biologist79/ESPuino/PCBs/Wemos Lolin32/Pictures/3d-Model downside.jpg

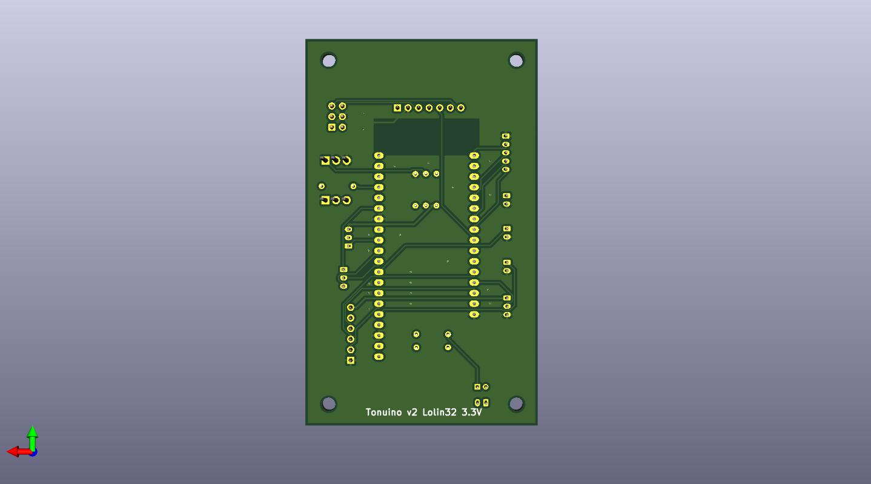
PCBs/Wemos Lolin32/Pictures/3d-Model downside.jpg
