biologist79/ESPuino/PCBs/Wemos Lolin32/Pictures/3d-Model upside.jpg

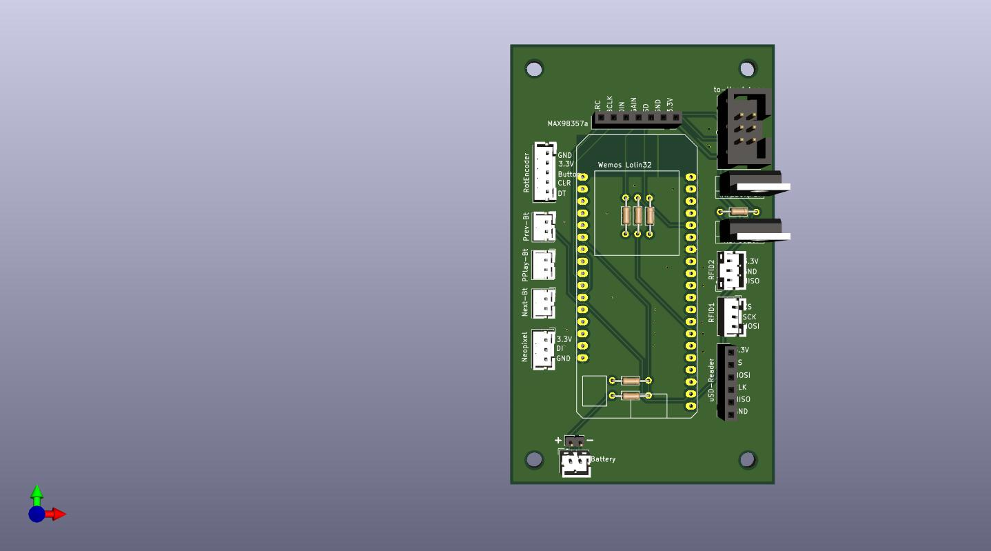
PCBs/Wemos Lolin32/Pictures/3d-Model upside.jpg
