biologist79/ESPuino/pictures/Pullup-removal.jpg

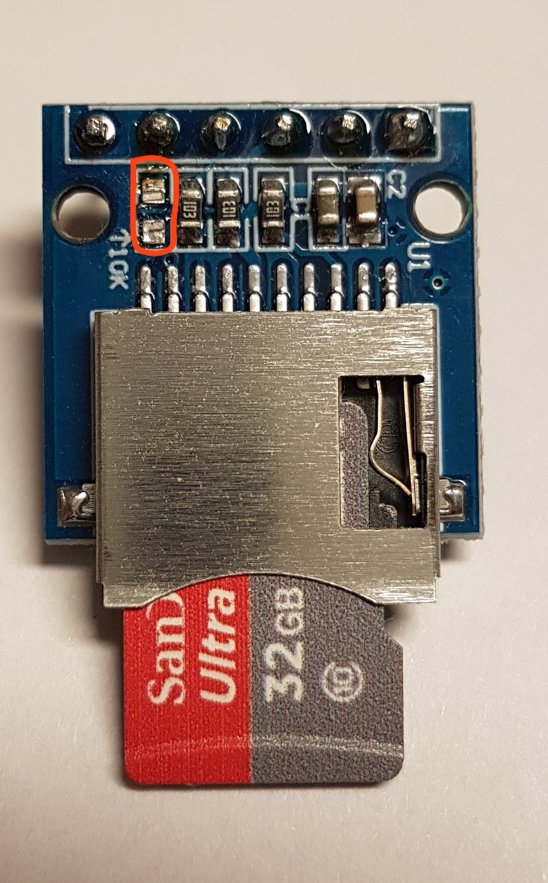
pictures/Pullup-removal.jpg
