biologist79/ESPuino/src/AudioPlayer.cpp

#include <Arduino.h>
#include "settings.h"

#include "AudioPlayer.h"

#include "Audio.h"
#include "Bluetooth.h"
#include "Cmd.h"
#include "Common.h"
#include "EnumUtils.h"
#include "Led.h"
#include "Log.h"
#include "MediaHub.h"
#include "MemX.h"
#include "Mqtt.h"
#include "Port.h"
#include "Queues.h"
#include "Rfid.h"
#include "RotaryEncoder.h"
#include "SdCard.h"
#include "System.h"
#include "VolumeCurveLut.h"
#include "Web.h"
#include "Wlan.h"
#include "main.h"
#include "strnatcmp.h"

#include <algorithm>
#include <atomic>
#include <cmath>
#include <esp_task_wdt.h>
#include <freertos/task.h>
#include <random>

// Allocate gPlayProperties in PSRAM if available
EXT_RAM_BSS_ATTR playProps gPlayProperties;

// Pending relative seek in seconds, written from the button/rotary/web tasks and drained by the audio loop.
static std::atomic<int16_t> AudioPlayer_PendingSeekSeconds {0};

void AudioPlayer_AddSeekOffset(const int16_t seconds) {
	AudioPlayer_PendingSeekSeconds.fetch_add(seconds, std::memory_order_relaxed);
}

// Seek-preview (rotary gesture, CMD_SEEK_PREVIEW): turning moves a not-yet-committed target position
// instead of jumping immediately; committed via the existing SEEK_POS_PERCENT path once the encoder is
// idle for a configurable delay, or immediately on release (see RotaryEncoder.cpp). currentRelPos must
// never be touched before the commit -- it also drives the LED progress ring, and writing the preview
// target into it early would make played-back position look like it already jumped.
static std::atomic<bool> AudioPlayer_SeekPreviewActive {false};
static std::atomic<uint8_t> AudioPlayer_SeekPreviewTargetPercent {0};
static double AudioPlayer_SeekPreviewTargetExact = 0.0; // full precision; only ever touched by the loop() task
static uint32_t AudioPlayer_SeekPreviewLastInputMs = 0; // only ever touched by the loop() task
// Cached once per gesture (in Start()), not re-read from NVS on every AudioPlayer_Loop() iteration/detent:
// the idle-commit check below runs on every single loop() cycle for as long as a gesture is held, and a
// NVS getUShort/getUChar still costs a mutex lock + key lookup each time even though it's RAM-cached.
static uint16_t AudioPlayer_SeekPreviewDelayMsCached = 2000;
static uint8_t AudioPlayer_SeekPreviewSweepCached = 40;

void AudioPlayer_SeekPreviewStart(void) {
	if (gPlayProperties.audioFileDuration == 0) {
		return; // no meaningful target for webstreams / unknown-length content
	}
	AudioPlayer_SeekPreviewDelayMsCached = gPrefsSettings.getUShort("seekPrevDelay", 2000);
	AudioPlayer_SeekPreviewSweepCached = gPrefsSettings.getUChar("seekPrevSweep", 40);
	if (AudioPlayer_SeekPreviewSweepCached < 1) {
		AudioPlayer_SeekPreviewSweepCached = 1; // guard against divide-by-zero in AudioPlayer_SeekPreviewAdjust
	}
	AudioPlayer_SeekPreviewTargetExact = gPlayProperties.currentRelPos; // start from where playback is, not 0
	AudioPlayer_SeekPreviewTargetPercent.store(static_cast<uint8_t>(std::lround(AudioPlayer_SeekPreviewTargetExact)), std::memory_order_relaxed);
	AudioPlayer_SeekPreviewLastInputMs = millis();
	AudioPlayer_SeekPreviewActive.store(true, std::memory_order_relaxed);
}

void AudioPlayer_SeekPreviewAdjust(const int32_t detents) {
	if (!AudioPlayer_SeekPreviewActive.load(std::memory_order_relaxed)) {
		return;
	}
	AudioPlayer_SeekPreviewTargetExact = std::clamp(AudioPlayer_SeekPreviewTargetExact + (detents * 100.0 / AudioPlayer_SeekPreviewSweepCached), 0.0, 100.0);
	AudioPlayer_SeekPreviewTargetPercent.store(static_cast<uint8_t>(std::lround(AudioPlayer_SeekPreviewTargetExact)), std::memory_order_relaxed);
	AudioPlayer_SeekPreviewLastInputMs = millis();
}

void AudioPlayer_SeekPreviewCommit(void) {
	if (!AudioPlayer_SeekPreviewActive.load(std::memory_order_relaxed)) {
		return;
	}
	gPlayProperties.currentRelPos = AudioPlayer_SeekPreviewTargetPercent.load(std::memory_order_relaxed);
	gPlayProperties.seekmode = SEEK_POS_PERCENT;
	AudioPlayer_SeekPreviewActive.store(false, std::memory_order_relaxed);
}

void AudioPlayer_SeekPreviewCancel(void) {
	AudioPlayer_SeekPreviewActive.store(false, std::memory_order_relaxed);
}

bool AudioPlayer_IsSeekPreviewActive(void) {
	return AudioPlayer_SeekPreviewActive.load(std::memory_order_relaxed);
}

uint8_t AudioPlayer_GetSeekPreviewTargetPercent(void) {
	return AudioPlayer_SeekPreviewTargetPercent.load(std::memory_order_relaxed);
}

// Playlist
static playlistSortMode AudioPlayer_PlaylistSortMode = AUDIOPLAYER_PLAYLIST_SORT_MODE_DEFAULT;

// Volume
static uint8_t AudioPlayer_CurrentVolume = AUDIOPLAYER_VOLUME_INIT;
static uint8_t AudioPlayer_MaxVolume = AUDIOPLAYER_VOLUME_MAX;
static uint8_t AudioPlayer_MaxVolumeSpeaker = AUDIOPLAYER_VOLUME_MAX;
static uint8_t AudioPlayer_MinVolume = AUDIOPLAYER_VOLUME_MIN;
static uint8_t AudioPlayer_InitVolume = AUDIOPLAYER_VOLUME_INIT;
// Night-mode volume limit, see AudioPlayer_ApplyNightVolumeCap(). The cap is purely transient: armed
// when night mode starts, dropped when it ends, never persisted -- night mode is always off after a
// restart anyway.
static uint8_t AudioPlayer_NightVolumeCap = 0u; // 0 = no cap active
static bool AudioPlayer_NightVolumeLimitEnabled = false;

// current playtime
uint32_t AudioPlayer_CurrentTime = 0;
uint32_t AudioPlayer_FileDuration = 0;

// Playtime stats
time_t playTimeSecTotal = 0;
time_t playTimeSecSinceStart = 0;

// current station logo url
static String AudioPlayer_StationLogoUrl;

#ifdef HEADPHONE_ADJUST_ENABLE
static bool AudioPlayer_HeadphoneLastDetectionState;
static uint32_t AudioPlayer_HeadphoneLastDetectionTimestamp = 0u;
static uint8_t AudioPlayer_MaxVolumeHeadphone = 11u; // Maximum volume that can be adjusted in headphone-mode (default; can be changed later via GUI)
#endif

static bool AudioPlayer_IsHeadphoneModeActive() {
#ifdef HEADPHONE_ADJUST_ENABLE
	const bool wiredHeadphoneConnected = !Audio_Detect_Mode_HP(Port_Read(HP_DETECT));
#else
	const bool wiredHeadphoneConnected = false;
#endif

	const bool bluetoothHeadphoneConnected = (System_GetOperationMode() == OPMODE_BLUETOOTH_SOURCE) && Bluetooth_Device_Connected();

	return wiredHeadphoneConnected || bluetoothHeadphoneConnected;
}

// dummy class to allocate audio object in PSRAM if available
class AudioCustom : public Audio {
public:
	void *operator new(size_t size) {
		return psramFound() ? ps_malloc(size) : malloc(size);
	}
};

Audio *audio = nullptr;

// new old varibles
constexpr uint32_t playbackTimeout = 2000;
uint32_t playbackTimeoutStart = millis();
uint8_t currentVolume;
BaseType_t trackQStatus = pdFAIL;
uint8_t trackCommand = NO_ACTION;
bool audioReturnCode;
uint32_t AudioPlayer_LastPlaytimeStatsTimestamp = 0u;
// Announcement state (see AudioPlayer_PlayAnnouncement). The decoder is briefly pointed at another
// file while gPlayProperties -- playlist, track number, play mode -- stays exactly as it is, so the
// only thing that has to be remembered is the position inside the interrupted track.
static uint32_t AudioPlayer_announcementResumePos = 0; // seconds into the interrupted track
static uint32_t AudioPlayer_announcementStartedAt = 0; // millis() when it started, for the watchdog
// Backstop in case evt_eof never arrives (a file that opens but decodes to nothing): without it the
// music would stay silent forever, which is worse than a crash because nothing points at the cause.
static constexpr uint32_t announcementTimeoutMs = 30000;

static uint32_t AudioPlayer_resumeSeekPendingSecs = 0; // deferred resume-seek target (seconds); 0 = none pending (declared early: used by the audio_info evt_bitrate callback above AudioPlayer_Loop)
Playlist *newPlayList = nullptr;
bool newPlayListAvailable = false;

static bool AudioPlayer_UploadActive = false;
static bool AudioPlayer_WasPausedBeforeUpload = false; // remember pre-upload pause state
static bool gResetOldRfidOnIdle = false; // release the "don't accept same rfid twice"-lock on next idle-state

// Remember an RFID-tag whose webstream could not be started because WiFi is not (yet) connected, so it can
// be re-injected into the RFID-queue once WiFi is up (see handleWifiStateConnectionSuccess() in Wlan.cpp).
static void AudioPlayer_RememberRfidForWifiRetry(const char *rfidTagId) {
	strncpy(gRetryRfidTagId, rfidTagId, cardIdStringSize - 1);
	gRetryRfidTagId[cardIdStringSize - 1] = '\0';
	gRetryRfidOnWifiConnect = true;
}

// "Arm" the release of the dontAcceptRfidTwice-lock: called by the RFID-handler the moment a new
// tag is accepted, it records that this playback-attempt happened. The lock is then actually released the
// next time the player becomes idle (see AudioPlayer_Cyclic()), which re-allows the same tag to be applied
// again. Arming on acceptance - rather than on playback becoming active - is deliberate: it ensures the
// release still fires even if the very first track fails immediately (e.g. a webstream applied before WiFi
// is connected), which would otherwise leave the tag locked forever.
void AudioPlayer_ArmRfidResetOnIdle(void) {
	gResetOldRfidOnIdle = true;
}

static void AudioPlayer_HeadphoneVolumeManager(void);
static std::optional<Playlist *> AudioPlayer_ReturnPlaylistFromWebstream(const char *_webUrl);
static bool AudioPlayer_ArrSortHelper_strcmp(const char *a, const char *b);
static bool AudioPlayer_ArrSortHelper_strnatcmp(const char *a, const char *b);
static bool AudioPlayer_ArrSortHelper_strnatcasecmp(const char *a, const char *b);
static void AudioPlayer_SortPlaylist(Playlist *playlist);
static void AudioPlayer_RandomizePlaylist(Playlist *playlist);
static size_t AudioPlayer_NvsRfidWriteWrapper(const char *_rfidCardId, const uint32_t _playPosition, const uint8_t _playMode, const uint16_t _trackLastPlayed);
static void AudioPlayer_ClearCover(void);
static void audio_id3image(File &file, const size_t pos, const size_t size);
static void audio_oggimage(File &file, std::vector<uint32_t> v);

void AudioPlayer_NotifyUploadStart(void) {
	if (AudioPlayer_UploadActive) {
		return; // already suspended – ignore nested calls
	}
	AudioPlayer_UploadActive = true;
	if (!gPlayProperties.pausePlay && gPlayProperties.playMode != NO_PLAYLIST && gPlayProperties.playMode != BUSY) {
		AudioPlayer_WasPausedBeforeUpload = false;
		audio->pauseResume();
	} else {
		AudioPlayer_WasPausedBeforeUpload = true; // was already paused / idle
	}
}

void AudioPlayer_NotifyUploadEnd(void) {
	if (!AudioPlayer_UploadActive) {
		return;
	}
	if (!AudioPlayer_WasPausedBeforeUpload) {
		audio->pauseResume();
	}
	AudioPlayer_UploadActive = false;
}

void Audio_InfoCallback(Audio::msg_t m) {
	switch (m.e) {
		case Audio::evt_info: {
			// Log_Printf(LOGLEVEL_INFO, "info:         %s", m.msg); // disabled to reduce log especially from files with numerous comments
			if (startsWith((char *) m.msg, "slow stream, dropouts")) {
				// websocket notify for slow stream
				Web_SendWebsocketData(0, WebsocketCodeType::Dropout);
			}
			break;
		}
		case Audio::evt_eof: { // end of file
			Log_Printf(LOGLEVEL_INFO, "end of file:  %s", m.msg);
			gPlayProperties.trackFinished = true;
			gPlayProperties.currentSpeechActive = false;
			break;
		}
		case Audio::evt_bitrate: {
			Log_Printf(LOGLEVEL_INFO, "bitrate:      %s", m.msg);
			// Deferred audiobook resume-seek. connecttoFS(fileStartTime) only seeks files whose
			// Xing/VBR header sets m_nominal_bitrate; headerless CBR audiobooks are never seeked and
			// restart from 0. This event fires once the measured average bitrate has *stabilised*, so
			// setAudioPlayTime() now lands accurately and the lib re-syncs the reported play-time to
			// match (seeking earlier, before the bitrate settles, both mis-positions and desyncs the
			// clock). Guards: only when a resume is pending, the target is within the file, and we are
			// not already there (a VBR file the lib already positioned at connect).
			if (AudioPlayer_resumeSeekPendingSecs > 0 && audio != nullptr) {
				const uint32_t target = AudioPlayer_resumeSeekPendingSecs;
				AudioPlayer_resumeSeekPendingSecs = 0; // one-shot regardless of outcome
				if (target < audio->getAudioFileDuration() && target > audio->getAudioCurrentTime() + 3) {
					if (audio->setAudioPlayTime(target)) {
						Log_Printf(LOGLEVEL_NOTICE, "Resume: deferred seek to position %u", target);
					}
				}
			}
			break;
		}
		case Audio::evt_icyurl: {
			Log_Printf(LOGLEVEL_INFO, "icy URL:      %s", m.msg);
			if (m.msg && m.msg[0] != '\0' && AudioPlayer_StationLogoUrl.isEmpty()) {
				// has station homepage, get favicon url
				AudioPlayer_StationLogoUrl = "https://www.google.com/s2/favicons?sz=256&domain_url=" + String(m.msg);
				// websocket and mqtt notify station logo has changed
				Web_SendWebsocketData(0, WebsocketCodeType::CoverImg);
			}
			break;
		}
		case Audio::evt_id3data: {
			if (!m.msg) {
				break;
			}
			// Log_Printf(LOGLEVEL_INFO, "ID3 data:     %s", m.msg); // disabled to prevent log spam from files with numerous metadata
			// get title
			if (startsWith((char *) m.msg, "Title") || startsWith((char *) m.msg, "TITLE=") || startsWith((char *) m.msg, "title=")) { // ID3v1, ID3v2.3 and ID3v2.4: "Title:", VORBISCOMMENT: "TITLE=", "title=", "Title="
				int titleStart = 6;
				if (m.msg[5] == '/') { // ID3v2.2 "Title/Songname/Content description:"
					titleStart = 36;
				}
				if (gPlayProperties.playlist->size() > 1) {
					Audio_setTitle("(%u/%u): %s", gPlayProperties.currentTrackNumber + 1, gPlayProperties.playlist->size(), m.msg + titleStart);
				} else {
					Audio_setTitle("%s", m.msg + titleStart);
				}
			}
			break;
		}
		case Audio::evt_lasthost: { // stream URL played
			Log_Printf(LOGLEVEL_INFO, "last URL:     %s", m.msg);
			break;
		}
		case Audio::evt_name: { // station name or icy-name
			Log_Printf(LOGLEVEL_NOTICE, "station name: %s", m.msg);
			if (m.msg && m.msg[0] != '\0') {
				if (gPlayProperties.playlist->size() > 1) {
					Audio_setTitle("(%u/%u): %s", gPlayProperties.currentTrackNumber + 1, gPlayProperties.playlist->size(), m.msg);
				} else {
					Audio_setTitle("%s", m.msg);
				}
			}
			break;
		}
		case Audio::evt_streamtitle: {
			if (!gPlayProperties.isWebstream) {
				break; // prevents overwriting correct title for local files
			}
			Log_Printf(LOGLEVEL_INFO, "stream title: %s", m.msg);
			if (m.msg && m.msg[0] != '\0') {
				if (gPlayProperties.playlist->size() > 1) {
					Audio_setTitle("(%u/%u): %s", gPlayProperties.currentTrackNumber + 1, gPlayProperties.playlist->size(), m.msg);
				} else {
					Audio_setTitle("%s", m.msg);
				}
			}
			break;
		}
		case Audio::evt_icylogo: { // logo
			Log_Printf(LOGLEVEL_INFO, "icy logo:     %s", m.msg);
			if (m.msg && m.msg[0] != '\0') {
				AudioPlayer_StationLogoUrl = m.msg;
				// websocket and mqtt notify station logo has changed
				Web_SendWebsocketData(0, WebsocketCodeType::CoverImg);
			}
			break;
		}
		case Audio::evt_image: {
			if (!gPlayProperties.playlist || gPlayProperties.currentTrackNumber >= gPlayProperties.playlist->size()) {
				break;
			}
			const char *fileName = gPlayProperties.playlist->at(gPlayProperties.currentTrackNumber);
			File file = gFSystem.open(fileName, FILE_READ);
			if (!file) {
				Log_Printf(LOGLEVEL_ERROR, "Failed to open file: %s", fileName);
				break;
			}
			char fileType[4];
			if (file.readBytes(fileType, 4) == 4) {
				if (strncmp(fileType, "OggS", 4) == 0) {
					audio_oggimage(file, m.vec1);
				} else {
					audio_id3image(file, m.vec1[0], m.vec1[1]);
				}
			}
			file.close();
			break;
		}
		default: // ignored events: evt_icydescription, evt_lyrics, evt_log
			break;
	}
}

float Audio_GetVolume(float t) {
	uint8_t curve_type = gPrefsSettings.getUChar("volumeCurve", 0);

	// 1. Safety Checks
	if (curve_type >= VOL_LUT_CURVES) {
		curve_type = VOL_CURVE_PERCEPTUAL;
	}
	if (t <= 0.0f) {
		return pgm_read_float(&(VOLUME_TABLE[curve_type][0]));
	}

	// 2. Calculate indices
	float index_f = t * (VOL_LUT_STEPS - 1);
	int index = (int) index_f;

	// Safety clamp for the edge case where index_f is exactly 63.0
	if (index >= VOL_LUT_STEPS - 1) {
		return pgm_read_float(&(VOLUME_TABLE[curve_type][VOL_LUT_STEPS - 1]));
	}

	float fraction = index_f - (float) index;

	// 3. Interpolate
	float val1 = pgm_read_float(&(VOLUME_TABLE[curve_type][index]));
	float val2 = pgm_read_float(&(VOLUME_TABLE[curve_type][index + 1]));

	return val1 + (val2 - val1) * fraction;
}

// Applies the tone/equalizer gains and keeps the audio library's per-sample IIR tone filter enabled
// only while the equalizer is actually non-flat. With a flat EQ (all gains 0, the default) the filter
// would just pass the signal through unchanged, so running it per output sample is wasted CPU on core 1
// -- the same core loop() polls buttons/rotary on, which is why heavy decoders (AAC/m4a) starve input.
// See https://forum.espuino.de/t/keine-bedienung-bei-bestimmten-dateien-moeglich/4675
static void AudioPlayer_ApplyTone(int8_t gainLowPass, int8_t gainBandPass, int8_t gainHighPass) {
	audio->settings.IIR_FILTER = (gainLowPass != 0 || gainBandPass != 0 || gainHighPass != 0);
	audio->setTone(gainLowPass, gainBandPass, gainHighPass);
}

void AudioPlayer_Init(void) {
	// create audio object
	audio = new AudioCustom();

	// load playtime total from NVS
	playTimeSecTotal = gPrefsSettings.getULong("playTimeTotal", 0);

	uint8_t playListSortModeValue = gPrefsSettings.getUChar("PLSortMode", EnumUtils::underlying_value(AudioPlayer_PlaylistSortMode));
	AudioPlayer_PlaylistSortMode = EnumUtils::to_enum<playlistSortMode>(playListSortModeValue);

	uint32_t nvsInitialVolume;
	if (!gPrefsSettings.getBool("recoverVolBoot", false)) {
		// Get initial volume from NVS
		nvsInitialVolume = gPrefsSettings.getUInt("initVolume", 0);
	} else {
		// Get volume used at last shutdown
		nvsInitialVolume = gPrefsSettings.getUInt("previousVolume", 999);
		if (nvsInitialVolume == 999) {
			gPrefsSettings.putUInt("previousVolume", AudioPlayer_GetInitVolume());
			nvsInitialVolume = AudioPlayer_GetInitVolume();
		} else {
			Log_Println(rememberLastVolume, LOGLEVEL_ERROR);
		}
	}

	if (nvsInitialVolume) {
		AudioPlayer_SetInitVolume(nvsInitialVolume);
		Log_Printf(LOGLEVEL_INFO, restoredInitialLoudnessFromNvs, nvsInitialVolume);
	} else {
		gPrefsSettings.putUInt("initVolume", AudioPlayer_GetInitVolume());
		Log_Println(wroteInitialLoudnessToNvs, LOGLEVEL_ERROR);
	}

	// Get maximum volume for speaker from NVS
	uint32_t nvsMaxVolumeSpeaker = gPrefsSettings.getUInt("maxVolumeSp", 0);
	if (nvsMaxVolumeSpeaker) {
		AudioPlayer_SetMaxVolumeSpeaker(nvsMaxVolumeSpeaker);
		AudioPlayer_SetMaxVolume(nvsMaxVolumeSpeaker);
		Log_Printf(LOGLEVEL_INFO, restoredMaxLoudnessForSpeakerFromNvs, nvsMaxVolumeSpeaker);
	} else {
		// Set max volume to max per default. Can be adjusted later via webinterface.
		gPrefsSettings.putUInt("maxVolumeSp", 21);
		Log_Println(wroteMaxLoudnessForSpeakerToNvs, LOGLEVEL_ERROR);
	}

	// Get minimum volume from NVS. Unlike the max values, 0 (= AUDIOPLAYER_VOLUME_MIN) is a perfectly
	// valid setting and in fact the default, so a plain read-with-default is used instead of the
	// "0 means unset, write default" pattern above. AudioPlayer_SetVolume() clamps every volume change
	// to this floor, so a non-zero value takes effect for all volume sources (rotary, buttons, BT, web).
	AudioPlayer_SetMinVolume(gPrefsSettings.getUInt("minVolume", AUDIOPLAYER_VOLUME_MIN));

	// Night-mode volume limit: off by default, so nothing changes for existing devices.
	AudioPlayer_NightVolumeLimitEnabled = gPrefsSettings.getBool("nightVolLimit", false);

#ifdef HEADPHONE_ADJUST_ENABLE
	#if (HP_DETECT >= 0 && HP_DETECT <= MAX_GPIO)
	pinMode(HP_DETECT, INPUT_PULLUP);
	#endif
	AudioPlayer_HeadphoneLastDetectionState = Audio_Detect_Mode_HP(Port_Read(HP_DETECT));

	// Get maximum volume for headphone from NVS
	uint32_t nvsAudioPlayer_MaxVolumeHeadphone = gPrefsSettings.getUInt("maxVolumeHp", 0);
	if (nvsAudioPlayer_MaxVolumeHeadphone) {
		AudioPlayer_MaxVolumeHeadphone = nvsAudioPlayer_MaxVolumeHeadphone;
		Log_Printf(LOGLEVEL_INFO, restoredMaxLoudnessForHeadphoneFromNvs, nvsAudioPlayer_MaxVolumeHeadphone);
	} else {
		// Set max volume to max per default. Can be adjusted later via webinterface.
		gPrefsSettings.putUInt("maxVolumeHp", 21);
		Log_Println(wroteMaxLoudnessForHeadphoneToNvs, LOGLEVEL_ERROR);
	}
#endif
	// Adjust volume depending on headphone is connected and volume-adjustment is enabled
	AudioPlayer_SetupVolumeAndAmps();

	// initialize gPlayProperties
	gPlayProperties = {};
	gPlayProperties.playlistFinished = true;
	gPlayProperties.jumpToFolderTrack = -1;
	gPlayProperties.gainLowPass = 0;
	gPlayProperties.gainBandPass = 0;
	gPlayProperties.gainHighPass = 0;

	// clear title and cover image
	gPlayProperties.title[0] = '\0';
	gPlayProperties.coverFilePos = 0;
	AudioPlayer_StationLogoUrl = "";
	gPlayProperties.playlist = allocatePlaylist();
	gPlayProperties.SavePlayPosRfidChange = gPrefsSettings.getBool("savePosRfidChge", false); // SAVE_PLAYPOS_WHEN_RFID_CHANGE
	gPlayProperties.savePosIntervalSecs = gPrefsSettings.getUShort("savePosIntv", 0); // SAVE_PLAYPOS_INTERVAL (periodic checkpoint, 0 = off)
	gPlayProperties.pauseOnMinVolume = gPrefsSettings.getBool("pauseOnMinVol", false); // PAUSE_ON_MIN_VOLUME
	gPlayProperties.pauseIfRfidRemoved = gPrefsSettings.getBool("pauseRfidRem", false); // PAUSE_WHEN_RFID_REMOVED
	gPlayProperties.dontAcceptRfidTwice = gPrefsSettings.getBool("dAccRfidTwice", false); // DONT_ACCEPT_SAME_RFID_TWICE
	gPlayProperties.resumeOnSameRfid = gPrefsSettings.getBool("p2pSameRfid", false); // RESUME_ON_SAME_RFID
	if (gPlayProperties.pauseIfRfidRemoved) {
		// ignore feature silently if pauseIfRfidRemoved is active
		Log_Println("pauseIfRfidRemoved is enabled -> deactivate dontAcceptRfidTwice", LOGLEVEL_NOTICE);
		gPlayProperties.dontAcceptRfidTwice = false;
	}

#ifdef I2S_COMM_FMT_LSB_ENABLE
	audio->setI2SCommFMT_LSB(true);
#endif

	// Raise the boot volume to the configured minimum if it sits below it: the init/remembered volume is
	// applied directly here (not via AudioPlayer_SetVolume(), which is where the min-clamp lives), so
	// without this the box could start below its own floor until the first volume change.
	AudioPlayer_CurrentVolume = std::max(AudioPlayer_GetInitVolume(), AudioPlayer_GetMinVolume());
	// DMA-settings must be adjusted before setting the pinout
	if (System_GetOperationMode() == OPMODE_BLUETOOTH_SOURCE || System_GetOperationMode() == OPMODE_BLUETOOTH_SINK) {
		audio->settings.DMA_FRAME_NUM = 192; // not too high, to safe some SRAM
	} else {
		// just use default-values
	}

	audio->setPinout(I2S_BCLK, I2S_LRC, I2S_DOUT);

	// must be called after setPinout() to take effect
	if (System_GetOperationMode() == OPMODE_BLUETOOTH_SOURCE) {
		audio->setOutputSampleRate(Audio::OutputSR_t::SR_44100);
	}

	audio->setVolumeSteps(AUDIOPLAYER_VOLUME_MAX);
	audio->setVolumeCurve(Audio_GetVolume);
	audio->setVolume(AudioPlayer_CurrentVolume);
	audio->forceMono(gPlayProperties.currentPlayMono);
	AudioPlayer_ApplyTone(
		gPrefsSettings.getChar("gainLowPass", 0),
		gPrefsSettings.getChar("gainBandPass", 0),
		gPrefsSettings.getChar("gainHighPass", 0));

	// ESPuino never reads the audio library's VU level, so skip its per-sample computation entirely
	// (frees CPU on the shared core -- see AudioPlayer_ApplyTone() and forum thread #4675).
	audio->settings.VU_LEVEL = false;

	audio->setAudioTaskCore(1);
	audio->audio_info_callback = Audio_InfoCallback;
}

void AudioPlayer_Exit(void) {
	Log_Println("shutdown audioplayer..", LOGLEVEL_NOTICE);
	// save playtime total to NVS
	playTimeSecTotal += playTimeSecSinceStart;
	gPrefsSettings.putULong("playTimeTotal", playTimeSecTotal);
	// Make sure last playposition for audiobook is saved when playback is active while shutdown was initiated
	if (gPrefsSettings.getBool("savePosShutdown", false) && !gPlayProperties.pausePlay && (gPlayProperties.playMode == AUDIOBOOK || gPlayProperties.playMode == AUDIOBOOK_LOOP || gPlayProperties.playMode == AUDIOBOOK_RECURSIVE)) {
		AudioPlayer_SetTrackControl(PAUSEPLAY);
		// Call the loop explicitely to make sure that PAUSE is set (because this saves the current playpos)
		AudioPlayer_Loop();
	}
	delete audio;
	audio = nullptr;
}

static uint32_t lastPlayingTimestamp = 0;
static uint32_t AudioPlayer_lastCheckpointTimestamp = 0; // millis() of the last periodic play-position checkpoint
static uint32_t AudioPlayer_lastCheckpointPos = 0; // last checkpointed play-position (seconds) for dedup

void AudioPlayer_Cyclic(void) {
	if (AudioPlayer_UploadActive) {
		return;
	}

	AudioPlayer_HeadphoneVolumeManager();
	if ((millis() - lastPlayingTimestamp >= 1000) && gPlayProperties.playMode != NO_PLAYLIST && gPlayProperties.playMode != BUSY && !gPlayProperties.pausePlay) {
		// audio is playing, update the playtime since start
		lastPlayingTimestamp = millis();
		playTimeSecSinceStart += 1;

		// Periodic play-position checkpoint for long audiobooks (opt-in via savePosIntv, 0 = off).
		// Bounds the position lost to an *ungraceful* power-off -- dead battery, yanked plug, watchdog
		// reboot -- while the card is still on the reader. The graceful paths (pause, card-removal,
		// clean shutdown) already save, but only on a clean transition; nothing saves if power just
		// disappears mid-file, so playback restarts from the start of that file on resume. Gated on
		// audiobook mode (saveLastPlayPosition) plus a minimum file length, so short/split tracks --
		// which already checkpoint at every track boundary -- don't needlessly wear the NVS flash.
		constexpr uint32_t checkpointMinDurationSecs = 300; // below 5 min, per-track boundary saves suffice
		if (gPlayProperties.savePosIntervalSecs > 0 && gPlayProperties.saveLastPlayPosition && !gPlayProperties.isWebstream
			&& audio != nullptr && audio->getAudioFileDuration() >= checkpointMinDurationSecs
			&& (millis() - AudioPlayer_lastCheckpointTimestamp >= (uint32_t) gPlayProperties.savePosIntervalSecs * 1000)) {
			uint32_t checkpointPos = audio->getAudioCurrentTime();
			if (checkpointPos != AudioPlayer_lastCheckpointPos) { // dedup: skip if position hasn't advanced (e.g. stalled)
				AudioPlayer_NvsRfidWriteWrapper(gPlayProperties.playRfidTag, checkpointPos, gPlayProperties.playMode, gPlayProperties.currentTrackNumber);
				AudioPlayer_lastCheckpointPos = checkpointPos;
			}
			AudioPlayer_lastCheckpointTimestamp = millis();
		}
	}

	// Actual loop stuff
	AudioPlayer_Loop();
}

// Wrapper-function to reverse detection of connected headphones.
// Normally headphones are supposed to be plugged in if a given GPIO/channel is LOW/false.
bool Audio_Detect_Mode_HP(bool _state) {
#ifndef DETECT_HP_ON_HIGH
	return _state;
#else
	return !_state;
#endif
}

playlistSortMode AudioPlayer_GetPlaylistSortMode(void) {
	return AudioPlayer_PlaylistSortMode;
}

bool AudioPlayer_SetPlaylistSortMode(playlistSortMode value) {
	AudioPlayer_PlaylistSortMode = value;
	size_t written = gPrefsSettings.putUChar("PLSortMode", EnumUtils::underlying_value(AudioPlayer_PlaylistSortMode));
	return (written == 1);
}

bool AudioPlayer_SetPlaylistSortMode(uint8_t value) {
	return AudioPlayer_SetPlaylistSortMode(EnumUtils::to_enum<playlistSortMode>(value));
}

uint8_t AudioPlayer_GetCurrentVolume(void) {
	return AudioPlayer_CurrentVolume;
}

void AudioPlayer_SetCurrentVolume(uint8_t value) {
	AudioPlayer_CurrentVolume = value;
}

uint8_t AudioPlayer_GetMaxVolume(void) {
	// The night cap is deliberately a separate layer on top of AudioPlayer_MaxVolume instead of a write
	// into it: that variable is recomputed from the speaker/headphone limits whenever the settings are
	// saved, a headphone is (un)plugged or the amps are set up, which would silently drop the cap.
	// Taking the minimum also keeps the lower headphone limit winning while headphones are connected.
	if (AudioPlayer_NightVolumeCap) {
		return std::min(AudioPlayer_MaxVolume, AudioPlayer_NightVolumeCap);
	}
	return AudioPlayer_MaxVolume;
}

void AudioPlayer_SetMaxVolume(uint8_t value) {
	AudioPlayer_MaxVolume = value;
}

uint8_t AudioPlayer_GetMaxVolumeSpeaker(void) {
	return AudioPlayer_MaxVolumeSpeaker;
}

void AudioPlayer_SetMaxVolumeSpeaker(uint8_t value) {
	AudioPlayer_MaxVolumeSpeaker = value;
}

void AudioPlayer_ApplyMaxVolumes(uint8_t speaker, uint8_t headphone) {
	AudioPlayer_MaxVolumeSpeaker = speaker;

#ifdef HEADPHONE_ADJUST_ENABLE
	AudioPlayer_MaxVolumeHeadphone = headphone;
	AudioPlayer_MaxVolume = AudioPlayer_IsHeadphoneModeActive() ? AudioPlayer_MaxVolumeHeadphone : AudioPlayer_MaxVolumeSpeaker;
#else
	(void) headphone;
	AudioPlayer_MaxVolume = AudioPlayer_MaxVolumeSpeaker;
#endif

	if (AudioPlayer_CurrentVolume > AudioPlayer_MaxVolume) {
		AudioPlayer_SetVolume(AudioPlayer_MaxVolume);
	}
}

// Arms or lifts the night-mode volume ceiling; called by System_SetNightmode() on an actual state
// change. The ceiling is taken once, on activation, and then frozen: letting it follow the volume down
// would pin the user to whatever level they briefly dialled in during a quiet passage. A fixed limit
// configured up front was the obvious alternative, but audiobooks differ so much in loudness that it
// would have to be set very low -- and then corrected in the web interface all the time.
void AudioPlayer_ApplyNightVolumeCap(bool enabled) {
	if (!enabled) {
		AudioPlayer_NightVolumeCap = 0u;
		return;
	}
	if (!AudioPlayer_NightVolumeLimitEnabled) {
		return;
	}
	// No clamping needed at either end: the headroom keeps the cap at 1 or above, and a cap beyond the
	// regular maximum is folded away by the std::min() in AudioPlayer_GetMaxVolume().
	AudioPlayer_NightVolumeCap = AudioPlayer_GetCurrentVolume() + AUDIOPLAYER_NIGHT_VOLUME_HEADROOM;
	Log_Printf(LOGLEVEL_INFO, nightVolumeCapSet, AudioPlayer_NightVolumeCap);
}

void AudioPlayer_SetNightVolumeLimitEnabled(bool enabled) {
	AudioPlayer_NightVolumeLimitEnabled = enabled;
}

uint8_t AudioPlayer_GetMinVolume(void) {
	return AudioPlayer_MinVolume;
}

void AudioPlayer_SetMinVolume(uint8_t value) {
	AudioPlayer_MinVolume = value;
}

uint8_t AudioPlayer_GetInitVolume(void) {
	return AudioPlayer_InitVolume;
}

void AudioPlayer_SetInitVolume(uint8_t value) {
	AudioPlayer_InitVolume = value;
}

time_t AudioPlayer_GetPlayTimeAllTime(void) {
	return (playTimeSecTotal + playTimeSecSinceStart) * 1000;
}

time_t AudioPlayer_GetPlayTimeSinceStart(void) {
	return (playTimeSecSinceStart * 1000);
}

uint32_t AudioPlayer_GetCurrentTime(void) {
	return AudioPlayer_CurrentTime;
}

uint32_t AudioPlayer_GetFileDuration(void) {
	return AudioPlayer_FileDuration;
}

String AudioPlayer_GetStationLogoUrl(void) {
	return AudioPlayer_StationLogoUrl;
}

void Audio_setTitle(const char *format, ...) {
	if (gPlayProperties.announcementActive) {
		// Leave the interrupted track's title in place: the announcement must not show up anywhere.
		return;
	}
	va_list args;
	va_start(args, format);
	vsnprintf(gPlayProperties.title, sizeof(gPlayProperties.title) / sizeof(gPlayProperties.title[0]), format, args);
	va_end(args);

	// notify web ui and mqtt
	Web_SendWebsocketData(0, WebsocketCodeType::TrackInfo);
#ifdef MQTT_ENABLE
	publishMqtt(topicTrack, gPlayProperties.title, false);
#endif
}

// Interrupts playback with a single local file and returns to the exact position afterwards; see
// AudioPlayer.h. Everything the outside world reads -- title, position, progress -- is frozen for the
// duration, and the playlist is never touched, so the interruption leaves no trace anywhere.
bool AudioPlayer_PlayAnnouncement(const char *path) {
	if (audio == nullptr || path == nullptr || path[0] == '\0' || gPlayProperties.announcementActive) {
		return false;
	}
	// Deliberately checked before the "is anything playing" guard below: a wrong path has to be reported
	// even while the player sits idle, otherwise a typo stays invisible until someone happens to be
	// listening -- and the user is left searching. Still evaluated before stopSong(), so a missing file
	// never costs the listener a gap of silence either.
	if (!gFSystem.exists(path)) {
		Log_Printf(LOGLEVEL_ERROR, announcementFileMissing, path);
		System_IndicateError();
		return false;
	}
	// Only interrupt something that is actually playing. Idle or paused there is nothing to return to,
	// and in Bluetooth-sink mode ESPuino does not drive the decoder at all.
	if (gPlayProperties.playMode == NO_PLAYLIST || gPlayProperties.playlistFinished || gPlayProperties.pausePlay) {
		return false;
	}
	if (System_GetOperationMode() != OPMODE_NORMAL) {
		return false;
	}

	AudioPlayer_announcementResumePos = audio->stopSong(); // stops the decoder and yields the position
	AudioPlayer_announcementStartedAt = millis();
	gPlayProperties.announcementActive = true;

	if (!audio->connecttoFS(gFSystem, gFSystem.rawPath(path).c_str())) {
		// Nothing is playing now, so evt_eof would never arrive on its own. Hand it to the loop, which
		// takes the announcement branch and puts the interrupted track straight back on.
		Log_Printf(LOGLEVEL_ERROR, announcementFailed, path);
		System_IndicateError();
		gPlayProperties.trackFinished = true;
		return false;
	}
	Log_Printf(LOGLEVEL_NOTICE, announcementPlaying, path);
	return true;
}

// Set maxVolume depending on headphone-adjustment is enabled and headphone is/is not connected
// Enable/disable PA/HP-amps initially
void AudioPlayer_SetupVolumeAndAmps(void) {
	gPlayProperties.currentPlayMono = gPrefsSettings.getBool("playMono", false);
	gPlayProperties.newPlayMono = gPrefsSettings.getBool("playMono", false);

#ifndef HEADPHONE_ADJUST_ENABLE
	AudioPlayer_MaxVolume = AudioPlayer_MaxVolumeSpeaker;
	// If automatic HP-detection is not used, we enabled both (PA / HP) if defined
	#ifdef GPIO_PA_EN
	Port_Write(GPIO_PA_EN, true, true);
	#endif
	#ifdef GPIO_HP_EN
	Port_Write(GPIO_HP_EN, true, true);
	#endif
#else

	if (!AudioPlayer_IsHeadphoneModeActive()) {
		AudioPlayer_MaxVolume = AudioPlayer_MaxVolumeSpeaker; // 1 if headphone is not connected
	#ifdef GPIO_PA_EN
		Port_Write(GPIO_PA_EN, true, true);
	#endif
	#ifdef GPIO_HP_EN
		Port_Write(GPIO_HP_EN, false, true);
	#endif
	} else {
		AudioPlayer_MaxVolume = AudioPlayer_MaxVolumeHeadphone; // 0 if headphone is connected (put to GND)
		gPlayProperties.newPlayMono = false; // always stereo for headphones!

	#ifdef GPIO_PA_EN
		Port_Write(GPIO_PA_EN, false, true);
	#endif
	#ifdef GPIO_HP_EN
		Port_Write(GPIO_HP_EN, true, true);
	#endif
	}
	Log_Printf(LOGLEVEL_INFO, maxVolumeSet, AudioPlayer_MaxVolume);
	return;
#endif
}

void AudioPlayer_HeadphoneVolumeManager(void) {
#ifdef HEADPHONE_ADJUST_ENABLE
	const bool currentHeadPhoneDetectionState = Audio_Detect_Mode_HP(Port_Read(HP_DETECT));

	if (AudioPlayer_HeadphoneLastDetectionState != currentHeadPhoneDetectionState && (millis() - AudioPlayer_HeadphoneLastDetectionTimestamp >= headphoneLastDetectionDebounce)) {
		if (!AudioPlayer_IsHeadphoneModeActive()) {
			AudioPlayer_MaxVolume = AudioPlayer_MaxVolumeSpeaker;
			gPlayProperties.newPlayMono = gPrefsSettings.getBool("playMono", false);

	#ifdef GPIO_PA_EN
			Port_Write(GPIO_PA_EN, true, false);
	#endif
	#ifdef GPIO_HP_EN
			Port_Write(GPIO_HP_EN, false, false);
	#endif
		} else {
			AudioPlayer_MaxVolume = AudioPlayer_MaxVolumeHeadphone;
			gPlayProperties.newPlayMono = false; // Always stereo for headphones
			if (AudioPlayer_GetCurrentVolume() > AudioPlayer_MaxVolume) {
				AudioPlayer_SetVolume(AudioPlayer_MaxVolume); // Lower volume for headphone if headphone's maxvolume is exceeded by volume set in speaker-mode
			}

	#ifdef GPIO_PA_EN
			Port_Write(GPIO_PA_EN, false, false);
	#endif
	#ifdef GPIO_HP_EN
			Port_Write(GPIO_HP_EN, true, false);
	#endif
		}
		AudioPlayer_HeadphoneLastDetectionState = currentHeadPhoneDetectionState;
		AudioPlayer_HeadphoneLastDetectionTimestamp = millis();
		Log_Printf(LOGLEVEL_INFO, maxVolumeSet, AudioPlayer_MaxVolume);
	}
#endif
}

// Function to play music as task
void AudioPlayer_Loop() {
	// Update playtime stats every 250 ms. Frozen while an announcement runs, so the web interface keeps
	// showing the interrupted track's position instead of the announcement's.
	if (!gPlayProperties.announcementActive && (millis() - AudioPlayer_LastPlaytimeStatsTimestamp) > 250) {
		AudioPlayer_LastPlaytimeStatsTimestamp = millis();
		// Update current playtime and duration
		AudioPlayer_CurrentTime = audio->getAudioCurrentTime();
		AudioPlayer_FileDuration = audio->getAudioFileDuration();
		// Calculate relative position in file (for trackprogress neopixel & web-ui)
		gPlayProperties.audioFileDuration = AudioPlayer_FileDuration;
		if (!gPlayProperties.playlistFinished && AudioPlayer_FileDuration > 0) {
			// for local files and web files with known size
			if (!gPlayProperties.pausePlay && (gPlayProperties.seekmode != SEEK_POS_PERCENT)) { // To progress necessary when paused
				gPlayProperties.currentRelPos = ((float) audio->getAudioCurrentTime() / audio->getAudioFileDuration()) * 100.0f;
			}
		} else {
			if (gPlayProperties.isWebstream && (System_GetOperationMode() != OPMODE_BLUETOOTH_SINK) && (audio->getInBufferSize() > 0)) {
				// calc current fillbuffer percent for webstream with unknown size/end
				gPlayProperties.currentRelPos = (double) (audio->inBufferFilled() / (double) audio->getInBufferSize()) * 100;
			} else {
				gPlayProperties.currentRelPos = 0;
			}
		}
	}

	if (gPlayProperties.announcementActive && (millis() - AudioPlayer_announcementStartedAt) > announcementTimeoutMs) {
		Log_Println(announcementTimeout, LOGLEVEL_ERROR);
		System_IndicateError();
		gPlayProperties.trackFinished = true; // handed to the branch below, which restores playback
	}

	if (newPlayListAvailable || gPlayProperties.trackFinished || trackCommand != NO_ACTION) {
		if (newPlayListAvailable) {
			newPlayListAvailable = false;
			// A freshly tapped card supersedes a running announcement: there is no longer anything to
			// return to, so drop it without restoring.
			gPlayProperties.announcementActive = false;
			audio->stopSong();

			// destroy the old playlist and assign the new one
			freePlaylist(gPlayProperties.playlist);
			gPlayProperties.playlist = newPlayList;
			Log_Printf(LOGLEVEL_NOTICE, newPlaylistReceived, gPlayProperties.playlist->size());
			Log_Printf(LOGLEVEL_DEBUG, "Free heap: %u", ESP.getFreeHeap());
			playbackTimeoutStart = millis();
			gPlayProperties.pausePlay = false;
			gPlayProperties.trackFinished = false;
			gPlayProperties.playlistFinished = false;
#ifdef MQTT_ENABLE
			publishMqtt(topicPausePlay, "play", false);
			publishMqtt(topicPlaymode, static_cast<uint32_t>(gPlayProperties.playMode), false);
			publishMqtt(topicRepeatMode, static_cast<uint32_t>(AudioPlayer_GetRepeatMode()), false);
#endif

			// If we're in audiobook-mode and apply a modification-card, we don't
			// want to save lastPlayPosition for the mod-card but for the card that holds the playlist
			if (strlen(gCurrentRfidTagId) > 0) {
				strncpy(gPlayProperties.playRfidTag, gCurrentRfidTagId, sizeof(gPlayProperties.playRfidTag) - 1);
				gPlayProperties.playRfidTag[sizeof(gPlayProperties.playRfidTag) - 1] = '\0';
			}
		}
		// An announcement that ran to its end raises the same evt_eof as a finished track. It has to be
		// caught before the regular handling below, which would write the announcement's position to
		// NVS, evaluate the sleep flags and, above all, advance the track number.
		if (gPlayProperties.trackFinished && gPlayProperties.announcementActive) {
			gPlayProperties.trackFinished = false;
			gPlayProperties.announcementActive = false;
			// Execution continues into the regular track-open path at the end of this block:
			// currentTrackNumber was never touched, so it re-opens the very same track, and
			// startAtFilePos seeks back into it through the normal resume machinery (including the
			// deferred seek for headerless CBR files).
			gPlayProperties.startAtFilePos = AudioPlayer_announcementResumePos;
			Log_Println(announcementFinished, LOGLEVEL_INFO);
		}

		if (gPlayProperties.trackFinished) {
			gPlayProperties.trackFinished = false;
			if (gPlayProperties.playMode == NO_PLAYLIST || gPlayProperties.playlist == nullptr) {
				gPlayProperties.playlistFinished = true;
				return;
			}
			if (gPlayProperties.saveLastPlayPosition) { // Don't save for AUDIOBOOK_LOOP because not necessary
				if (gPlayProperties.currentTrackNumber + 1 < gPlayProperties.playlist->size()) {
					// Only save if there's another track, otherwise it will be saved at end of playlist anyway
					AudioPlayer_NvsRfidWriteWrapper(gPlayProperties.playRfidTag, 0, gPlayProperties.playMode, gPlayProperties.currentTrackNumber + 1);
				}
			}
			if (gPlayProperties.sleepAfterCurrentTrack) { // Go to sleep if "sleep after track" was requested
				gPlayProperties.playlistFinished = true;
				gPlayProperties.playMode = NO_PLAYLIST;
				System_RequestSleep();
				return; // TODO-> check if this is necessary or if we need a flag here
			}
			if (!gPlayProperties.repeatCurrentTrack) { // If endless-loop requested, track-number will not be incremented
				gPlayProperties.currentTrackNumber++;
			} else {
				Log_Println(repeatTrackDueToPlaymode, LOGLEVEL_INFO);
				Led_Indicate(LedIndicatorType::Rewind);
			}
		}

		if (gPlayProperties.playlistFinished && trackCommand != NO_ACTION) {
			if (gPlayProperties.playMode != BUSY) { // Prevents from staying in mode BUSY forever when error occured (e.g. directory empty that should be played)
				Log_Println(noPlaymodeChangeIfIdle, LOGLEVEL_NOTICE);
				trackCommand = NO_ACTION;
				System_IndicateError();
				return;
			}
		}
		/* Check if track-control was called
		   (stop, start, next track, prev. track, last track, first track...) */
		switch (trackCommand) {
			case STOP:
				audio->stopSong();
				trackCommand = NO_ACTION;
				Log_Println(cmndStop, LOGLEVEL_INFO);
				gPlayProperties.pausePlay = true;
				gPlayProperties.playlistFinished = true;
				gPlayProperties.playMode = NO_PLAYLIST;
				Audio_setTitle(noPlaylist);
				AudioPlayer_ClearCover();
#ifdef MQTT_ENABLE
				publishMqtt(topicPausePlay, "idle", false);
#endif
				return;

			case PAUSEPLAY:
				trackCommand = NO_ACTION;
				audio->pauseResume();
				if (gPlayProperties.pausePlay) {
					Log_Println(cmndResumeFromPause, LOGLEVEL_INFO);
#ifdef MQTT_ENABLE
					publishMqtt(topicPausePlay, "play", false);
#endif
				} else {
					Log_Println(cmndPause, LOGLEVEL_INFO);
#ifdef MQTT_ENABLE
					publishMqtt(topicPausePlay, "pause", false);
#endif
				}
				if (gPlayProperties.saveLastPlayPosition && !gPlayProperties.pausePlay) {
					Log_Printf(LOGLEVEL_INFO, trackPausedAtPos, audio->getAudioCurrentTime(), audio->getAudioFileDuration());
					AudioPlayer_NvsRfidWriteWrapper(gPlayProperties.playRfidTag, audio->getAudioCurrentTime(), gPlayProperties.playMode, gPlayProperties.currentTrackNumber);
				}
				gPlayProperties.pausePlay = !gPlayProperties.pausePlay;

				Web_SendWebsocketData(0, WebsocketCodeType::TrackInfo);
				return;

			case NEXTTRACK:
				trackCommand = NO_ACTION;
				if (gPlayProperties.pausePlay) {
					audio->pauseResume();
					gPlayProperties.pausePlay = false;
#ifdef MQTT_ENABLE
					publishMqtt(topicPausePlay, "play", false);
#endif
				}
				if (gPlayProperties.repeatCurrentTrack) { // End loop if button was pressed
					gPlayProperties.repeatCurrentTrack = false;
#ifdef MQTT_ENABLE
					publishMqtt(topicRepeatMode, static_cast<uint32_t>(AudioPlayer_GetRepeatMode()), false);
#endif
				}
				// Allow next track if current track played in playlist isn't the last track.
				// Exception: loop-playlist is active. In this case playback restarts at the first track of the playlist.
				if ((gPlayProperties.currentTrackNumber + 1 < gPlayProperties.playlist->size()) || gPlayProperties.repeatPlaylist) {
					if ((gPlayProperties.currentTrackNumber + 1 >= gPlayProperties.playlist->size()) && gPlayProperties.repeatPlaylist) {
						gPlayProperties.currentTrackNumber = 0;
					} else {
						gPlayProperties.currentTrackNumber++;
					}
					if (gPlayProperties.saveLastPlayPosition) {
						AudioPlayer_NvsRfidWriteWrapper(gPlayProperties.playRfidTag, 0, gPlayProperties.playMode, gPlayProperties.currentTrackNumber);
						Log_Println(trackStartAudiobook, LOGLEVEL_INFO);
					}
					Log_Println(cmndNextTrack, LOGLEVEL_INFO);
					if (!gPlayProperties.playlistFinished) {
						audio->stopSong();
					}
				} else {
					Log_Println(lastTrackAlreadyActive, LOGLEVEL_NOTICE);
					System_IndicateError();
					return;
				}
				break;

			case PREVIOUSTRACK:
				trackCommand = NO_ACTION;
				if (gPlayProperties.pausePlay) {
					audio->pauseResume();
					gPlayProperties.pausePlay = false;
#ifdef MQTT_ENABLE
					publishMqtt(topicPausePlay, "play", false);
#endif
				}
				if (gPlayProperties.repeatCurrentTrack) { // End loop if button was pressed
					gPlayProperties.repeatCurrentTrack = false;
#ifdef MQTT_ENABLE
					publishMqtt(topicRepeatMode, static_cast<uint32_t>(AudioPlayer_GetRepeatMode()), false);
#endif
				}
				if (gPlayProperties.playMode == WEBSTREAM) {
					Log_Println(trackChangeWebstream, LOGLEVEL_INFO);
					System_IndicateError();
					return;
				} else if (gPlayProperties.playMode == LOCAL_M3U) {
					Log_Println(cmndPrevTrack, LOGLEVEL_INFO);
					if (gPlayProperties.currentTrackNumber > 0) {
						gPlayProperties.currentTrackNumber--;
					} else {
						System_IndicateError();
						return;
					}
				} else {
					if (gPlayProperties.currentTrackNumber > 0 || gPlayProperties.repeatPlaylist) {
						if (audio->getAudioCurrentTime() < 5) { // play previous track when current track time is small, else play current track again
							if (gPlayProperties.currentTrackNumber == 0 && gPlayProperties.repeatPlaylist) {
								gPlayProperties.currentTrackNumber = gPlayProperties.playlist->size() - 1; // Go back to last track in loop-mode when first track is played
							} else {
								gPlayProperties.currentTrackNumber--;
							}
						}

						if (gPlayProperties.saveLastPlayPosition) {
							AudioPlayer_NvsRfidWriteWrapper(gPlayProperties.playRfidTag, 0, gPlayProperties.playMode, gPlayProperties.currentTrackNumber);
							Log_Println(trackStartAudiobook, LOGLEVEL_INFO);
						}

						Log_Println(cmndPrevTrack, LOGLEVEL_INFO);
						if (!gPlayProperties.playlistFinished) {
							audio->stopSong();
						}
					} else {
						if (gPlayProperties.saveLastPlayPosition) {
							AudioPlayer_NvsRfidWriteWrapper(gPlayProperties.playRfidTag, 0, gPlayProperties.playMode, gPlayProperties.currentTrackNumber);
						}
						audio->stopSong();
						Led_Indicate(LedIndicatorType::Rewind);
						String pathToTrack = gFSystem.rawPath(gPlayProperties.playlist->at(gPlayProperties.currentTrackNumber));
						audioReturnCode = audio->connecttoFS(gFSystem, pathToTrack.c_str());
						// consider track as finished, when audio lib call was not successful
						if (!audioReturnCode) {
							System_IndicateError();
							gPlayProperties.trackFinished = true;
							return;
						}
						Log_Println(trackStart, LOGLEVEL_INFO);
						return;
					}
				}
				break;
			case FIRSTTRACK:
				trackCommand = NO_ACTION;
				if (gPlayProperties.pausePlay) {
					audio->pauseResume();
					gPlayProperties.pausePlay = false;
#ifdef MQTT_ENABLE
					publishMqtt(topicPausePlay, "play", false);
#endif
				}
				gPlayProperties.currentTrackNumber = 0;
				if (gPlayProperties.saveLastPlayPosition) {
					AudioPlayer_NvsRfidWriteWrapper(gPlayProperties.playRfidTag, 0, gPlayProperties.playMode, gPlayProperties.currentTrackNumber);
					Log_Println(trackStartAudiobook, LOGLEVEL_INFO);
				}
				Log_Println(cmndFirstTrack, LOGLEVEL_INFO);
				if (!gPlayProperties.playlistFinished) {
					audio->stopSong();
				}
				break;

			case LASTTRACK:
				trackCommand = NO_ACTION;
				if (gPlayProperties.pausePlay) {
					audio->pauseResume();
					gPlayProperties.pausePlay = false;
#ifdef MQTT_ENABLE
					publishMqtt(topicPausePlay, "play", false);
#endif
				}
				if (gPlayProperties.currentTrackNumber + 1 < gPlayProperties.playlist->size()) {
					gPlayProperties.currentTrackNumber = gPlayProperties.playlist->size() - 1;
					if (gPlayProperties.saveLastPlayPosition) {
						AudioPlayer_NvsRfidWriteWrapper(gPlayProperties.playRfidTag, 0, gPlayProperties.playMode, gPlayProperties.currentTrackNumber);
						Log_Println(trackStartAudiobook, LOGLEVEL_INFO);
					}
					Log_Println(cmndLastTrack, LOGLEVEL_INFO);
					if (!gPlayProperties.playlistFinished) {
						audio->stopSong();
					}
				} else {
					Log_Println(lastTrackAlreadyActive, LOGLEVEL_NOTICE);
					System_IndicateError();
					return;
				}
				break;

			case NEXTFOLDER: // Used for recursive playmodes
				trackCommand = NO_ACTION;
				if (gPlayProperties.pausePlay) {
					audio->pauseResume();
					gPlayProperties.pausePlay = false;
				}
				gPlayProperties.jumpToFolderTrack = SdCard_findNextOrPrevDirectoryTrack(*gPlayProperties.playlist, gPlayProperties.currentTrackNumber, SearchDirection::Forward);
				if (gPlayProperties.jumpToFolderTrack != -1) {
					gPlayProperties.currentTrackNumber = gPlayProperties.jumpToFolderTrack;
					gPlayProperties.jumpToFolderTrack = -1;
					if (gPlayProperties.saveLastPlayPosition) {
						AudioPlayer_NvsRfidWriteWrapper(gPlayProperties.playRfidTag, 0, gPlayProperties.playMode, gPlayProperties.currentTrackNumber);
					}
				} else {
					Log_Println(lastFolderAlreadyActive, LOGLEVEL_NOTICE);
					System_IndicateError();
					return;
				}
				break;

			case PREVIOUSFOLDER: // Used for recursive playmodes
				trackCommand = NO_ACTION;
				if (gPlayProperties.pausePlay) {
					audio->pauseResume();
					gPlayProperties.pausePlay = false;
				}

				gPlayProperties.jumpToFolderTrack = SdCard_findNextOrPrevDirectoryTrack(*gPlayProperties.playlist, gPlayProperties.currentTrackNumber, SearchDirection::Backward);
				if (gPlayProperties.jumpToFolderTrack != -1) {
					gPlayProperties.currentTrackNumber = gPlayProperties.jumpToFolderTrack;
					gPlayProperties.jumpToFolderTrack = -1;
					if (gPlayProperties.saveLastPlayPosition) {
						AudioPlayer_NvsRfidWriteWrapper(gPlayProperties.playRfidTag, 0, gPlayProperties.playMode, gPlayProperties.currentTrackNumber);
					}
				} else {
					System_IndicateError();
					return;
				}
				break;

			case 0:
				break;

			default:
				trackCommand = NO_ACTION;
				Log_Println(cmndDoesNotExist, LOGLEVEL_NOTICE);
				System_IndicateError();
				return;
		}

		if (gPlayProperties.playUntilTrackNumber == gPlayProperties.currentTrackNumber && gPlayProperties.playUntilTrackNumber > 0) {
			if (gPlayProperties.saveLastPlayPosition) {
				AudioPlayer_NvsRfidWriteWrapper(gPlayProperties.playRfidTag, 0, gPlayProperties.playMode, 0);
			}
			gPlayProperties.playlistFinished = true;
			gPlayProperties.playMode = NO_PLAYLIST;
			System_RequestSleep();
			return;
		}

		if (gPlayProperties.currentTrackNumber >= gPlayProperties.playlist->size()) { // Check if last element of playlist is already reached
			Log_Println(endOfPlaylistReached, LOGLEVEL_NOTICE);
			if (!gPlayProperties.repeatPlaylist) {
				if (gPlayProperties.saveLastPlayPosition) {
					// Set back to first track
					AudioPlayer_NvsRfidWriteWrapper(gPlayProperties.playRfidTag, 0, gPlayProperties.playMode, 0);
				}
				gPlayProperties.playlistFinished = true;
				gPlayProperties.playMode = NO_PLAYLIST;
				Audio_setTitle(noPlaylist);
				AudioPlayer_ClearCover();
#ifdef MQTT_ENABLE
				publishMqtt(topicPlaymode, static_cast<uint32_t>(gPlayProperties.playMode), false);
#endif
				gPlayProperties.currentTrackNumber = 0;
				if (gPlayProperties.sleepAfterPlaylist) {
					System_RequestSleep();
				}
				return;
			} else { // Check if sleep after current track/playlist was requested
				if (gPlayProperties.sleepAfterPlaylist || gPlayProperties.sleepAfterCurrentTrack) {
					gPlayProperties.playlistFinished = true;
					gPlayProperties.playMode = NO_PLAYLIST;
					System_RequestSleep();
					return;
				} // Repeat playlist; set current track number back to 0
				Log_Println(repeatPlaylistDueToPlaymode, LOGLEVEL_NOTICE);
				gPlayProperties.currentTrackNumber = 0;
				if (gPlayProperties.saveLastPlayPosition) {
					AudioPlayer_NvsRfidWriteWrapper(gPlayProperties.playRfidTag, 0, gPlayProperties.playMode, gPlayProperties.currentTrackNumber);
				}
			}
		}

		if (!strncmp("http", gPlayProperties.playlist->at(gPlayProperties.currentTrackNumber), 4)) {
			gPlayProperties.isWebstream = true;
		} else {
			gPlayProperties.isWebstream = false;
		}
		gPlayProperties.currentRelPos = 0;
		audioReturnCode = false;

		if (gPlayProperties.playMode == WEBSTREAM || (gPlayProperties.playMode == LOCAL_M3U && gPlayProperties.isWebstream)) { // Webstream
			audioReturnCode = audio->connecttohost(gPlayProperties.playlist->at(gPlayProperties.currentTrackNumber));
			gPlayProperties.playlistFinished = false;
		} else if (gPlayProperties.playMode != WEBSTREAM && !gPlayProperties.isWebstream) {
			// Files from SD
			if (!gFSystem.exists(gPlayProperties.playlist->at(gPlayProperties.currentTrackNumber))) { // Check first if file/folder exists
				Log_Printf(LOGLEVEL_ERROR, dirOrFileDoesNotExist, gPlayProperties.playlist->at(gPlayProperties.currentTrackNumber));
				gPlayProperties.trackFinished = true;
				return;
			} else {
				int32_t fileStartTime = -1;
				AudioPlayer_resumeSeekPendingSecs = 0; // default: no deferred seek for this track
				if (gPlayProperties.startAtFilePos > 0) {
					fileStartTime = gPlayProperties.startAtFilePos;
					// Also arm a deferred seek: ESP32-audioI2S only honors this connecttoFS() start
					// position for files whose Xing/VBR header sets m_nominal_bitrate. Headerless CBR
					// audiobooks never get seeked here and restart from 0, so we re-seek ourselves once
					// the measured bitrate is known (see AudioPlayer_Loop). Harmless for VBR (skipped).
					AudioPlayer_resumeSeekPendingSecs = gPlayProperties.startAtFilePos;
					Log_Printf(LOGLEVEL_NOTICE, trackStartatPos, gPlayProperties.startAtFilePos);
					gPlayProperties.startAtFilePos = 0;
				}
				String pathToTrack = gFSystem.rawPath(gPlayProperties.playlist->at(gPlayProperties.currentTrackNumber));
				audioReturnCode
					= audio->connecttoFS(gFSystem, pathToTrack.c_str(), fileStartTime);
				// consider track as finished, when audio lib call was not successful
			}
		}

		if (!audioReturnCode) {
			System_IndicateError();
			// If a webstream (e.g. from an m3u-playlist) failed because WiFi is not (yet) connected,
			// remember the tag and retry it once WiFi is up.
			if (gPlayProperties.isWebstream && !Wlan_IsConnected()) {
				AudioPlayer_RememberRfidForWifiRetry(gPlayProperties.playRfidTag);
			}
			gPlayProperties.trackFinished = true;
			return;
		} else {
			// Restart the periodic-checkpoint clock for the freshly-started track, so the first
			// checkpoint lands one full interval into playback (not immediately) rather than
			// firing at once; the 0 baseline just means the first checkpoint always writes.
			AudioPlayer_lastCheckpointTimestamp = millis();
			AudioPlayer_lastCheckpointPos = 0;
			AudioPlayer_SeekPreviewCancel(); // a preview from the previous track must never commit onto this one
			if (gPlayProperties.currentTrackNumber) {
				Led_Indicate(LedIndicatorType::PlaylistProgress);
			}
			const char *title = gPlayProperties.playlist->at(gPlayProperties.currentTrackNumber);
			if (gPlayProperties.isWebstream) {
				title = "Webradio";
			}
			if (gPlayProperties.playlist->size() > 1) {
				Audio_setTitle("(%u/%u): %s", gPlayProperties.currentTrackNumber + 1, gPlayProperties.playlist->size(), title);
			} else {
				Audio_setTitle("%s", title);
			}
			AudioPlayer_ClearCover();
			Log_Printf(LOGLEVEL_NOTICE, currentlyPlaying, gPlayProperties.playlist->at(gPlayProperties.currentTrackNumber), (gPlayProperties.currentTrackNumber + 1), gPlayProperties.playlist->size());
			gPlayProperties.playlistFinished = false;
		}
	}

	// Relative seek. Accumulated in an atomic so that firing CMD_SEEK_* once per rotary detent scrubs
	// proportionally instead of collapsing into a single jump (seekmode was a single overwrite-able enum
	// consumed once per iteration, so rapid repeats were lost).
	const int16_t seekOffset = AudioPlayer_PendingSeekSeconds.exchange(0, std::memory_order_relaxed);
	if (seekOffset != 0) {
		if (audio->setTimeOffset(seekOffset)) {
			Log_Printf(LOGLEVEL_NOTICE, (seekOffset > 0) ? secondsJumpForward : secondsJumpBackward, abs(seekOffset));
		}
	}

	// Seek-preview (CMD_SEEK_PREVIEW rotary gesture): commit once the encoder has been idle for the
	// configured delay. A release-triggered commit happens directly from RotaryEncoder.cpp instead of
	// waiting for this -- this is only the "held but stopped turning" case.
	if (AudioPlayer_SeekPreviewActive.load(std::memory_order_relaxed)) {
		if (millis() - AudioPlayer_SeekPreviewLastInputMs >= AudioPlayer_SeekPreviewDelayMsCached) {
			AudioPlayer_SeekPreviewCommit();
		}
	}

	// Handle seekmodes
	if (gPlayProperties.seekmode != SEEK_NORMAL) {
		if ((gPlayProperties.seekmode == SEEK_POS_PERCENT) && (gPlayProperties.currentRelPos >= 0) && (gPlayProperties.currentRelPos < 100)) {
			uint32_t newFileTime = uint32_t((gPlayProperties.currentRelPos / 100.0f) * audio->getAudioFileDuration());
			if (audio->setAudioPlayTime(newFileTime)) {
				Log_Printf(LOGLEVEL_NOTICE, JumpToPosition, newFileTime, audio->getAudioFileDuration());
			} else {
				System_IndicateError();
			}
		}
		gPlayProperties.seekmode = SEEK_NORMAL;
	}

	// Handle IP-announcement
	if (gPlayProperties.tellMode == TTS_IP_ADDRESS) {
		gPlayProperties.tellMode = TTS_NONE;
		String ipText = Wlan_GetIpAddress();
		bool speechOk;
		// make IP as text (replace thousand separator with locale text)
		switch (LANGUAGE) {
			case DE:
				ipText.replace(".", "Punkt");
				speechOk = audio->connecttospeech(ipText.c_str(), "de");
				break;
			case FR:
				ipText.replace(".", "point");
				speechOk = audio->connecttospeech(ipText.c_str(), "fr");
				break;
			default:
				ipText.replace(".", "point");
				speechOk = audio->connecttospeech(ipText.c_str(), "en");
		}
		if (!speechOk) {
			System_IndicateError();
		}
	}

	// Handle time-announcement
	if (gPlayProperties.tellMode == TTS_CURRENT_TIME) {
		gPlayProperties.tellMode = TTS_NONE;
		struct tm timeinfo;
		getLocalTime(&timeinfo);
		static char timeStringBuff[64];
		bool speechOk;
#if (LANGUAGE == DE)
		snprintf(timeStringBuff, sizeof(timeStringBuff), "Es ist %02d:%02d Uhr", timeinfo.tm_hour, timeinfo.tm_min);
		speechOk = audio->connecttospeech(timeStringBuff, "de");
#else
		if (timeinfo.tm_hour > 12) {
			snprintf(timeStringBuff, sizeof(timeStringBuff), "It is %02d:%02d PM", timeinfo.tm_hour - 12, timeinfo.tm_min);
		} else {
			snprintf(timeStringBuff, sizeof(timeStringBuff), "It is %02d:%02d AM", timeinfo.tm_hour, timeinfo.tm_min);
		}
		speechOk = audio->connecttospeech(timeStringBuff, "en");
#endif
		if (!speechOk) {
			System_IndicateError();
		}
	}

	// If speech is over, go back to predefined state
	if (!gPlayProperties.currentSpeechActive && gPlayProperties.lastSpeechActive) {
		gPlayProperties.lastSpeechActive = false;
		if (gPlayProperties.playMode != NO_PLAYLIST) {
			xQueueSend(gRfidCardQueue, gPlayProperties.playRfidTag, 0); // Re-inject previous RFID-ID in order to continue playback
		}
	}

	// Handle if mono/stereo should be changed (e.g. if plugging headphones)
	if (gPlayProperties.newPlayMono != gPlayProperties.currentPlayMono) {
		gPlayProperties.currentPlayMono = gPlayProperties.newPlayMono;
		audio->forceMono(gPlayProperties.currentPlayMono);
		if (gPlayProperties.currentPlayMono) {
			Log_Println(newPlayModeMono, LOGLEVEL_NOTICE);
		} else {
			Log_Println(newPlayModeStereo, LOGLEVEL_NOTICE);
		}
		AudioPlayer_ApplyTone(gPlayProperties.gainLowPass, gPlayProperties.gainBandPass, gPlayProperties.gainHighPass);
	}

	audio->loop(); // Call audio-loop function to process incoming data

	if (gPlayProperties.playlistFinished || gPlayProperties.pausePlay) {
	} else {
		System_UpdateActivityTimer(); // Refresh if playlist is active so uC will not fall asleep due to reaching inactivity-time
	}

	if (audio->isRunning()) {
		playbackTimeoutStart = millis();
	}

	// If error occured: move to the next track in the playlist
	const bool activeMode = (gPlayProperties.playMode != NO_PLAYLIST && gPlayProperties.playMode != BUSY);
	const bool noAudio = (!audio->isRunning() && !gPlayProperties.pausePlay);
	const bool timeout = ((millis() - playbackTimeoutStart) > playbackTimeout);
	if (activeMode) {
		// we check for timeout
		if (noAudio && timeout) {
			// Audio playback timed out, move on to the next
			System_IndicateError();
			gPlayProperties.trackFinished = true;
			playbackTimeoutStart = millis();
		}
	} else {
		// we are idle, update timeout so that we do not get a spurious error when launching into a playlist
		playbackTimeoutStart = millis();
	}

	if (gPlayProperties.dontAcceptRfidTwice) {
		// Release the lock once playback is idle again, so the same tag can be applied anew. The lock is
		// armed when a tag is accepted (see Rfid_PreferenceLookupHandler()), independent of whether playback
		// actually started - otherwise a tag whose first track fails immediately (e.g. a webstream without
		// WiFi) would stay locked forever and could never be retried.
		if (gPlayProperties.playlistFinished || gPlayProperties.playMode == NO_PLAYLIST) {
			if (gResetOldRfidOnIdle) {
				Rfid_ResetOldRfid();
				gResetOldRfidOnIdle = false;
			}
		}
	}
}

// Returns current repeat-mode (mix of repeat current track and current playlist)
uint8_t AudioPlayer_GetRepeatMode(void) {
	if (gPlayProperties.repeatPlaylist && gPlayProperties.repeatCurrentTrack) {
		return TRACK_N_PLAYLIST;
	} else if (gPlayProperties.repeatPlaylist && !gPlayProperties.repeatCurrentTrack) {
		return PLAYLIST;
	} else if (!gPlayProperties.repeatPlaylist && gPlayProperties.repeatCurrentTrack) {
		return TRACK;
	} else {
		return NO_REPEAT;
	}
}

// Adds new volume-entry to volume-queue
// If volume is changed via webgui or MQTT, it's necessary to re-adjust current value of rotary-encoder.
void AudioPlayer_SetVolume(const int32_t _newVolume) {
	uint32_t _volume;
	int32_t _volumeBuf = AudioPlayer_GetCurrentVolume();

	Led_Indicate(LedIndicatorType::VolumeChange);
	// Clamp rather than reject: a fast rotary spin can ask for several steps at once, and rejecting the whole
	// change meant that near the rails (e.g. 20 -> 23 with max 21) nothing happened at all instead of pinning.
	int32_t clampedVolume = _newVolume;
	if (clampedVolume < AudioPlayer_GetMinVolume()) {
		clampedVolume = AudioPlayer_GetMinVolume();
		Log_Println(minLoudnessReached, LOGLEVEL_INFO);
	} else if (clampedVolume > AudioPlayer_GetMaxVolume()) {
		clampedVolume = AudioPlayer_GetMaxVolume();
		Log_Println(maxLoudnessReached, LOGLEVEL_INFO);
	}
	{
		_volume = clampedVolume;
		AudioPlayer_SetCurrentVolume(_volume);

		Log_Printf(LOGLEVEL_INFO, newLoudnessReceived, _volume);
		audio->setVolume(_volume);
		if (System_GetOperationMode() == OPMODE_BLUETOOTH_SOURCE) {
			Bluetooth_SetVolume(_volume);
		}
		Web_SendWebsocketData(0, WebsocketCodeType::Volume);
#ifdef MQTT_ENABLE
		publishMqtt(topicLoudness, static_cast<uint32_t>(_volume), false);
#endif
		AudioPlayer_PauseOnMinVolume(_volumeBuf, clampedVolume);
	}
}

// Adds equalizer settings low, band and high pass and readjusts the equalizer
void AudioPlayer_SetEqualizer(const int8_t gainLowPass, const int8_t gainBandPass, const int8_t gainHighPass) {
	AudioPlayer_ApplyTone(gainLowPass, gainBandPass, gainHighPass);
}

// Pauses playback if playback is active and volume is changes from minVolume+1 to minVolume (usually 0)
void AudioPlayer_PauseOnMinVolume(const uint8_t oldVolume, const uint8_t newVolume) {
	if (gPlayProperties.pauseOnMinVolume) {
		if (gPlayProperties.playMode == BUSY || gPlayProperties.playMode == NO_PLAYLIST) {
			return;
		}

		if (!gPlayProperties.pausePlay) { // Volume changes from 1 to 0
			if (oldVolume == AudioPlayer_GetMinVolume() + 1 && newVolume == AudioPlayer_GetMinVolume()) {
				Cmd_Action(CMD_PLAYPAUSE);
			}
		}
		if (gPlayProperties.pausePlay) { // Volume changes from 0 to 1
			if (oldVolume == AudioPlayer_GetMinVolume() && newVolume > AudioPlayer_GetMinVolume()) {
				Cmd_Action(CMD_PLAYPAUSE);
			}
		}
	}
}

// Receives de-serialized RFID-data (from NVS) and dispatches playlists for the given
// playmode to the track-queue.
void AudioPlayer_SetPlaylist(const char *_itemToPlay, const uint32_t _lastPlayPos, const uint32_t _playMode, const uint16_t _trackLastPlayed) {
	// Make sure last playposition for audiobook is saved when new RFID-tag is applied
	if (gPlayProperties.SavePlayPosRfidChange && !gPlayProperties.pausePlay && (gPlayProperties.playMode == AUDIOBOOK || gPlayProperties.playMode == AUDIOBOOK_LOOP || gPlayProperties.playMode == AUDIOBOOK_RECURSIVE)) {
		AudioPlayer_SetTrackControl(PAUSEPLAY);
		while (!gPlayProperties.pausePlay) { // Make sure to wait until playback is paused in order to be sure that playposition saved in NVS
			AudioPlayer_Loop();
			vTaskDelay(portTICK_PERIOD_MS * 100u);
		}
	}

	gPlayProperties.startAtFilePos = _lastPlayPos;
	gPlayProperties.currentTrackNumber = _trackLastPlayed;
	std::optional<Playlist *> musicFiles;
	String folderPath = _itemToPlay;

	if (_playMode != WEBSTREAM) {
		if (_playMode == RANDOM_SUBDIRECTORY_OF_DIRECTORY || _playMode == RANDOM_SUBDIRECTORY_OF_DIRECTORY_ALL_TRACKS_OF_DIR_RANDOM) {
			folderPath = SdCard_pickRandomSubdirectory(_itemToPlay);
			if (!folderPath) {
				// If error occured while extracting random subdirectory
				musicFiles = std::nullopt;
			} else {
				musicFiles = SdCard_ReturnPlaylist(folderPath.c_str(), _playMode, 0, false); // Provide random subdirectory in order to enter regular playlist-generation
			}
		} else {
			// Need to define recursion depth for recursive playmodes. Other playmodes get static recursion depth of 0
			if (_playMode == ALL_TRACKS_OF_DIR_SORTED_RECURSIVE || _playMode == AUDIOBOOK_RECURSIVE || _playMode == ALL_TRACKS_OF_DIR_RANDOM_RECURSIVE) {
				musicFiles = SdCard_ReturnPlaylist(_itemToPlay, _playMode, SdCard_GetMaxRecursionDepth(), false);
			} else {
				musicFiles = SdCard_ReturnPlaylist(_itemToPlay, _playMode, 0, false);
			}
		}
	} else {
		musicFiles = AudioPlayer_ReturnPlaylistFromWebstream(_itemToPlay);
	}

	// Catch if error occured (e.g. file not found)
	if (!musicFiles) {
		Log_Println(errorOccured, LOGLEVEL_ERROR);
		System_IndicateError();
		if (gPlayProperties.playMode != NO_PLAYLIST) {
			AudioPlayer_SetTrackControl(STOP);
		}
		return;
	}

	gPlayProperties.playMode = BUSY; // Show @Neopixel, if uC is busy with creating playlist
	Playlist *list = musicFiles.value();
	if (!list->size()) {
		Log_Println(noMp3FilesInDir, LOGLEVEL_NOTICE);
		System_IndicateError();
		if (!gPlayProperties.pausePlay) {
			AudioPlayer_SetTrackControl(STOP);
			while (!gPlayProperties.pausePlay) {
				AudioPlayer_Loop();
				vTaskDelay(portTICK_PERIOD_MS * 10u);
			}
		}

		gPlayProperties.playMode = NO_PLAYLIST;
		freePlaylist(list);
		return;
	}

	// Set some default-values
	gPlayProperties.repeatCurrentTrack = false;
	gPlayProperties.repeatPlaylist = false;
	gPlayProperties.sleepAfterCurrentTrack = false;
	gPlayProperties.sleepAfterPlaylist = false;
	gPlayProperties.saveLastPlayPosition = false;
	gPlayProperties.playUntilTrackNumber = 0;

	// Store last RFID-tag to NVS
	gPrefsSettings.putString("lastRfid", gCurrentRfidTagId);

	bool error = false;
	switch (_playMode) {
		case SINGLE_TRACK: {
			Log_Println(modeSingleTrack, LOGLEVEL_NOTICE);

			break;
		}

		case SINGLE_TRACK_LOOP: {
			gPlayProperties.repeatCurrentTrack = true;
			gPlayProperties.repeatPlaylist = true;
			Log_Println(modeSingleTrackLoop, LOGLEVEL_NOTICE);
			break;
		}

		case SINGLE_TRACK_OF_DIR_RANDOM: {
			gPlayProperties.sleepAfterCurrentTrack = true;
			gPlayProperties.playUntilTrackNumber = 0;
			System_SetNightmode(true);
			Log_Println(modeSingleTrackRandom, LOGLEVEL_NOTICE);
			AudioPlayer_RandomizePlaylist(list);
			// we have a random order, so pick the first entry and scrap the rest
			auto first = list->at(0);
			list->at(0) = nullptr; // prevent our entry from being destroyed
			freePlaylist(list); // this also scrapped our vector --> recreate it
			list = allocatePlaylist();
			list->push_back(first);
			break;
		}

		case AUDIOBOOK: { // Tracks need to be sorted!
			gPlayProperties.saveLastPlayPosition = true;
			Log_Println(modeSingleAudiobook, LOGLEVEL_NOTICE);
			AudioPlayer_SortPlaylist(list);
			break;
		}

		case AUDIOBOOK_LOOP: { // Tracks need to be sorted!
			gPlayProperties.repeatPlaylist = true;
			gPlayProperties.saveLastPlayPosition = true;
			Log_Println(modeSingleAudiobookLoop, LOGLEVEL_NOTICE);
			AudioPlayer_SortPlaylist(list);
			break;
		}

		case AUDIOBOOK_RECURSIVE: { // Tracks need to be sorted!
			gPlayProperties.saveLastPlayPosition = true;
			Log_Println(modeAudiobookRecursive, LOGLEVEL_NOTICE);
			AudioPlayer_SortPlaylist(list);
			break;
		}

		case ALL_TRACKS_OF_DIR_SORTED_RECURSIVE: {
			Log_Printf(LOGLEVEL_NOTICE, modeAllTrackAlphSortedRecursive, folderPath.c_str());
			AudioPlayer_SortPlaylist(list);
			break;
		}

		case ALL_TRACKS_OF_DIR_SORTED:
		case RANDOM_SUBDIRECTORY_OF_DIRECTORY: {
			Log_Printf(LOGLEVEL_NOTICE, modeAllTrackAlphSorted, folderPath.c_str());
			AudioPlayer_SortPlaylist(list);
			break;
		}

		case ALL_TRACKS_OF_DIR_RANDOM_RECURSIVE: {
			Log_Printf(LOGLEVEL_NOTICE, modeAllTrackRandomRecursive, folderPath.c_str());
			AudioPlayer_RandomizePlaylist(list);
			break;
		}

		case ALL_TRACKS_OF_DIR_RANDOM:
		case RANDOM_SUBDIRECTORY_OF_DIRECTORY_ALL_TRACKS_OF_DIR_RANDOM: {
			Log_Printf(LOGLEVEL_NOTICE, modeAllTrackRandom, folderPath.c_str());
			AudioPlayer_RandomizePlaylist(list);
			break;
		}

		case ALL_TRACKS_OF_DIR_SORTED_LOOP: {
			gPlayProperties.repeatPlaylist = true;
			Log_Println(modeAllTrackAlphSortedLoop, LOGLEVEL_NOTICE);
			AudioPlayer_SortPlaylist(list);
			break;
		}

		case ALL_TRACKS_OF_DIR_RANDOM_LOOP: {
			gPlayProperties.repeatPlaylist = true;
			Log_Println(modeAllTrackRandomLoop, LOGLEVEL_NOTICE);
			AudioPlayer_RandomizePlaylist(list);
			break;
		}

		case WEBSTREAM: { // This is always just one "track"
			Log_Println(modeWebstream, LOGLEVEL_NOTICE);
			if (!Wlan_IsConnected()) {
				Log_Println(webstreamNotAvailable, LOGLEVEL_ERROR);
				// Remember this tag and retry automatically once WiFi is connected (e.g. webradio-tag applied at boot)
				AudioPlayer_RememberRfidForWifiRetry(gCurrentRfidTagId);
				error = true;
			}
			break;
		}

		case LOCAL_M3U: { // Can be one or multiple SD-files or webradio-stations; or a mix of both
			Log_Println(modeWebstreamM3u, LOGLEVEL_NOTICE);
			break;
		}

		default:
			Log_Printf(LOGLEVEL_ERROR, modeInvalid, gPlayProperties.playMode);
			error = true;
	}

	if (!error) {
		gPlayProperties.playMode = _playMode;
		newPlayListAvailable = true;
		newPlayList = list;
		return;
	}

	// we had an error, blink and destroy playlist
	gPlayProperties.playMode = NO_PLAYLIST;
	System_IndicateError();
	freePlaylist(list);
}

/* Wraps putString for writing settings into NVS for RFID-cards.
   Returns number of characters written. */
size_t AudioPlayer_NvsRfidWriteWrapper(const char *_rfidCardId, const uint32_t _playPosition, const uint8_t _playMode, const uint16_t _trackLastPlayed) {
	if (_playMode == NO_PLAYLIST) {
		// writing back to NVS with NO_PLAYLIST seems to be a bug - Todo: Find the cause here
		Log_Printf(LOGLEVEL_ERROR, modeInvalid, _playMode);
		return 0;
	}
	Led_SetPause(true); // Workaround to prevent exceptions due to Neopixel-signalisation while NVS-write
	char firstPart[275] = {0};
	char prefBuf[275];

	gPrefsRfid.getString(_rfidCardId, firstPart, sizeof(firstPart)); // read back previous value from NVS

	// Remove everything after the first part (after the first stringDelimiter)
	char *pos = strchr(firstPart + strlen(stringDelimiter), stringDelimiter[0]);
	if (pos != NULL) {
		*pos = '\0'; // Terminate the string at this position
	}

	// MediaHub-managed cards (concept §8.1) store MEDIAHUB as a marker in this
	// field, not the real playmode; gPlayProperties.playMode is the manifest's
	// real mode by the time playback reaches this wrapper, so writing it back
	// verbatim would silently overwrite the marker on the first position-save.
	uint8_t playModeToStore = _playMode;
	if (MediaHub_IsMediaHubPath(firstPart + strlen(stringDelimiter))) {
		playModeToStore = MEDIAHUB;
	}

	// Build the new string with the preserved first part (which already contains the track)
	snprintf(prefBuf, sizeof(prefBuf), "%s%s%" PRIu32 "%s%d%s%" PRIu16, firstPart, stringDelimiter, _playPosition, stringDelimiter, playModeToStore, stringDelimiter, _trackLastPlayed);

	Log_Printf(LOGLEVEL_INFO, wroteLastTrackToNvs, prefBuf, _rfidCardId, playModeToStore, _trackLastPlayed);
	Log_Println(prefBuf, LOGLEVEL_INFO);
	Led_SetPause(false);
	return gPrefsRfid.putString(_rfidCardId, prefBuf);

	// Examples for serialized RFID-actions that are stored in NVS
	// #<file/folder>#<startPlayPositionInBytes>#<playmode>#<trackNumberToStartWith>
	// Please note: There's no need to do this manually (unless you want to)
	/*gPrefsRfid.putString("215123125075", "#/mp3/Kinderlieder#0#6#0");
	gPrefsRfid.putString("169239075184", "#http://radio.koennmer.net/evosonic.mp3#0#8#0");
	gPrefsRfid.putString("244105171042", "#0#0#111#0"); // modification-card (repeat track)
	gPrefsRfid.putString("228064156042", "#0#0#110#0"); // modification-card (repeat playlist)
	gPrefsRfid.putString("212130160042", "#/mp3/Hoerspiele/Yakari/Sammlung2#0#3#0");*/
}

// Adds webstream to playlist; same like SdCard_ReturnPlaylist() but always only one entry
std::optional<Playlist *> AudioPlayer_ReturnPlaylistFromWebstream(const char *_webUrl) {
	Playlist *playlist = allocatePlaylist();
	const size_t len = strlen(_webUrl) + 1;
	char *entry = static_cast<char *>(x_malloc(len));
	if (!entry) {
		// OOM
		Log_Println(unableToAllocateMemForLinearPlaylist, LOGLEVEL_ERROR);
		freePlaylist(playlist);
		return std::nullopt;
	}
	strncpy(entry, _webUrl, len);
	entry[len - 1] = '\0';
	playlist->push_back(entry);

	return playlist;
}

// Adds new control-command to control-queue
void AudioPlayer_SetTrackControl(const uint8_t new_trackCommand) {
	trackCommand = new_trackCommand;
}

// Knuth-Fisher-Yates-algorithm to randomize playlist
void AudioPlayer_RandomizePlaylist(Playlist *playlist) {
	if (playlist->size() < 2) {
		// we can not randomize less than 2 entries
		return;
	}

	// randomize using the "normal" random engine and shuffle
	std::default_random_engine rnd(millis());
	std::shuffle(playlist->begin(), playlist->end(), rnd);
}

// Helper to sort playlist - standard string comparison
static bool AudioPlayer_ArrSortHelper_strcmp(const char *a, const char *b) {
	return strcmp(a, b) < 0;
}

// Helper to sort playlist - natural case-sensitive
static bool AudioPlayer_ArrSortHelper_strnatcmp(const char *a, const char *b) {
	return strnatcmp(a, b) < 0;
}

// Helper to sort playlist - natural case-insensitive
static bool AudioPlayer_ArrSortHelper_strnatcasecmp(const char *a, const char *b) {
	return strnatcasecmp(a, b) < 0;
}

// Sort playlist
void AudioPlayer_SortPlaylist(Playlist *playlist) {
	std::function<bool(const char *, const char *)> cmpFunc;
	const char *mode;
	switch (AudioPlayer_PlaylistSortMode) {
		case playlistSortMode::STRCMP:
			cmpFunc = AudioPlayer_ArrSortHelper_strcmp; // standard string comparison
			mode = "standard string compare";
			break;
		case playlistSortMode::STRNATCMP:
			cmpFunc = AudioPlayer_ArrSortHelper_strnatcmp; // natural case-sensitive
			mode = "case-sensitive natural sorting";
			break;
		case playlistSortMode::STRNATCASECMP:
		default:
			cmpFunc = AudioPlayer_ArrSortHelper_strnatcasecmp; // natural case-insensitive
			mode = "case-insensitive natural sorting";
			break;
	}

	Log_Printf(LOGLEVEL_INFO, "Sorting files using %s", mode, "\n");
	std::sort(playlist->begin(), playlist->end(), cmpFunc);
	/*for (const char *str : *playlist) {
		Serial.println(str);
	}*/
}

// Clear cover send notification
void AudioPlayer_ClearCover(void) {
	gPlayProperties.coverFilePos = 0;
	AudioPlayer_StationLogoUrl = "";
	// websocket and mqtt notify cover image has changed
	Web_SendWebsocketData(0, WebsocketCodeType::CoverImg);
#ifdef MQTT_ENABLE
	publishMqtt(topicCoverChanged, "", false);
#endif
}

// id3 tag: save cover image
void audio_id3image(File &file, const size_t pos, const size_t size) {
	// save cover image position and size for later use
	gPlayProperties.coverFilePos = pos;
	gPlayProperties.coverFileSize = size;
	// websocket and mqtt notify cover image has changed
	Web_SendWebsocketData(0, WebsocketCodeType::CoverImg);
#ifdef MQTT_ENABLE
	publishMqtt(topicCoverChanged, "", false);
#endif
}

// encoded blockpicture cover image segments (all ogg, vorbis, opus files, some flac files)
void audio_oggimage(File &file, std::vector<uint32_t> v) {
	// save decoded cover in /.cache/file.path()
	String decodedCover = "/.cache";
	decodedCover.concat(file.path());
	if (gFSystem.exists(decodedCover)) {
		Log_Printf(LOGLEVEL_DEBUG, "Cover already cached in %s", decodedCover.c_str());
	} else {
		String tmpDecodedCover = decodedCover.substring(0, decodedCover.lastIndexOf('/') + 1); // to prevent coverFile corruption write into temporary file; fixed name since no parallel usage of audioI2S
		tmpDecodedCover.concat(".tmp");
		File coverFile = gFSystem.open(tmpDecodedCover, FILE_WRITE, true); // open file with create=true to make sure parent directories are created
		if (!coverFile) {
			return;
		}

		// write fLaC marker in order to use flac Routine, since decoded cover has METADATA_BLOCK_PICTURE like flac
		constexpr uint8_t flacMarker[] = "fLaC";
		coverFile.write(flacMarker, std::char_traits<uint8_t>::length(flacMarker));

		const size_t chunkSize = 2048; // must be base64 compatible, i.e. a multiple of 4
		uint8_t *encodedChunk = (uint8_t *) x_malloc(chunkSize);
		size_t decodedLength;
		size_t currentRemainder = 0;
		size_t currentPosition = file.position(); // save current position in audio file otherwise playback will result in an error

		for (size_t i = 0; i < v.size(); i += 2) {
			// calculate the number of chunks needed to read the segment
			size_t numChunks = (v[i + 1] + currentRemainder) / chunkSize;
			size_t remainder = currentRemainder;

			// read and decode the segment chunk by chunk, write decodedChunk into encodedChunk to save memory
			file.seek(v[i]);
			for (size_t chunk = 0; chunk < numChunks; chunk++) {
				file.readBytes(reinterpret_cast<char *>(&encodedChunk[remainder]), chunkSize - remainder);
				decodedLength = b64decode(encodedChunk, encodedChunk, chunkSize);
				coverFile.write(encodedChunk, decodedLength);
				remainder = 0;
			}

			// calculate new remainder, read it, and if it is the end of file, decode it
			currentRemainder = (v[i + 1] + currentRemainder) % chunkSize;
			if (currentRemainder) {
				file.readBytes(reinterpret_cast<char *>(&encodedChunk[remainder]), currentRemainder - remainder);
				if (i == v.size() - 2) {
					decodedLength = b64decode(encodedChunk, encodedChunk, currentRemainder);
					coverFile.write(encodedChunk, decodedLength);
				}
			}
		}
		free(encodedChunk);
		coverFile.close();
		file.seek(currentPosition);
		gFSystem.rename(tmpDecodedCover, decodedCover);
		Log_Printf(LOGLEVEL_DEBUG, "Cover decoded and cached in %s", decodedCover.c_str());
	}
	gPlayProperties.coverFilePos = 4; // flacMarker gives 4 Bytes before METADATA_BLOCK_PICTURE (audioI2S points to METADATA_BLOCK_PICTURE since 6241daa)
	// websocket and mqtt notify cover image has changed
	Web_SendWebsocketData(0, WebsocketCodeType::CoverImg);
#ifdef MQTT_ENABLE
	publishMqtt(topicCoverChanged, "", false);
#endif
}

// Send raw decoded samples to Bluetooth before the local output processing
// applies EQ, mono conversion, or the ESPuino volume curve.
void audio_process_raw_samples(int32_t *outBuff, int16_t validSamples) {
	if ((System_GetOperationMode() == OPMODE_BLUETOOTH_SOURCE) && Bluetooth_Device_Connected()) {
		// audioI2S provides signed 32-bit, left-aligned PCM; A2DP expects interleaved signed 16-bit PCM.
		int16_t *outBuff16 = reinterpret_cast<int16_t *>(outBuff);
		for (int16_t i = 0; i < validSamples; i++) {
			const int32_t sample = outBuff[i];
			outBuff16[i] = static_cast<int16_t>(sample >> 16);
		}

		Bluetooth_Source_SendAudioData(outBuff16, validSamples);
	}
}

// record audiodata or send via BT
void audio_process_i2s(int32_t *outBuff, int16_t validSamples, bool *continueI2S) {
	if ((System_GetOperationMode() == OPMODE_BLUETOOTH_SOURCE) && Bluetooth_Device_Connected()) {
		// Bluetooth already received the raw samples in audio_process_raw_samples().
		// Do not write the locally processed copy to the physical I2S output.
		*continueI2S = false;
		return;
	}

	*continueI2S = true;
}
