biologist79/ESPuino/src/Led.cpp

#include <Arduino.h>
#include "settings.h"

#include "Led.h"

#include "AudioPlayer.h"
#include "Battery.h"
#include "Bluetooth.h"
#include "Button.h"
#include "Log.h"
#include "Mqtt.h"
#include "Port.h"
#include "Queues.h"
#include "System.h"
#include "Wlan.h"

#include <WiFi.h>
#include <atomic>
#include <esp_task_wdt.h>

#ifdef NEOPIXEL_ENABLE
	#define LED_INDICATOR_SET(indicator)	((Led_Indicators) |= (1u << ((uint8_t) indicator)))
	#define LED_INDICATOR_IS_SET(indicator) (((Led_Indicators) & (1u << ((uint8_t) indicator))) > 0u)
	#define LED_INDICATOR_CLEAR(indicator)	((Led_Indicators) &= ~(1u << ((uint8_t) indicator)))

	// Time in milliseconds the volume indicator is visible
	#define LED_VOLUME_INDICATOR_RETURN_DELAY 1000U
	#define LED_VOLUME_INDICATOR_NUM_CYCLES	  (LED_VOLUME_INDICATOR_RETURN_DELAY / 20)

extern t_button gButtons[7]; // next + prev + pplay + rotEnc + button4 + button5 + dummy-button
extern uint8_t gShutdownButton;

static std::atomic<uint32_t> Led_Indicators = 0u;
// Brightness to restore once night mode / ambient light is switched off again. Deliberately two
// variables: both modes can be active at the same time, and with a single shared slot the one entered
// last overwrote the other's value -- leaving the brightness stuck at the inner mode's level after
// both had been switched off again.
static uint8_t Led_savedBrightnessNightmode;
static uint8_t Led_savedBrightnessAmbient;

// global led settings
static LedSettings gLedSettings;

// the strip buffer bound to FastLED via addLeds(); file-scope (rather than local to Led_Task)
// so Led_ShowOtaProgress() can draw into it directly while Led_Task is suspended during an
// OTA upload (see System_PauseTasksDuringUpload())
static CRGB *leds = nullptr;

TaskHandle_t Led_TaskHandle;
static void Led_Task(void *parameter);
static uint8_t Led_Address(uint8_t number);

// animation-functions prototypes
AnimationReturnType Animation_PlaylistProgress(const bool startNewAnimation, CRGBSet &leds);
AnimationReturnType Animation_BatteryMeasurement(const bool startNewAnimation, CRGBSet &leds);
AnimationReturnType Animation_Volume(const bool startNewAnimation, CRGBSet &leds);
AnimationReturnType Animation_Progress(const bool startNewAnimation, CRGBSet &leds);
AnimationReturnType Animation_Boot(const bool startNewAnimation, CRGBSet &leds);
AnimationReturnType Animation_Shutdown(const bool startNewAnimation, CRGBSet &leds);
AnimationReturnType Animation_Error(const bool startNewAnimation, CRGBSet &leds);
AnimationReturnType Animation_Ok(const bool startNewAnimation, CRGBSet &leds);
AnimationReturnType Animation_VoltageWarning(const bool startNewAnimation, CRGBSet &leds);
AnimationReturnType Animation_Webstream(const bool startNewAnimation, CRGBSet &leds);
AnimationReturnType Animation_Rewind(const bool startNewAnimation, CRGBSet &leds);
AnimationReturnType Animation_Idle(const bool startNewAnimation, CRGBSet &leds);
AnimationReturnType Animation_Busy(const bool startNewAnimation, CRGBSet &leds);
AnimationReturnType Animation_Pause(const bool startNewAnimation, CRGBSet &leds);
AnimationReturnType Animation_Speech(const bool startNewAnimation, CRGBSet &leds);
AnimationReturnType Animation_Download(const bool startNewAnimation, CRGBSet &leds);

// Pushed by MediaHub via Led_SetDownloadProgress(); Led_Task only ever reads
// these, it doesn't know MediaHub exists (same arrangement as the
// LED_INDICATOR flags/gPlayProperties fields other animations key off).
static bool Led_DownloadActive = false;
static uint8_t Led_DownloadPercent = 0;
#endif

#ifdef NEOPIXEL_ENABLE
bool Led_LoadSettings(LedSettings &settings) {
	// Get some stuff from NVS...
	// Get initial LED-brightness from NVS
	uint8_t nvsILedBrightness = gPrefsSettings.getUChar("iLedBrightness", 0);
	if (nvsILedBrightness) {
		settings.Led_InitialBrightness = nvsILedBrightness;
		settings.Led_Brightness = nvsILedBrightness;
		Log_Printf(LOGLEVEL_INFO, initialBrightnessfromNvs, nvsILedBrightness);
	} else {
		gPrefsSettings.putUChar("iLedBrightness", settings.Led_InitialBrightness);
		Log_Println(wroteInitialBrightnessToNvs, LOGLEVEL_ERROR);
	}

	// Get night LED-brightness from NVS
	uint8_t nvsNLedBrightness = gPrefsSettings.getUChar("nLedBrightness", 255);
	if (nvsNLedBrightness != 255) {
		settings.Led_NightBrightness = nvsNLedBrightness;
		if (System_GetNightmode()) {
			// Reloading the settings must not undo the dimming while night mode is still on -- the
			// initial brightness was already written to Led_Brightness above. Same handling as for the
			// ambient light below.
			settings.Led_Brightness = nvsNLedBrightness;
		}
		Log_Printf(LOGLEVEL_INFO, restoredInitialBrightnessForNmFromNvs, nvsNLedBrightness);
	} else {
		gPrefsSettings.putUChar("nLedBrightness", settings.Led_NightBrightness);
		Log_Println(wroteNmBrightnessToNvs, LOGLEVEL_ERROR);
	}

	// Get Atmo LED-brightness from NVS
	uint8_t nvsALedBrightness = gPrefsSettings.getUChar("aLedBrightness", 255);
	if (nvsALedBrightness != 255) {
		settings.Led_AmbientBrightness = nvsALedBrightness;
		if (settings.Led_AmbientLight) {
			settings.Led_Brightness = nvsALedBrightness;
		}
		Log_Printf(LOGLEVEL_INFO, restoredAtmoBrightnessForNmFromNvs, nvsALedBrightness); // TODO-> other message
	} else {
		gPrefsSettings.putUChar("aLedBrightness", settings.Led_AmbientBrightness);
		Log_Println(wroteAtmoBrightnessToNvs, LOGLEVEL_ERROR); // TODO-> other message
	}

	// Get the number of indicator LEDs from NVS
	settings.numIndicatorLeds = gPrefsSettings.getUChar("numIndicator", 24); // NUM_INDICATOR_LEDS

	// Get the number of control LEDs from NVS
	settings.numControlLeds = gPrefsSettings.getUChar("numControl", 0); // NUM_CONTROL_LEDS

	// Get the number of Led idle dots from NVS
	settings.numIdleDots = gPrefsSettings.getUChar("numIdleDots", 4); // NUM_LEDS_IDLE_DOTS
	if (settings.numIdleDots == 0) {
		// avoid division by zero
		settings.numIdleDots = 4;
	}

	// Get offset LED pause from NVS
	settings.offsetLedPause = gPrefsSettings.getBool("offsetPause", false); // OFFSET_PAUSE_LEDS

	// Flash all LEDs when an RFID tag was accepted? Off by default.
	settings.indicateRfidTag = gPrefsSettings.getBool("ledRfidFlash", false);

	// get dimmableStates from NVS
	settings.dimmableStates = gPrefsSettings.getUChar("dimStates", 50); // DIMMABLE_STATES
	if (settings.dimmableStates == 0) {
		// avoid division by zero (used as a divisor throughout Led.cpp's animations)
		settings.dimmableStates = 50;
	}

	// get hue start/end from NVS
	settings.progressHueStart = gPrefsSettings.getShort("hueStart", 85); // PROGRESS_HUE_START
	settings.progressHueEnd = gPrefsSettings.getShort("hueEnd", -1); // PROGRESS_HUE_END
	// get atmo light from NVS
	settings.atmoHue = gPrefsSettings.getShort("hueAtmo", 10); // ATMO_HUE
	settings.atmoSaturation = gPrefsSettings.getShort("satAtmo", 180); // ATMO_SATURATION

	// get reverse rotation from NVS
	settings.neopixelReverseRotation = gPrefsSettings.getBool("ledReverseRot", false); // NEOPIXEL_REVERSE_ROTATION

	// get LED offset from NVS
	settings.ledOffset = gPrefsSettings.getUChar("ledOffset", 0); // LED_OFFSET
	if (settings.ledOffset >= settings.numIndicatorLeds) {
		Log_Println("ledOffset must be between 0 and numIndicatorLeds-1", LOGLEVEL_ERROR);
		return false;
	}
	// load control colors from NVS
	settings.controlLedColors = {}; // CONTROL_LEDS_COLORS
	if ((settings.numControlLeds > 0) && gPrefsSettings.isKey("controlColors")) {
		size_t keySize = gPrefsSettings.getBytesLength("controlColors");
		if (keySize == (settings.numControlLeds * sizeof(uint32_t))) {
			settings.controlLedColors.resize(settings.numControlLeds);
			gPrefsSettings.getBytes("controlColors", settings.controlLedColors.data(), keySize);
		}
	}
	return true;
}
#endif

void Led_Init(void) {
#ifdef NEOPIXEL_ENABLE

	if (Led_TaskHandle) {
		// if led task is already running notify to reload settings
		uint8_t ledSettingsChanged = 1;
		xQueueSend(gLedQueue, &ledSettingsChanged, 0);
		return;
	}

	// load led settings from NVS
	Led_LoadSettings(gLedSettings);

	xTaskCreatePinnedToCore(
		Led_Task, /* Function to implement the task */
		"Led_Task", /* Name of the task */
		3072, /* Stack size in words */ // 20251015: increased to 3072 because saving of "allgemeine Einstellungen" let to restarts because of stack overflows
		NULL, /* Task input parameter */
		1, /* Priority of the task */
		&Led_TaskHandle, /* Task handle. */
		1 /* Core where the task should run */
	);
#endif
}

void Led_Exit(void) {
#ifdef NEOPIXEL_ENABLE
	Log_Println("shutdown LED..", LOGLEVEL_NOTICE);
	if (Led_TaskHandle) {
		vTaskDelete(Led_TaskHandle);
		Led_TaskHandle = NULL;
	}
	// Turn off LEDs in order to avoid LEDs still glowing when ESP32 is in deepsleep
	FastLED.clear(true);
#endif
}

void Led_Indicate(LedIndicatorType value) {
#ifdef NEOPIXEL_ENABLE
	LED_INDICATOR_SET(value);
#endif
}

// Deliberately hooked to an *accepted* tag rather than to the reader detecting one: in
// pauseIfRfidRemoved-mode a card resting on the antenna can be re-detected when a poll is lost to RF
// noise, which would otherwise flash the ring at random. Such a re-detection never reaches the card
// queue (RfidMfrc522.cpp keeps it as a silent play/pause), so hooking in here makes it invisible.
void Led_IndicateRfidTagAccepted(void) {
#ifdef NEOPIXEL_ENABLE
	if (!gLedSettings.indicateRfidTag) {
		return;
	}
	Led_Indicate(LedIndicatorType::Ok);
#endif
}

void Led_SetPause(boolean value) {
#ifdef NEOPIXEL_ENABLE
	gLedSettings.Led_Pause = value;
#endif
}

// Used to reset brightness to initial value after prevously active sleepmode was left
void Led_ResetToInitialBrightness(void) {
#ifdef NEOPIXEL_ENABLE
	if (gLedSettings.Led_Brightness == gLedSettings.Led_NightBrightness || gLedSettings.Led_Brightness == 0) { // Only reset to initial value if brightness wasn't intentionally changed (or was zero)
		gLedSettings.Led_Brightness = gLedSettings.Led_InitialBrightness;
		Log_Println(ledsDimmedToInitialValue, LOGLEVEL_INFO);
	}
#endif
#ifdef BUTTONS_LED
	Port_Write(BUTTONS_LED, HIGH, false);
#endif
}

void Led_ResetToNightBrightness(void) {
#ifdef NEOPIXEL_ENABLE
	gLedSettings.Led_Brightness = gLedSettings.Led_NightBrightness;
	Log_Println(ledsDimmedToNightmode, LOGLEVEL_INFO);
#endif
#ifdef BUTTONS_LED
	Port_Write(BUTTONS_LED, LOW, false);
#endif
}

uint8_t Led_GetBrightness(void) {
#ifdef NEOPIXEL_ENABLE
	return gLedSettings.Led_Brightness;
#else
	return 0u;
#endif
}

void Led_SetBrightness(uint8_t value) {
#ifdef NEOPIXEL_ENABLE
	gLedSettings.Led_Brightness = value;
	#ifdef BUTTONS_LED
	Port_Write(BUTTONS_LED, value <= gLedSettings.Led_NightBrightness ? LOW : HIGH, false);
	#endif

	#ifdef MQTT_ENABLE
	publishMqtt(topicLedBrightness, static_cast<uint32_t>(gLedSettings.Led_Brightness), false);
	#endif
#endif
}

// Only called by System_SetNightmode() on an actual state change, so saving the previous brightness
// unconditionally is safe -- see Led.h.
void Led_ApplyNightmode(bool enabled) {
#ifdef NEOPIXEL_ENABLE
	const char *msg = ledsBrightnessRestored;
	uint8_t newValue = Led_savedBrightnessNightmode;
	if (enabled) {
		// we are switching to night mode
		Led_savedBrightnessNightmode = gLedSettings.Led_Brightness;
		msg = ledsDimmedToNightmode;
		newValue = gLedSettings.Led_NightBrightness;
	}
	Led_SetBrightness(newValue);
	Log_Println(msg, LOGLEVEL_INFO);
#endif
}

void Led_SetAmbientLight(bool enabled) {
#ifdef NEOPIXEL_ENABLE
	if (gLedSettings.Led_AmbientLight == enabled) {
		// we don't need to do anything
		return;
	}

	if (enabled) {
		gLedSettings.Led_AmbientLight = true;
		Led_savedBrightnessAmbient = gLedSettings.Led_Brightness;
		Led_SetBrightness(gLedSettings.Led_AmbientBrightness);
		gPrefsSettings.putBool("atmoActive", true);
	} else {
		gLedSettings.Led_AmbientLight = false;
		Led_SetBrightness(Led_savedBrightnessAmbient);
		gPrefsSettings.putBool("atmoActive", false);
	}
#endif
}

bool Led_GetAmbientLight() {
#ifdef NEOPIXEL_ENABLE
	return gLedSettings.Led_AmbientLight;
#else
	return false;
#endif
}

void Led_ToggleAmbientLight() {
#ifdef NEOPIXEL_ENABLE
	Led_SetAmbientLight(!gLedSettings.Led_AmbientLight);
#endif
}

// Calculates physical address for a virtual LED address. This handles reversing the rotation direction of the ring and shifting the starting LED
#ifdef NEOPIXEL_ENABLE
uint8_t Led_Address(uint8_t number) {
	if (gLedSettings.neopixelReverseRotation) {
		if (gLedSettings.ledOffset > 0) {
			return number <= gLedSettings.ledOffset - 1 ? gLedSettings.ledOffset - 1 - number : gLedSettings.numIndicatorLeds + gLedSettings.ledOffset - 1 - number;
		} else {
			return gLedSettings.numIndicatorLeds - 1 - number;
		}
	} else {
		if (gLedSettings.ledOffset > 0) {
			return number >= gLedSettings.numIndicatorLeds - gLedSettings.ledOffset ? number + gLedSettings.ledOffset - gLedSettings.numIndicatorLeds : number + gLedSettings.ledOffset;
		} else {
			return number;
		}
	}
}
#endif

#ifdef NEOPIXEL_ENABLE
void Led_DrawControls(CRGB *leds) {
	if (gLedSettings.numControlLeds > 0) {
		for (uint8_t controlLed = 0; controlLed < gLedSettings.numControlLeds; controlLed++) {
			leds[gLedSettings.numIndicatorLeds + controlLed] = gLedSettings.controlLedColors[controlLed];
		}
	}
}
#endif

void Led_SetButtonLedsEnabled(boolean value) {
#ifdef BUTTONS_LED
	Port_Write(BUTTONS_LED, value ? HIGH : LOW, false);
#endif
}

#ifdef NEOPIXEL_ENABLE
CRGB Led_DimColor(CRGB color, uint8_t brightness) {
	const uint8_t factor = uint16_t(brightness * __UINT8_MAX__) / gLedSettings.dimmableStates;
	return color.nscale8(factor);
}
CRGB::HTMLColorCode Led_GetIdleColor() {
	CRGB::HTMLColorCode idleColor = CRGB::Black;
	if ((OPMODE_BLUETOOTH_SINK == System_GetOperationMode()) || (OPMODE_BLUETOOTH_SOURCE == System_GetOperationMode())) {
		if (Bluetooth_Device_Connected()) {
			idleColor = CRGB::Blue;
		} else {
			idleColor = CRGB::BlueViolet;
		}
	} else {
		if (Wlan_ConnectionTryInProgress()) {
			idleColor = CRGB::Orange;
		} else {
			idleColor = CRGB::Green;
			if (Wlan_IsConnected()) {
				idleColor = CRGB::White;
			}
		}
	}
	return idleColor;
}

void Led_DrawIdleDots(CRGBSet &leds, uint8_t offset, CRGB::HTMLColorCode color) {
	const uint8_t Led_IdleDotDistance = gLedSettings.numIndicatorLeds / gLedSettings.numIdleDots;
	for (uint8_t i = 0; i < gLedSettings.numIdleDots; i++) {
		leds[(Led_Address(offset) + i * Led_IdleDotDistance) % leds.size()] = color;
	}
}

bool CheckForPowerButtonAnimation() {
	if (gShutdownButton < (sizeof(gButtons) / sizeof(gButtons[0])) - 1) { // Only show animation, if CMD_SLEEPMODE was assigned to BUTTON_n_LONG + button is pressed
		if (gButtons[gShutdownButton].isPressed && (millis() - gButtons[gShutdownButton].firstPressedTimestamp >= 150) && gButtonInitComplete) {
			return true;
		}
	}
	return false;
}
#endif

#ifdef NEOPIXEL_ENABLE
static void Led_Task(void *parameter) {
	static uint8_t lastLedBrightness = gLedSettings.Led_Brightness;
	static CRGBSet *indicator = nullptr;

	uint8_t numIndicatorLeds = gLedSettings.numIndicatorLeds;
	uint8_t numControlLeds = gLedSettings.numControlLeds;
	// Allocate memory for LED arrays
	leds = new CRGB[numIndicatorLeds + numControlLeds];
	indicator = new CRGBSet(leds, numIndicatorLeds);
	// initialize FastLED
	FastLED.addLeds<CHIPSET, LED_PIN, COLOR_ORDER>(leds, numIndicatorLeds + numControlLeds).setCorrection(TypicalSMD5050);
	FastLED.setBrightness(gLedSettings.Led_Brightness);
	FastLED.setDither(DISABLE_DITHER);
	FastLED.setMaxRefreshRate(200); // limit LED refresh rate to 200Hz (less likely to cause flickering)

	LedAnimationType activeAnimation = LedAnimationType::NoNewAnimation;
	LedAnimationType nextAnimation = LedAnimationType::NoNewAnimation;
	bool animationActive = false;
	int32_t animationTimer = 0;
	uint8_t ledSettingsChanged;

	for (;;) {

		if (xQueueReceive(gLedQueue, &ledSettingsChanged, 0) == pdPASS) {
			// load led settings from NVS
			Led_LoadSettings(gLedSettings);
			// number of indicator/control leds changed
			if (((gLedSettings.numIndicatorLeds + gLedSettings.numControlLeds) != (numIndicatorLeds + numControlLeds)) || (gLedSettings.numControlLeds != numControlLeds)) {
				// FastLED's SPI/RMT WS2812 driver lazily creates its internal strip object,
				// sized for whatever pixel count was in effect on the very first show() call,
				// and never resizes it afterwards. Calling addLeds() again with a different
				// count here doesn't reset that internal state, so every following show()
				// call hits a hard FASTLED_ASSERT (mLedStrip->numPixels() != pixels.size()).
				// Request a clean restart instead of trying to hot-reallocate the strip, and
				// stop touching leds/indicator/FastLED until then (their sizes no longer
				// match gLedSettings).
				Log_Println("Number of LEDs changed, restarting to apply..", LOGLEVEL_NOTICE);
				System_Restart();
				vTaskDelay(portMAX_DELAY);
			}
		}

		// special handling
		if (gLedSettings.Led_Pause) { // Workaround to prevent exceptions while NVS-writes take place
			vTaskDelay(portTICK_PERIOD_MS * 10);
			continue;
		}

		Led_DrawControls(leds);

		uint32_t taskDelay = 20;
		bool startNewAnimation = false;

		// check indications and set led-mode
		// this mode will then be animated if the priority and the current animation state fit
		if (!LED_INDICATOR_IS_SET(LedIndicatorType::BootComplete)) {
			nextAnimation = LedAnimationType::Boot;
		} else if (CheckForPowerButtonAnimation()) {
			nextAnimation = LedAnimationType::Shutdown;
		} else if (LED_INDICATOR_IS_SET(LedIndicatorType::Error)) {
			LED_INDICATOR_CLEAR(LedIndicatorType::Error);
			nextAnimation = LedAnimationType::Error;
		} else if (LED_INDICATOR_IS_SET(LedIndicatorType::Ok)) {
			LED_INDICATOR_CLEAR(LedIndicatorType::Ok);
			nextAnimation = LedAnimationType::Ok;
		} else if (LED_INDICATOR_IS_SET(LedIndicatorType::VoltageWarning)) {
			LED_INDICATOR_CLEAR(LedIndicatorType::VoltageWarning);
			nextAnimation = LedAnimationType::VoltageWarning;
		} else if (Led_DownloadActive) {
			nextAnimation = LedAnimationType::Download;
		} else if (LED_INDICATOR_IS_SET(LedIndicatorType::Voltage)) {
			nextAnimation = LedAnimationType::BatteryMeasurement;
		} else if (LED_INDICATOR_IS_SET(LedIndicatorType::VolumeChange)) {
			nextAnimation = LedAnimationType::Volume;
		} else if (LED_INDICATOR_IS_SET(LedIndicatorType::Rewind)) {
			LED_INDICATOR_CLEAR(LedIndicatorType::Rewind);
			nextAnimation = LedAnimationType::Rewind;
		} else if (LED_INDICATOR_IS_SET(LedIndicatorType::PlaylistProgress)) {
			nextAnimation = LedAnimationType::Playlist;
		} else if (gPlayProperties.currentSpeechActive) {
			nextAnimation = LedAnimationType::Speech;
		} else if (gPlayProperties.playlistFinished) {
			nextAnimation = LedAnimationType::Idle;
		} else if (gPlayProperties.pausePlay && !gPlayProperties.isWebstream) {
			nextAnimation = LedAnimationType::Pause;
		} else if ((gPlayProperties.playMode != BUSY) && (gPlayProperties.playMode != NO_PLAYLIST) && gPlayProperties.audioFileDuration > 0) { // progress for a file/stream with known size
			nextAnimation = LedAnimationType::Progress;
		} else if (gPlayProperties.isWebstream) { // webstream animation (for streams with unknown size); pause animation is also handled by the webstream animation function
			nextAnimation = LedAnimationType::Webstream;
		} else if (gPlayProperties.playMode == NO_PLAYLIST) {
			nextAnimation = LedAnimationType::Idle;
		} else if (gPlayProperties.playMode == BUSY) {
			nextAnimation = LedAnimationType::Busy;
		} else {
			nextAnimation = LedAnimationType::NoNewAnimation; // should not happen
		}

		// check for instant transition if the requested animation has a higher priority then the current one
		if (nextAnimation < activeAnimation) {
			animationActive = false; // abort current animation
			animationTimer = 0;
		}
		// transition to new animation
		if ((!animationActive) && (animationTimer <= 0)) {
			activeAnimation = nextAnimation; // set new animation
			startNewAnimation = true;
		}

		// apply brightness-changes
		if (lastLedBrightness != gLedSettings.Led_Brightness) {
			FastLED.setBrightness(gLedSettings.Led_Brightness);
			lastLedBrightness = gLedSettings.Led_Brightness;
		}

		if (!gLedSettings.Led_AmbientLight || (activeAnimation == LedAnimationType::Shutdown)) {

			// when there is no delay anymore we have to animate something
			if (animationTimer <= 0) {
				AnimationReturnType ret;
				// animate the current animation
				switch (activeAnimation) {
					case LedAnimationType::Boot:
						ret = Animation_Boot(startNewAnimation, *indicator);
						break;

					case LedAnimationType::Shutdown:
						ret = Animation_Shutdown(startNewAnimation, *indicator);
						break;

					case LedAnimationType::Error:
						ret = Animation_Error(startNewAnimation, *indicator);
						break;

					case LedAnimationType::Ok:
						ret = Animation_Ok(startNewAnimation, *indicator);
						break;

					case LedAnimationType::Volume:
						ret = Animation_Volume(startNewAnimation, *indicator);
						break;

					case LedAnimationType::VoltageWarning:
						ret = Animation_VoltageWarning(startNewAnimation, *indicator);
						break;

					case LedAnimationType::BatteryMeasurement:
						ret = Animation_BatteryMeasurement(startNewAnimation, *indicator);
						break;

					case LedAnimationType::Rewind:
						ret = Animation_Rewind(startNewAnimation, *indicator);
						break;

					case LedAnimationType::Playlist:
						ret = Animation_PlaylistProgress(startNewAnimation, *indicator);
						break;

					case LedAnimationType::Idle:
						ret = Animation_Idle(startNewAnimation, *indicator);
						break;

					case LedAnimationType::Busy:
						ret = Animation_Busy(startNewAnimation, *indicator);
						break;

					case LedAnimationType::Speech:
						ret = Animation_Speech(startNewAnimation, *indicator);
						break;

					case LedAnimationType::Pause:
						ret = Animation_Pause(startNewAnimation, *indicator);
						break;

					case LedAnimationType::Progress:
						ret = Animation_Progress(startNewAnimation, *indicator);
						break;

					case LedAnimationType::Download:
						ret = Animation_Download(startNewAnimation, *indicator);
						break;

					case LedAnimationType::Webstream:
						ret = Animation_Webstream(startNewAnimation, *indicator);
						break;

					default:
						*indicator = CRGB::Black;
						FastLED.show();
						ret.animationActive = false;
						ret.animationDelay = 50;
						break;
				}
				// apply delay and state from animation
				animationActive = ret.animationActive;
				animationTimer = ret.animationDelay;
				if (ret.animationRefresh) {
					FastLED.show();
				}
			}
		} else {
			// ambient light mode
			*indicator = CRGB::Black;
			if (gLedSettings.numIndicatorLeds == 1) {
				leds[0].setHSV(gLedSettings.atmoHue, gLedSettings.atmoSaturation, 255);
			} else {
				for (uint8_t i = 0; i < gLedSettings.numIndicatorLeds; i++) {
					leds[i].setHSV(gLedSettings.atmoHue, gLedSettings.atmoSaturation, 255);
				}
			}
			FastLED.show();
			activeAnimation = LedAnimationType::NoNewAnimation;
			animationActive = false;
			animationTimer = 0;
		}

		// get the time to wait and delay the task
		if ((animationTimer > 0) && (animationTimer < taskDelay)) {
			taskDelay = animationTimer;
			if (taskDelay < 5) {
				taskDelay = 5; // minimum delay
			}
		}
		animationTimer -= taskDelay;
		vTaskDelay(portTICK_PERIOD_MS * taskDelay);
	}
	delete[] leds;
	delete indicator;
	vTaskDelete(NULL);
}
#endif

#ifdef NEOPIXEL_ENABLE
// ---------------------------------------------------------------------
// ---------------        ANIMATION-METHODS        ---------------------
// ---------------------------------------------------------------------
// * each function has to be non-blocking.
// * all states are kept in this function.
// * all funcitons return the desired delay and if they are still active
// * the function will be called the next time when the returned delay has
// passed
// * the optional Start Flag signals that the animation is started new

// --------------------------------
// BOOT-UP Animation
// --------------------------------
AnimationReturnType Animation_Boot(const bool startNewAnimation, CRGBSet &leds) {
	(void) startNewAnimation; // start is not used
	// static vars
	static bool showEvenError = false;

	// 10 s without success?
	if (millis() > 10000) {
		leds = CRGB::Red;
		if (showEvenError) {
			// and then draw in the black dots
			for (uint8_t i = 0; i < leds.size(); i += 2) {
				leds[i] = CRGB::Black;
			}
		}
	} else {
		leds = CRGB::Black;
		const uint8_t startLed = (showEvenError) ? 1 : 0;
		for (uint8_t i = startLed; i < leds.size(); i += 2) {
			leds[i] = CRGB::Orange;
		}
	}
	showEvenError = !showEvenError;

	return AnimationReturnType(false, 500, true); // always wait 500 ms
}

// --------------------------------
// Shutdown Animation
// --------------------------------
AnimationReturnType Animation_Shutdown(const bool startNewAnimation, CRGBSet &leds) {
	// return values
	bool animationActive = true;
	int32_t animationDelay = 0;
	// static vars
	static bool singleLedStatus = false;
	static uint32_t animationIndex = 0;
	if (startNewAnimation) {
		animationIndex = 0;
	}

	if (gLedSettings.numIndicatorLeds == 1) {
		leds = CRGB::Black;
		if (millis() - gButtons[gShutdownButton].firstPressedTimestamp <= intervalToLongPress) {
			leds[0] = CRGB::Red;
			animationDelay = 5;
		} else {
			if (singleLedStatus) {
				leds[0] = CRGB::Red;
			}
			singleLedStatus = !singleLedStatus;
			animationDelay = 50;
		}
		animationActive = false;
	} else {
		if ((millis() - gButtons[gShutdownButton].firstPressedTimestamp >= intervalToLongPress) && (animationIndex >= leds.size())) {
			animationDelay = 50;
			if (!gButtons[gShutdownButton].isPressed) {
				// increase animation index to bail out, if we had a kombi-button
				animationIndex++;
				if (animationIndex >= leds.size() + 3) {
					animationActive = false; // this is approx. 150ms after the button is released
				}
			}
		} else {
			if (animationIndex == 0) {
				leds = CRGB::Black;
			}
			if (animationIndex < leds.size()) {
				leds[Led_Address(animationIndex)] = CRGB::Red;
				if (gButtons[gShutdownButton].currentState) {
					animationDelay = 5;
					animationActive = false;
				} else {
					animationDelay = intervalToLongPress / leds.size();
				}
				animationIndex++;
			}
		}
	}
	return AnimationReturnType(animationActive, animationDelay, true);
}

// --------------------------------
// Error Animation
// --------------------------------
AnimationReturnType Animation_Error(const bool startNewAnimation, CRGBSet &leds) {
	// return values
	bool animationActive = true;
	uint16_t animationDelay = 0;
	// static vars
	static bool singleLedStatus = false;
	static uint16_t animationIndex = 0;
	if (startNewAnimation) {
		animationIndex = 0;
	}

	if (gLedSettings.numIndicatorLeds == 1) {
		leds = CRGB::Black;
		if (singleLedStatus) {
			leds[0] = CRGB::Red;
		}
		singleLedStatus = !singleLedStatus;

		if (animationIndex < 5) {
			animationIndex++;
			animationDelay = 100;
		} else {
			animationActive = false;
		}
	} else {
		leds = CRGB::Red;
		if (animationIndex > 0) {
			animationActive = false;
		} else {
			animationIndex++;
			animationDelay = 200;
		}
	}
	return AnimationReturnType(animationActive, animationDelay, true);
}
// --------------------------------
// OK Animation
// --------------------------------
AnimationReturnType Animation_Ok(const bool startNewAnimation, CRGBSet &leds) {
	// return values
	bool animationActive = true;
	uint16_t animationDelay = 0;
	// static vars
	static bool singleLedStatus = false;
	static uint16_t animationIndex = 0;
	if (startNewAnimation) {
		animationIndex = 0;
	}

	if (gLedSettings.numIndicatorLeds == 1) {
		leds = CRGB::Black;
		if (singleLedStatus) {
			leds[0] = CRGB::Green;
		}
		singleLedStatus = !singleLedStatus;

		if (animationIndex < 5) {
			animationIndex++;
			animationDelay = 100;
		} else {
			animationActive = false;
		}
	} else {
		leds = CRGB::Green;
		if (animationIndex > 0) {
			animationActive = false;
		} else {
			animationIndex++;
			animationDelay = 400;
		}
	}
	return AnimationReturnType(animationActive, animationDelay, true);
}

// --------------------------------
// VoltageWarning Animation
// --------------------------------
// Single + Multiple LEDs: flashes red three times if battery-voltage is low
AnimationReturnType Animation_VoltageWarning(const bool startNewAnimation, CRGBSet &leds) {
	// return values
	bool animationActive = true;
	uint16_t animationDelay = 0;
	// static vars
	static uint16_t animationIndex = 0;

	if (startNewAnimation) {
		animationIndex = 0;
	}

	leds = CRGB::Black;
	if (animationIndex % 2 == 0) {
		leds = CRGB::Red;
	}

	if (animationIndex < 6) {
		animationIndex++;
		animationDelay = 200;
	} else {
		animationActive = false;
	}
	return AnimationReturnType(animationActive, animationDelay, true);
}

// --------------------------------
// Webstream Animation
// --------------------------------
// Animates the progress and Pause of a Webstream
AnimationReturnType Animation_Webstream(const bool startNewAnimation, CRGBSet &leds) {
	// return values
	bool animationActive = false;
	bool refresh = false;
	int32_t animationDelay = 0;
	// static vars
	static uint8_t ledPosWebstream = 0;
	static uint8_t webstreamColor = 0;
	static uint16_t timerProgress = 0;

	// pause-animation
	if (gPlayProperties.pausePlay) {
		leds = CRGB::Black;
		CRGB::HTMLColorCode generalColor = CRGB::Orange;
		if (OPMODE_BLUETOOTH_SINK == System_GetOperationMode()) {
			generalColor = CRGB::Blue;
		}
		if (gLedSettings.numIndicatorLeds == 1) {
			leds[0] = generalColor;
		} else {
			leds[Led_Address(ledPosWebstream)] = generalColor;
			leds[(Led_Address(ledPosWebstream) + leds.size() / 2) % leds.size()] = generalColor;
		}
		animationDelay = 10;
		timerProgress = 0; // directly show new animation after pause
		refresh = true;
	} else {
		if (startNewAnimation || timerProgress == 0) {
			leds = CRGB::Black;
			timerProgress = 100;
			if (ledPosWebstream + 1 < leds.size()) {
				ledPosWebstream++;
			} else {
				ledPosWebstream = 0;
			}
			if (System_AreControlsLocked()) {
				leds[Led_Address(ledPosWebstream)] = CRGB::Red;
				if (gLedSettings.numIndicatorLeds > 1) {
					leds[(Led_Address(ledPosWebstream) + leds.size() / 2) % leds.size()] = CRGB::Red;
				}
			} else {
				if (gLedSettings.numIndicatorLeds == 1) {
					leds[0].setHue(webstreamColor++);
				} else {
					if (OPMODE_BLUETOOTH_SINK == System_GetOperationMode()) {
						leds[Led_Address(ledPosWebstream)] = CRGB::Blue;
						leds[(Led_Address(ledPosWebstream) + leds.size() / 2) % leds.size()] = CRGB::Blue;
					} else {
						leds[Led_Address(ledPosWebstream)].setHue(webstreamColor);
						leds[(Led_Address(ledPosWebstream) + leds.size() / 2) % leds.size()].setHue(webstreamColor++);
					}
				}
			}
			refresh = true;
		}
		timerProgress--;
		animationDelay = 45;
		if (timerProgress > 0) {
			animationActive = true;
		}
	}
	return AnimationReturnType(animationActive, animationDelay, refresh);
}

// --------------------------------
// Rewind Animation
// --------------------------------
AnimationReturnType Animation_Rewind(const bool startNewAnimation, CRGBSet &leds) {
	// return values
	bool animationActive = false;
	bool refresh = false;
	int32_t animationDelay = 0;
	// static vars
	static uint16_t animationIndex = 0;
	if (startNewAnimation) {
		animationIndex = 0;
	}

	if (gLedSettings.numIndicatorLeds >= 4) {
		animationActive = true;

		if (animationIndex < (leds.size())) {
			leds[Led_Address(leds.size() - 1 - animationIndex)] = CRGB::Black;
			refresh = true;
			animationDelay = 30;
			animationIndex++;
		} else {
			animationActive = false;
		}
	}
	return AnimationReturnType(animationActive, animationDelay, refresh);
}

// --------------------------------
// Idle Animation
// --------------------------------
AnimationReturnType Animation_Idle(const bool startNewAnimation, CRGBSet &leds) {
	// return values
	int32_t animationDelay = 0;
	bool animationActive = true;
	bool refresh = true;
	// static vars
	static int16_t ledIndex = 0;
	// this can be removed to always continue on the last position in idle
	if (startNewAnimation) {
		ledIndex = 0;
	}

	if (ledIndex < leds.size()) {
		CRGB::HTMLColorCode idleColor = Led_GetIdleColor();
		leds = CRGB::Black;
		Led_DrawIdleDots(leds, ledIndex, idleColor);
		if (OPMODE_BLUETOOTH_SOURCE == System_GetOperationMode()) {
			// animate a bit faster in BT-Source to distinguish between the bluetooth modes
			animationDelay = 30 * 10;
		} else {
			animationDelay = 50 * 10;
		}
		ledIndex++;
	} else {
		animationActive = false;
		refresh = false;
		ledIndex = 0;
	}
	return AnimationReturnType(animationActive, animationDelay, refresh);
}

// --------------------------------
// Busy Animation
// --------------------------------
AnimationReturnType Animation_Busy(const bool startNewAnimation, CRGBSet &leds) {
	// return values
	bool animationActive = true;
	int32_t animationDelay = 0;
	// static vars
	static bool singleLedStatus = false;
	static uint16_t animationIndex = 0;
	if (startNewAnimation) {
		animationIndex = 0;
	}
	if (gLedSettings.numIndicatorLeds == 1) {
		leds = CRGB::Black;
		singleLedStatus = !singleLedStatus;
		if (singleLedStatus) {
			leds[0] = CRGB::BlueViolet;
		}
		animationDelay = 100;
		animationActive = false;
	} else {
		if (animationIndex < leds.size()) {
			leds = CRGB::Black;
			CRGB::HTMLColorCode idleColor = Led_GetIdleColor();
			Led_DrawIdleDots(leds, animationIndex, idleColor);
			animationDelay = 50;
			animationIndex++;
		} else {
			animationActive = false;
		}
	}
	return AnimationReturnType(animationActive, animationDelay, true);
}

// --------------------------------
// Pause Animation
// --------------------------------
// Animates the pause if no Webstream is active
AnimationReturnType Animation_Pause(const bool startNewAnimation, CRGBSet &leds) {
	(void) startNewAnimation; // start is not used

	leds = CRGB::Black;
	CRGB::HTMLColorCode generalColor = CRGB::Orange;
	if (OPMODE_BLUETOOTH_SOURCE == System_GetOperationMode()) {
		generalColor = CRGB::Blue;
	}

	uint8_t pauseOffset = 0;
	if (gLedSettings.offsetLedPause) {
		pauseOffset = ((leds.size() / gLedSettings.numIdleDots) / 2) - 1;
	}
	Led_DrawIdleDots(leds, pauseOffset, generalColor);

	return AnimationReturnType(false, 10, true);
}

// --------------------------------
// Speech Animation
// --------------------------------
// only draw yellow pause-dots
AnimationReturnType Animation_Speech(const bool startNewAnimation, CRGBSet &leds) {
	(void) startNewAnimation; // start is not used

	leds = CRGB::Black;
	uint8_t pauseOffset = 0;
	if (gLedSettings.offsetLedPause) {
		pauseOffset = ((leds.size() / gLedSettings.numIdleDots) / 2) - 1;
	}
	Led_DrawIdleDots(leds, pauseOffset, CRGB::Yellow);

	return AnimationReturnType(false, 10, true);
}

// --------------------------------
// Progress in Track Animation
// --------------------------------
AnimationReturnType Animation_Progress(const bool startNewAnimation, CRGBSet &leds) {
	// return values
	int32_t animationDelay = 0;
	// static values
	static double lastPos = 0.0f;
	static bool lastPreviewActive = false;
	static uint8_t lastPreviewTarget = 0;

	// CMD_SEEK_PREVIEW rotary gesture (RotaryEncoder.cpp/AudioPlayer.cpp): while active, the ring shows
	// a not-yet-committed target instead of the actual (unchanged) playback position -- read via these
	// accessors rather than gPlayProperties.currentRelPos, which must not reflect the preview before commit.
	const bool previewActive = AudioPlayer_IsSeekPreviewActive();
	const uint8_t previewTarget = AudioPlayer_GetSeekPreviewTargetPercent();

	if (gPlayProperties.currentRelPos != lastPos || previewActive != lastPreviewActive || (previewActive && (previewTarget != lastPreviewTarget)) || startNewAnimation) {
		lastPos = gPlayProperties.currentRelPos;
		lastPreviewActive = previewActive;
		lastPreviewTarget = previewTarget;
		leds = CRGB::Black;
		if (gLedSettings.numIndicatorLeds == 1) {
			if (previewActive) {
				// A single LED can't show ring-position and cursor separately -- solid blue is an
				// unambiguous "preview active" signal, at the cost of not showing the target itself.
				leds[0] = CRGB::Blue;
			} else {
				leds[0].setHue((uint8_t) (85 - ((double) 90 / 100) * gPlayProperties.currentRelPos));
			}
		} else {
			const uint32_t ledValue = std::clamp<uint32_t>(map(gPlayProperties.currentRelPos, 0, 98, 0, leds.size() * gLedSettings.dimmableStates), 0, leds.size() * gLedSettings.dimmableStates);
			const uint8_t fullLeds = ledValue / gLedSettings.dimmableStates;
			const uint8_t lastLed = ledValue % gLedSettings.dimmableStates;
			for (uint8_t led = 0; led < fullLeds; led++) {
				if (System_AreControlsLocked()) {
					leds[Led_Address(led)] = CRGB::Red;
				} else if (previewActive) {
					leds[Led_Address(led)] = CRGB::Yellow;
				} else if (!gPlayProperties.pausePlay) { // Hue-rainbow
					leds[Led_Address(led)].setHue((uint8_t) (((float) gLedSettings.progressHueEnd - (float) gLedSettings.progressHueStart) / (leds.size() - 1) * led + gLedSettings.progressHueStart));
				}
			}
			if (lastLed > 0) {
				if (System_AreControlsLocked()) {
					leds[Led_Address(fullLeds)] = CRGB::Red;
				} else if (previewActive) {
					leds[Led_Address(fullLeds)] = CRGB::Yellow;
				} else {
					leds[Led_Address(fullLeds)].setHue((uint8_t) (((float) gLedSettings.progressHueEnd - (float) gLedSettings.progressHueStart) / (leds.size() - 1) * fullLeds + gLedSettings.progressHueStart));
				}
				leds[Led_Address(fullLeds)] = Led_DimColor(leds[Led_Address(fullLeds)], lastLed);
			}
			if (previewActive) {
				// Cursor is drawn last so it overrides whatever the ring fill just put at that position.
				const uint32_t cursorValue = std::clamp<uint32_t>(map(previewTarget, 0, 100, 0, leds.size() * gLedSettings.dimmableStates), 0, leds.size() * gLedSettings.dimmableStates);
				const uint8_t cursorLed = std::min<uint8_t>(cursorValue / gLedSettings.dimmableStates, leds.size() - 1);
				const uint8_t cursorSub = cursorValue % gLedSettings.dimmableStates;
				leds[Led_Address(cursorLed)] = (cursorSub > 0) ? Led_DimColor(CRGB::Blue, cursorSub) : CRGB::Blue;
			}
		}
		animationDelay = 10;
	}
	return AnimationReturnType(false, animationDelay, true);
}

// --------------------------------
// MediaHub Download Progress Animation
// --------------------------------
// Own, non-suspending animation (concept §12): unlike Led_ShowOtaProgress(),
// this goes through the normal Led_Task priority ladder instead of
// suspending it, so e.g. an error/voltage-warning can still interrupt it.
// Fill level comes from Led_SetDownloadProgress(), driven by MediaHub.
AnimationReturnType Animation_Download(const bool startNewAnimation, CRGBSet &leds) {
	int32_t animationDelay = 0;
	static uint16_t lastPercent = 0xFFFF; // force first draw

	if (Led_DownloadPercent != lastPercent || startNewAnimation) {
		lastPercent = Led_DownloadPercent;
		leds = CRGB::Black;
		if (gLedSettings.numIndicatorLeds == 1) {
			leds[0] = CRGB::DeepSkyBlue;
			leds[0].nscale8((uint8_t) map(Led_DownloadPercent, 0, 100, 40, 255));
		} else {
			const uint32_t ledValue = std::clamp<uint32_t>(map(Led_DownloadPercent, 0, 100, 0, leds.size() * gLedSettings.dimmableStates), 0, leds.size() * gLedSettings.dimmableStates);
			const uint8_t fullLeds = ledValue / gLedSettings.dimmableStates;
			const uint8_t lastLed = ledValue % gLedSettings.dimmableStates;
			for (uint8_t led = 0; led < fullLeds; led++) {
				leds[Led_Address(led)] = CRGB::DeepSkyBlue;
			}
			if (lastLed > 0 && fullLeds < leds.size()) {
				leds[Led_Address(fullLeds)] = Led_DimColor(CRGB::DeepSkyBlue, lastLed);
			}
		}
		animationDelay = 10;
	}
	return AnimationReturnType(false, animationDelay, true);
}

// --------------------------------
// Volume-Change Animation
// --------------------------------
// - Single-LED: led indicates loudness between green (low) => red (high)
// - Multiple-LEDs: number of LEDs indicate loudness; gradient is shown between
//   green (low) => red (high)
AnimationReturnType Animation_Volume(const bool startNewAnimation, CRGBSet &leds) {
	// return-values
	int32_t animationDelay = 0;
	bool animationActive = true;
	// static values
	static uint16_t cyclesWaited = 0;

	// wait for further volume changes within next 20ms for 50 cycles = 1s
	const uint32_t ledValue = std::clamp<uint32_t>(map(AudioPlayer_GetCurrentVolume(), AudioPlayer_GetMinVolume(), AudioPlayer_GetMaxVolume(), 0, leds.size() * gLedSettings.dimmableStates), 0, leds.size() * gLedSettings.dimmableStates);
	const uint8_t fullLeds = ledValue / gLedSettings.dimmableStates;
	const uint8_t lastLed = ledValue % gLedSettings.dimmableStates;

	leds = CRGB::Black;

	if (gLedSettings.numIndicatorLeds == 1) {
		const uint8_t hue = 85 - (90 * ((double) AudioPlayer_GetCurrentVolume() / (double) AudioPlayer_GetMaxVolumeSpeaker()));
		leds[0].setHue(hue);
	} else {
		/*
		 * (Inverse) color-gradient from green (85) back to (still)
		 * red (250) using unsigned-cast.
		 */
		for (int led = 0; led < fullLeds; led++) {
			const uint8_t hue = (-86.0f) / (leds.size() - 1) * led + 85.0f;
			leds[Led_Address(led)].setHue(hue);
		}
		if (lastLed > 0) {
			const uint8_t hue = (-86.0f) / (leds.size() - 1) * fullLeds + 85.0f;
			leds[Led_Address(fullLeds)].setHue(hue);
			leds[Led_Address(fullLeds)] = Led_DimColor(leds[Led_Address(fullLeds)], lastLed);
		}
	}

	// reset animation if volume changes
	if (LED_INDICATOR_IS_SET(LedIndicatorType::VolumeChange) || startNewAnimation) {
		LED_INDICATOR_CLEAR(LedIndicatorType::VolumeChange);
		cyclesWaited = 0;
	}

	if (cyclesWaited < LED_VOLUME_INDICATOR_NUM_CYCLES) {
		animationDelay = 20;
		cyclesWaited++;
	} else {
		animationActive = false;
		cyclesWaited = 0;
	}
	return AnimationReturnType(animationActive, animationDelay, true);
}

// --------------------------------
// PLAYLIST-PROGRESS Animation
// --------------------------------
AnimationReturnType Animation_PlaylistProgress(const bool startNewAnimation, CRGBSet &leds) {
	// return-values
	static bool animationActive = false; // signals if the animation is currently active
	int32_t animationDelay = 0;
	// static variables for animation
	static uint32_t animationCounter = 0; // counter-variable to loop through leds or to wait
	static uint32_t staticLastBarLenghtPlaylist = 0; // variable to remember the last length of the progress-bar (for connecting animations)
	static uint32_t staticLastTrack = 0; // variable to remember the last track (for connecting animations)

	if (gLedSettings.numIndicatorLeds >= 4) {
		const uint16_t currentTrack = (gPlayProperties.playlist) ? gPlayProperties.playlist->size() : 0;
		if (currentTrack > 1 && gPlayProperties.currentTrackNumber < currentTrack) {
			const uint32_t ledValue = std::clamp<uint32_t>(map(gPlayProperties.currentTrackNumber, 0, currentTrack - 1, 0, leds.size() * gLedSettings.dimmableStates), 0, leds.size() * gLedSettings.dimmableStates);
			const uint8_t fullLeds = ledValue / gLedSettings.dimmableStates;
			const uint8_t lastLed = ledValue % gLedSettings.dimmableStates;
			static LedPlaylistProgressStates animationState = LedPlaylistProgressStates::Done; // Statemachine-variable of this animation

			if (LED_INDICATOR_IS_SET(LedIndicatorType::PlaylistProgress)) {
				LED_INDICATOR_CLEAR(LedIndicatorType::PlaylistProgress);
				// check if we need to animate a transition between from an already running animation
				// only animate diff, if triggered again
				if (!startNewAnimation) {
					// forward progress
					if (staticLastTrack < gPlayProperties.currentTrackNumber) {
						if (animationState > LedPlaylistProgressStates::FillBar) {
							animationState = LedPlaylistProgressStates::FillBar;
							animationCounter = staticLastBarLenghtPlaylist;
						}
						// backwards progress
					} else if (staticLastTrack > gPlayProperties.currentTrackNumber) {
						if (staticLastBarLenghtPlaylist < fullLeds) {
							animationState = LedPlaylistProgressStates::FillBar;
							animationCounter = staticLastBarLenghtPlaylist;
						} else {
							animationState = LedPlaylistProgressStates::EmptyBarToTarget;
							animationCounter = staticLastBarLenghtPlaylist;
						}
					}
				}
				staticLastTrack = gPlayProperties.currentTrackNumber;
			}

			if (startNewAnimation) {
				animationActive = true;
				animationCounter = 0;
				animationState = LedPlaylistProgressStates::FillBar;
			}

			animationDelay = 30;
			uint8_t barLength = 0;
			switch (animationState) {
				case LedPlaylistProgressStates::FillBar:
					barLength = animationCounter;
					if (animationCounter >= fullLeds) {
						animationState = LedPlaylistProgressStates::Wait;
						animationCounter = 0;
					} else {
						animationCounter++;
					}
					break;
				case LedPlaylistProgressStates::Wait:
					// wait
					animationCounter++;
					if (animationCounter >= 50) {
						animationState = LedPlaylistProgressStates::EmptyBar;
						animationCounter = fullLeds;
					}
					barLength = fullLeds;
					break;
				case LedPlaylistProgressStates::EmptyBar:
					// negative
					barLength = animationCounter;
					if (animationCounter == 0) {
						animationState = LedPlaylistProgressStates::Done;
					} else {
						animationCounter--;
					}
					break;
				case LedPlaylistProgressStates::EmptyBarToTarget:
					// move back to target and wait there
					barLength = animationCounter;
					if (animationCounter <= fullLeds) {
						animationState = LedPlaylistProgressStates::Wait;
						animationCounter = 0;
					} else {
						animationCounter--;
					}
					break;
				default:
					// done
					animationActive = false;
					break;
			}

			// draw bar
			leds = CRGB::Black;
			for (uint8_t i = 0; i < barLength; i++) {
				leds[Led_Address(i)] = CRGB::Blue;
			}
			if (barLength == fullLeds && lastLed > 0) {
				leds[Led_Address(barLength)] = Led_DimColor(CRGB::Blue, lastLed);
			}
			staticLastBarLenghtPlaylist = barLength;
		}
	} else {
		// nothing to show. Just clear indicator
		LED_INDICATOR_CLEAR(LedIndicatorType::PlaylistProgress);
	}

	return AnimationReturnType(animationActive, animationDelay, true);
}

// --------------------------------
// BATTERY_MEASUREMENT Animation
// --------------------------------
// Single-LED: indicates voltage coloured between gradient green (high) => red (low)
// Multi-LED: number of LEDs indicates voltage-level with having green >= 60% ; orange < 60% + >= 30% ; red < 30%
AnimationReturnType Animation_BatteryMeasurement(const bool startNewAnimation, CRGBSet &leds) {
	// return-values
	static bool animationActive = false;
	bool refresh = false;
	int32_t animationDelay = 0;
	// static variables for animation
	static float staticBatteryLevel = 0.0f; // variable to store the measured battery-voltage
	static uint32_t filledLedCount = 0; // loop variable to animate led-bar

	LED_INDICATOR_CLEAR(LedIndicatorType::Voltage);

	if (startNewAnimation) {
	#ifdef BATTERY_MEASURE_ENABLE
		float batteryLevel = Battery_EstimateLevel();
	#else
		float batteryLevel = 1.0f;
	#endif
		if (batteryLevel < 0.0f) { // If voltage is too low or no battery is connected
			LED_INDICATOR_SET(LedIndicatorType::Error);
			return AnimationReturnType(); // abort to indicate error
		}
		staticBatteryLevel = batteryLevel;
		filledLedCount = 0;
		animationActive = true;
		leds = CRGB::Black;
		refresh = true;
	}
	if (gLedSettings.numIndicatorLeds == 1) {
		if (staticBatteryLevel < 0.3) {
			leds[0] = CRGB::Red;
		} else if (staticBatteryLevel < 0.6) {
			leds[0] = CRGB::Orange;
		} else {
			leds[0] = CRGB::Green;
		}
		refresh = true;

		animationDelay = 20 * 100;
		animationActive = false;
	} else {
		uint8_t numLedsToLight = std::clamp<uint8_t>(staticBatteryLevel * leds.size(), 0, leds.size());

		// fill all needed LEDs
		if (filledLedCount < numLedsToLight) {
			if (staticBatteryLevel < 0.3f) {
				leds[Led_Address(filledLedCount)] = CRGB::Red;
			} else if (staticBatteryLevel < 0.6f) {
				leds[Led_Address(filledLedCount)] = CRGB::Orange;
			} else {
				leds[Led_Address(filledLedCount)] = CRGB::Green;
			}
			refresh = true;

			filledLedCount++;
			animationDelay = 20;
		} else { // Wait a little
			animationDelay = 20 * 100;
			animationActive = false;
		}
	}
	return AnimationReturnType(animationActive, animationDelay, refresh);
}
#endif

void Led_TaskPause(void) {
#ifdef NEOPIXEL_ENABLE
	if (Led_TaskHandle != NULL) {
		vTaskSuspend(Led_TaskHandle);
		FastLED.clear(true);
	}
#endif
}

void Led_TaskResume(void) {
#ifdef NEOPIXEL_ENABLE
	if (Led_TaskHandle != NULL) {
		vTaskResume(Led_TaskHandle);
	}
#endif
}

// Feeds the Download animation's priority check and fill level (concept §12);
// pure state, picked up by Led_Task on its next iteration.
void Led_SetDownloadProgress(bool active, uint8_t percent) {
#ifdef NEOPIXEL_ENABLE
	Led_DownloadActive = active;
	Led_DownloadPercent = percent;
#endif
}

// Shows OTA-update progress on the indicator LEDs while Led_Task is suspended (see
// Led_TaskPause(), called from System_PauseTasksDuringUpload()). No-op if Neopixel is
// disabled or the strip hasn't been initialized yet. With a single indicator LED (which
// can't show a fill level), blinks it instead, matching how other animations handle that case.
void Led_ShowOtaProgress(uint8_t percent) {
#ifdef NEOPIXEL_ENABLE
	if ((leds == nullptr) || (gLedSettings.numIndicatorLeds == 0)) {
		return;
	}
	if (percent > 100) {
		percent = 100;
	}
	if (gLedSettings.numIndicatorLeds == 1) {
		// a single LED can't show a fill level; blink it instead, like other single-LED animations
		static uint32_t lastToggle = 0;
		static bool blinkOn = false;
		const uint32_t now = millis();
		if (now - lastToggle >= 250) {
			lastToggle = now;
			blinkOn = !blinkOn;
		}
		leds[0] = blinkOn ? CRGB::Blue : CRGB::Black;
		FastLED.show();
		return;
	}
	const uint8_t litCount = (uint8_t) (((uint16_t) percent * gLedSettings.numIndicatorLeds) / 100);
	for (uint8_t i = 0; i < gLedSettings.numIndicatorLeds; i++) {
		leds[i] = (i < litCount) ? CRGB::Blue : CRGB::Black;
	}
	FastLED.show();
#endif
}
