biologist79/ESPuino/src/Web.cpp

#include <Arduino.h>
#include "settings.h"

#include "Web.h"

#include "ArduinoJson.h"
#include "AsyncJson.h"
#include "AudioPlayer.h"
#include "Battery.h"
#include "Bluetooth.h"
#include "Button.h"
#include "Cmd.h"
#include "Common.h"
#include "ESPAsyncWebServer.h"
#include "EnumUtils.h"
#include "Ftp.h"
#include "HTMLbinary.h"
#include "HallEffectSensor.h"
#include "Led.h"
#include "Log.h"
#include "MediaHub.h"
#include "MemX.h"
#include "Mqtt.h"
#include "Rfid.h"
#include "RfidPn5180.h"
#include "RotaryEncoder.h"
#include "SdCard.h"
#include "System.h"
#include "Wlan.h"
#include "freertos/ringbuf.h"
#include "gitrevision.h"
#include "platforminfo.h"
#include "soc/timer_group_reg.h"
#include "soc/timer_group_struct.h"

#include <Update.h>
#include <WiFi.h>
#include <atomic>
#include <esp_task_wdt.h>
#include <nvs.h>

typedef struct {
	char nvsKey[cardIdStringSize];
	char nvsEntry[512];
} nvs_t;

AsyncWebServer wServer(80);
AsyncWebSocket ws("/ws");
AsyncEventSource events("/events");

static bool webserverStarted = false;

static const uint32_t start_chunk_size = 16384; // bigger chunks increase write-performance to SD-Card
static constexpr uint32_t nr_of_buffers = 2; // at least two buffers. No speed improvement yet with more than two. Kept at 2 to save ~16KB heap during uploads.

static constexpr size_t retry_count = 3; // how often we retry is a malloc fails (also the times we halfe the chunk_size)

uint8_t *buffer[nr_of_buffers];
size_t chunk_size;
std::atomic<uint32_t> size_in_buffer[nr_of_buffers];
std::atomic<bool> buffer_full[nr_of_buffers];
uint32_t index_buffer_write = 0;
uint32_t index_buffer_read = 0;

static SemaphoreHandle_t explorerFileUploadFinished;
static TaskHandle_t fileStorageTaskHandle;
static std::atomic<bool> uploadAborted = false;

void Web_DumpSdToNvs(const char *_filename);
static void handleUpload(AsyncWebServerRequest *request, String filename, size_t index, uint8_t *data, size_t len, bool final);
// Raw (non-multipart) request body: one PUT/POST per file, the target path
// (folder + filename) travels in the "path" query param since a raw body
// carries no per-part filename. The client is responsible for looping over
// multiple files sequentially - see the double-buffer/writer-task machinery
// below, which only supports one upload in flight at a time.
static void explorerHandleFileUpload(AsyncWebServerRequest *request, uint8_t *data, size_t len, size_t index, size_t total);
static void explorerHandleFileStorageTask(void *parameter);
static void explorerHandleListRequest(AsyncWebServerRequest *request);
static void explorerHandleDownloadRequest(AsyncWebServerRequest *request);
static void explorerHandleDeleteRequest(AsyncWebServerRequest *request);
static void explorerHandleCreateRequest(AsyncWebServerRequest *request);
static void explorerHandleRenameRequest(AsyncWebServerRequest *request);
static void explorerHandleAudioRequest(AsyncWebServerRequest *request);
static void handleTrackProgressRequest(AsyncWebServerRequest *request);
static void handleGetSavedSSIDs(AsyncWebServerRequest *request);
static void handleGetWifiStatus(AsyncWebServerRequest *request);
static void handlePostWifiTest(AsyncWebServerRequest *request, JsonVariant &json);
static void handlePostSavedSSIDs(AsyncWebServerRequest *request, JsonVariant &json);
static void handleDeleteSavedSSIDs(AsyncWebServerRequest *request);
static void handleGetActiveSSID(AsyncWebServerRequest *request);
static void handleGetWiFiConfig(AsyncWebServerRequest *request);
static void handlePostWiFiConfig(AsyncWebServerRequest *request, JsonVariant &json);
static void handleCoverImageRequest(AsyncWebServerRequest *request);
static void handleBluetoothScanRequest(AsyncWebServerRequest *request);
static void handleBluetoothStatusRequest(AsyncWebServerRequest *request);
static void handleBluetoothResultsRequest(AsyncWebServerRequest *request);
static void handleBluetoothConnectRequest(AsyncWebServerRequest *request, JsonVariant &json);
static void handleWiFiScanRequest(AsyncWebServerRequest *request);
static void handleGetRFIDRequest(AsyncWebServerRequest *request);
static void handlePostRFIDRequest(AsyncWebServerRequest *request, JsonVariant &json);
static void handleDeleteRFIDRequest(AsyncWebServerRequest *request);
static void handleGetMediaHubServers(AsyncWebServerRequest *request);
static void handlePostMediaHubServers(AsyncWebServerRequest *request, JsonVariant &json);
static void handleDeleteMediaHubServers(AsyncWebServerRequest *request);
static void handleGetInfo(AsyncWebServerRequest *request);
static void handleGetSettings(AsyncWebServerRequest *request);
static void handlePostSettings(AsyncWebServerRequest *request, JsonVariant &json);
static void handleGetOperationMode(AsyncWebServerRequest *request);
static void handlePostOperationMode(AsyncWebServerRequest *request, JsonVariant &json);
static void handleDebugRequest(AsyncWebServerRequest *request);

static void onWebsocketEvent(AsyncWebSocket *server, AsyncWebSocketClient *client, AwsEventType type, void *arg, uint8_t *data, size_t len);
static void settingsToJSON(JsonObject obj, const String section);
static WebsocketCodeType JSONToSettings(JsonObject obj);
static void webserverStart(void);

static String slixPrivacyPasswordToHex(const SlixPrivacyPassword &password) {
	char hex[9];
	snprintf(hex, sizeof(hex), "%02X%02X%02X%02X", password[0], password[1], password[2], password[3]);
	return String(hex);
}

static SlixPrivacyPassword slixPrivacyPasswordFromPrefs(void) {
	SlixPrivacyPassword password = SLIX_PRIVACY_PASSWORD_DEFAULT;
	if (gPrefsRfid.getBytesLength(SLIX_PRIVACY_PASSWORD_NVS_KEY) == password.size()) {
		gPrefsRfid.getBytes(SLIX_PRIVACY_PASSWORD_NVS_KEY, password.data(), password.size());
	}
	return password;
}

// IPAddress converters, for a description see: https://arduinojson.org/news/2021/05/04/version-6-18-0/
void convertFromJson(JsonVariantConst src, IPAddress &dst) {
	dst = IPAddress();
	dst.fromString(src.as<const char *>());
}
bool canConvertFromJson(JsonVariantConst src, const IPAddress &) {
	if (!src.is<const char *>()) {
		return false; // this is not a string
	}
	IPAddress dst;
	return dst.fromString(src.as<const char *>());
}

// If PSRAM is available use it allocate memory for JSON-objects
struct SpiRamAllocator : ArduinoJson::Allocator {
	void *allocate(size_t size) override {
		return ps_malloc(size);
	}
	void deallocate(void *pointer) override {
		free(pointer);
	}
	void *reallocate(void *ptr, size_t new_size) override {
		return ps_realloc(ptr, new_size);
	}
};

static void destroyDoubleBuffer() {
	for (size_t i = 0; i < nr_of_buffers; i++) {
		free(buffer[i]);
		buffer[i] = nullptr;
	}
}

static bool allocateDoubleBuffer() {
	const auto checkAndAlloc = [](uint8_t *&ptr, const size_t memSize) -> bool {
		if (ptr) {
			// memory is there, so nothing to do
			return true;
		}
		// try to allocate buffer in faster internal RAM, not in PSRAM
		// ptr = (uint8_t *) malloc(memSize);
		ptr = (uint8_t *) heap_caps_aligned_alloc(32, memSize, MALLOC_CAP_DEFAULT | MALLOC_CAP_INTERNAL);
		return (ptr != nullptr);
	};

	chunk_size = start_chunk_size;
	size_t retries = retry_count;
	while (retries) {
		if (chunk_size < 256) {
			// give up, since there is not even 256 bytes of memory left
			break;
		}
		bool success = true;
		for (size_t i = 0; i < nr_of_buffers; i++) {
			success &= checkAndAlloc(buffer[i], chunk_size);
		}
		if (success) {
			return true;
		} else {
			// one of our buffer went OOM --> free all buffer and retry with less chunk size
			destroyDoubleBuffer();
			chunk_size /= 2;
			retries--;
		}
	}
	destroyDoubleBuffer();
	return false;
}

void handleUploadError(AsyncWebServerRequest *request, int code) {
	if (request->_tempObject) {
		// we already have an error entered
		return;
	}
	// send the error to the client and record it in the request
	request->_tempObject = new int(code);
	request->send(code);
}

static void serveProgmemFiles(const String &uri, const String &contentType, const uint8_t *content, size_t len) {
	wServer.on(uri.c_str(), HTTP_GET, [contentType, content, len](AsyncWebServerRequest *request) {
		AsyncWebServerResponse *response;

		const bool etag = request->hasHeader("If-None-Match") && request->getHeader("If-None-Match")->value().equals(gitRevShort);
		if (etag) {
			response = request->beginResponse(304);
		} else {
			response = request->beginResponse(200, contentType, content, len);
			response->addHeader("Content-Encoding", "gzip");
		}
		// no-cache (not "no-store"): browser may keep a local copy, but must always revalidate via ETag
		// before using it. That way repeat loads cost only a small conditional request (304 if unchanged),
		// while a firmware update (new gitRevShort) is picked up immediately instead of serving a stale
		// cached copy for the "immutable"/long-max-age duration.
		response->addHeader("Cache-Control", "no-cache");
		response->addHeader("ETag", gitRevShort); // use git revision as digest
		request->send(response);
	});
}

class OneParamRewrite : public AsyncWebRewrite {
protected:
	String _urlPrefix;
	int _paramIndex;
	String _paramsBackup;

public:
	OneParamRewrite(const char *from, const char *to)
		: AsyncWebRewrite(from, to) {

		_paramIndex = _from.indexOf('{');

		if (_paramIndex >= 0 && _from.endsWith("}")) {
			_urlPrefix = _from.substring(0, _paramIndex);
			int index = _params.indexOf('{');
			if (index >= 0) {
				_params = _params.substring(0, index);
			}
		} else {
			_urlPrefix = _from;
		}
		_paramsBackup = _params;
	}

	bool match(AsyncWebServerRequest *request) override {
		if (request->url().startsWith(_urlPrefix)) {
			if (_paramIndex >= 0) {
				_params = _paramsBackup + request->url().substring(_paramIndex);
			} else {
				_params = _paramsBackup;
			}
			return true;

		} else {
			return false;
		}
	}
};

// List all key in NVS for a given namespace
// callback function is called for every key with userdefined data object
bool listNVSKeys(const char *_namespace, void *data, bool (*callback)(const char *key, void *data)) {
	constexpr const char *partname = "nvs";
#if (defined(ESP_ARDUINO_VERSION_MAJOR) && (ESP_ARDUINO_VERSION_MAJOR >= 3))
	nvs_iterator_t it = nullptr;
	esp_err_t res = nvs_entry_find(partname, _namespace, NVS_TYPE_ANY, &it);
	while (res == ESP_OK) {
		nvs_entry_info_t info;
		nvs_entry_info(it, &info);
		if (isNumber(info.key)) {
			if (!callback(info.key, data)) {
				nvs_release_iterator(it);
				return false;
			}
		}
		// finished, NEXT
		res = nvs_entry_next(&it);
	}
	nvs_release_iterator(it);
#else
	nvs_iterator_t it = nvs_entry_find(partname, _namespace, NVS_TYPE_ANY);
	if (it == nullptr) {
		// no entries found
		return false;
	}
	while (it != nullptr) {
		nvs_entry_info_t info;
		nvs_entry_info(it, &info); // we got the key name here
		// some basic sanity checks
		if (isNumber(info.key)) {
			if (!callback(info.key, data)) {
				nvs_release_iterator(it);
				return false;
			}
		}
		// finished, NEXT!
		it = nvs_entry_next(it);
	}
#endif
	return true;
}

// callback for writing a NVS entry to file
bool DumpNvsToSdCallback(const char *key, void *data) {
	String s = gPrefsRfid.getString(key);
	File *file = (File *) data;
	file->printf("%s%s%s%s\n", stringOuterDelimiter, key, stringOuterDelimiter, s.c_str());
	return true;
}

// Dumps all RFID-entries from NVS into a file on SD-card
bool Web_DumpNvsToSd(const char *_namespace, const char *_destFile) {
	File file = gFSystem.open(_destFile, FILE_WRITE);
	if (!file) {
		return false;
	}
	// write UTF-8 BOM
	file.write(0xEF);
	file.write(0xBB);
	file.write(0xBF);
	// list all NVS keys
	bool success = listNVSKeys(_namespace, &file, DumpNvsToSdCallback);
	file.close();
	return success;
}

// First request will return 0 results unless you start scan from somewhere else (loop/setup)
// Do not request more often than 3-5 seconds
static void handleWiFiScanRequest(AsyncWebServerRequest *request) {
	String json = "[";
	int n = WiFi.scanComplete();
	if (n == -2) {
		// -2 if scan not triggered
		WiFi.scanNetworks(true, false, true, 120);
	} else if (n) {
		for (int i = 0; i < n; ++i) {
			if (i > 9) {
				break;
			}
			// calculate RSSI as quality in percent
			int quality;
			if (WiFi.RSSI(i) <= -100) {
				quality = 0;
			} else if (WiFi.RSSI(i) >= -50) {
				quality = 100;
			} else {
				quality = 2 * (WiFi.RSSI(i) + 100);
			}
			if (i) {
				json += ",";
			}
			json += "{";
			json += "\"ssid\":\"" + WiFi.SSID(i) + "\"";
			json += ",\"bssid\":\"" + WiFi.BSSIDstr(i) + "\"";
			json += ",\"rssi\":" + String(WiFi.RSSI(i));
			json += ",\"channel\":" + String(WiFi.channel(i));
			json += ",\"secure\":" + String(WiFi.encryptionType(i));
			json += ",\"quality\":" + String(quality); // WiFi strength in percent
			json += ",\"wico\":\"w" + String(int(round(map(quality, 0, 100, 1, 4)))) + "\""; // WiFi strength icon ("w1"-"w4")
			json += ",\"pico\":\"" + String((WIFI_AUTH_OPEN == WiFi.encryptionType(i)) ? "" : "pw") + "\""; // auth icon ("p1" for secured)
			json += "}";
		}
		WiFi.scanDelete();
		if (WiFi.scanComplete() == -2) {
			WiFi.scanNetworks(true, false, true, 120);
		}
	}
	json += "]";
	request->send(200, "application/json", json);
	json = String();
}

unsigned long lastCleanupClientsTimestamp;

void Web_Cyclic(void) {
	webserverStart();
	if ((millis() - lastCleanupClientsTimestamp) > 1000u) {
		// cleanup closed/deserted websocket clients once per second
		lastCleanupClientsTimestamp = millis();
		ws.cleanupClients();
	}
}

void Web_Exit(void) {
	esp_task_wdt_reset();
	if (webserverStarted) {
		// Gracefully abort active file storage task if running
		if (fileStorageTaskHandle != NULL) {
			uploadAborted = true;
			xTaskNotify(fileStorageTaskHandle, 2u, eSetValueWithOverwrite);
			// Wait for the task to exit and close open file handles
			uint32_t startWait = millis();
			while (fileStorageTaskHandle != NULL && (millis() - startWait < 2000)) {
				vTaskDelay(pdMS_TO_TICKS(50));
			}
		}
		Log_Println("shutdown webserver..", LOGLEVEL_NOTICE);
		wServer.end();
		webserverStarted = false;
	}
}
// handle not found
void notFound(AsyncWebServerRequest *request) {
	Log_Printf(LOGLEVEL_ERROR, "%s not found, redirect to startpage", request->url().c_str());
	String html = "<!DOCTYPE html>Ooups - page \"" + request->url() + "\" not found (404)";
	html += "<script>async function tryRedirect() {try {var url = \"/\";const response = await fetch(url);window.location.href = url;} catch (error) {console.log(error);setTimeout(tryRedirect, 2000);}}tryRedirect();</script>";
	// for captive portal, send statuscode 200 & auto redirect to startpage
	request->send(200, "text/html", html);
}

void webserverStart(void) {
	if (!webserverStarted && (Wlan_IsConnected() || (WiFi.getMode() == WIFI_AP))) {
		// attach AsyncWebSocket for Mgmt-Interface
		ws.onEvent(onWebsocketEvent);
		wServer.addHandler(&ws);

		// attach AsyncEventSource
		wServer.addHandler(&events);

		// Default
		wServer.on("/", HTTP_GET, [](AsyncWebServerRequest *request) {
			AsyncWebServerResponse *response;

			// ETag is tied to the firmware build (gitRevShort), so it must only gate the firmware-embedded
			// management_html_BIN response below - never the user-provided SD-card index.htm, whose content
			// can change independently of the firmware (a stale 304 would then serve an outdated cached
			// copy of the user's own custom page).
			const bool etag = request->hasHeader("If-None-Match") && request->getHeader("If-None-Match")->value().equals(gitRevShort);

			// management.html's frontend libraries are embedded rather than loaded from a CDN (see
			// html/vendor/), so it no longer *needs* internet access - but AP-mode is typically reached
			// through the OS's captive-portal mini-browser (e.g. iOS's Captive Network Assistant), which
			// is a constrained sandbox: fixed small viewport, often no/partial WebSocket support, and a
			// load-time budget the heavy Bootstrap/jQuery/jstree/WebSocket app can exceed - causing the OS
			// to report the connection attempt as failed. So AP-mode keeps serving the minimal,
			// framework-free accesspoint.html, which is known to work reliably in that sandbox.
			if (WiFi.getMode() == WIFI_STA) {
				// serve management.html in station-mode
#ifdef NO_SDCARD
				if (etag) {
					response = request->beginResponse(304);
				} else {
					response = request->beginResponse(200, "text/html", (const uint8_t *) management_html_BIN, sizeof(management_html_BIN));
					response->addHeader("Content-Encoding", "gzip");
					response->addHeader("Cache-Control", "no-cache");
					response->addHeader("ETag", gitRevShort);
				}
#else
				if (gFSystem.exists("/.html/index.htm")) {
					response = request->beginResponse(gFSystem, "/.html/index.htm", "text/html", false);
				} else if (etag) {
					response = request->beginResponse(304);
				} else {
					response = request->beginResponse(200, "text/html", (const uint8_t *) management_html_BIN, sizeof(management_html_BIN));
					response->addHeader("Content-Encoding", "gzip");
					response->addHeader("Cache-Control", "no-cache");
					response->addHeader("ETag", gitRevShort);
				}
#endif
			} else {
				// serve accesspoint.html in AP-mode
				if (etag) {
					response = request->beginResponse(304);
				} else {
					response = request->beginResponse(200, "text/html", (const uint8_t *) accesspoint_html_BIN, sizeof(accesspoint_html_BIN));
					response->addHeader("Content-Encoding", "gzip");
					response->addHeader("Cache-Control", "no-cache");
					response->addHeader("ETag", gitRevShort);
				}
			}
			request->send(response);
		});

		WWWData::registerRoutes(serveProgmemFiles);

		// Log
		wServer.on("/log", HTTP_GET, [](AsyncWebServerRequest *request) {
			request->send(200, "text/plain; charset=utf-8", Log_GetRingBuffer());
			System_UpdateActivityTimer();
		});

		// info
		wServer.on("/info", HTTP_GET, handleGetInfo);

		// NVS-backup-upload
		wServer.on(
			"/upload", HTTP_POST, [](AsyncWebServerRequest *request) {
				request->send(200);
			},
			handleUpload);

		// OTA-upload
		wServer.on(
			"/update", HTTP_POST, [](AsyncWebServerRequest *request) {
#ifdef BOARD_HAS_16MB_FLASH_AND_OTA_SUPPORT
				if (Update.hasError()) {
					request->send(500, "text/plain", Update.errorString());
				} else {
					request->send(200, "text/html", restartWebsite);
				}
#else
				request->send(500, "text/html", otaNotSupportedWebsite);
#endif
			},
			[](AsyncWebServerRequest *request, String filename, size_t index, uint8_t *data, size_t len, bool final) {
#ifndef BOARD_HAS_16MB_FLASH_AND_OTA_SUPPORT
				Log_Println(otaNotSupported, LOGLEVEL_NOTICE);
				return;
#endif

				if (!index) {
					// pause some tasks to get more free CPU time for the upload
					System_PauseTasksDuringUpload(true);
					System_UpdateActivityTimer();
					Update.begin();
					Log_Println(fwStart, LOGLEVEL_NOTICE);
				}

				Update.write(data, len);
				Log_Print(".", LOGLEVEL_NOTICE, false);

				const size_t contentLength = request->contentLength();
				if (contentLength > 0) {
					Led_ShowOtaProgress((uint8_t) (((index + len) * 100) / contentLength));
				}

				if (final) {
					Update.end(true);
					// resume the paused tasks
					System_PauseTasksDuringUpload(false);
					Log_Println(fwEnd, LOGLEVEL_NOTICE);
					if (Update.hasError()) {
						Log_Println(Update.errorString(), LOGLEVEL_ERROR);
					}
					Serial.flush();
					// ESP.restart(); // restart is done via webpage javascript
				}
			});

		// ESP-restart
		wServer.on("/restart", HTTP_POST, [](AsyncWebServerRequest *request) {
			request->send(200, "text/html", restartWebsite);
			System_Restart();
		});

		// ESP-shutdown
		wServer.on("/shutdown", HTTP_POST, [](AsyncWebServerRequest *request) {
			request->send(200, "text/html", shutdownWebsite);
			System_RequestSleep();
		});

#ifdef CONFIG_FREERTOS_USE_TRACE_FACILITY
		// runtime task statistics
		wServer.on("/stats", HTTP_GET, [](AsyncWebServerRequest *request) {
			AsyncResponseStream *response = request->beginResponseStream("text/html");
			response->println("<!DOCTYPE html><html><head> <meta charset='utf-8'><title>ESPuino runtime stats</title>");
			response->println("<meta http-equiv='refresh' content='2'>"); // refresh page every 2 seconds
			response->print("</head><body>");
			// show memory usage
			response->println("Memory:<div class='text'><pre>");
			response->println("Free heap:           " + String(ESP.getFreeHeap()));
			response->println("Largest free block:  " + String(ESP.getMaxAllocHeap()));
			response->println("DMA free:            " + String(heap_caps_get_free_size(MALLOC_CAP_DMA)));
			response->println("DMA largest:         " + String(heap_caps_get_largest_free_block(MALLOC_CAP_DMA)));
			response->println("Free PSRAM heap:     " + String(ESP.getFreePsram()));
			response->println("Largest PSRAM block: " + String(ESP.getMaxAllocPsram()));
			response->println("</pre></div><br>");

			uint32_t taskCount = uxTaskGetNumberOfTasks();
			size_t bufferSize = (taskCount + 10) * 80; // Provide safer margin for vTaskList
			char *pbuffer = (char *) x_calloc(bufferSize, 1);
			if (pbuffer) {
				// show tasklist
				response->println("Tasklist:<div class='text'><pre>");
				response->println("Taskname\tState\tPrio\tStack\tNum\tCore");
				vTaskList(pbuffer);
				response->println(pbuffer);
				response->println("</pre></div><br><br>Runtime statistics:<div class='text'><pre>");
				response->println("Taskname\tRuntime\tPercentage");
				vTaskGetRunTimeStats(pbuffer);
				response->println(pbuffer);
				free(pbuffer);
			}
			response->println("</pre></div></body></html>");
			// send the response last
			request->send(response);
		});
#endif
		// debug info
		wServer.on("/debug", HTTP_GET, handleDebugRequest);

		// erase all RFID-assignments from NVS
		wServer.on("/rfidnvserase", HTTP_POST, [](AsyncWebServerRequest *request) {
			Log_Println(eraseRfidNvs, LOGLEVEL_NOTICE);
			// make a backup first
			Web_DumpNvsToSd("rfidTags", backupFile);
			if (gPrefsRfid.clear()) {
				Rfid_ResetLastTag(); // Every tag means something else now (namely: nothing)
				request->send(200);
			} else {
				request->send(500);
			}
			System_UpdateActivityTimer();
		});

		// RFID
		wServer.on("/rfid", HTTP_GET, handleGetRFIDRequest);
		wServer.addRewrite(new OneParamRewrite("/rfid/ids-only", "/rfid?ids-only=true"));
		wServer.addHandler(new AsyncCallbackJsonWebHandler("/rfid", handlePostRFIDRequest));
		wServer.addRewrite(new OneParamRewrite("/rfid/{id}", "/rfid?id={id}"));
		wServer.on("/rfid", HTTP_DELETE, handleDeleteRFIDRequest);

		// MediaHub registered servers (concept §5.1)
		wServer.on("/mediahubservers", HTTP_GET, handleGetMediaHubServers);
		wServer.addHandler(new AsyncCallbackJsonWebHandler("/mediahubservers", handlePostMediaHubServers));
		wServer.addRewrite(new OneParamRewrite("/mediahubservers/{name}", "/mediahubservers?name={name}"));
		wServer.on("/mediahubservers", HTTP_DELETE, handleDeleteMediaHubServers);

		// WiFi scan
		wServer.on("/wifiscan", HTTP_GET, handleWiFiScanRequest);

		// Fileexplorer (realtime)
		wServer.on("/explorer", HTTP_GET, explorerHandleListRequest);

		wServer.on(
			"/explorer", HTTP_POST, [](AsyncWebServerRequest *request) {
				// clean up buffers
				request->onDisconnect([]() { destroyDoubleBuffer(); });
				// we are finished with the upload
				if (!request->_tempObject) {
					request->send(200);
				}
			},
			NULL, explorerHandleFileUpload);

		wServer.on("/explorerdownload", HTTP_GET, explorerHandleDownloadRequest);

		wServer.on("/explorer", HTTP_DELETE, explorerHandleDeleteRequest);

		wServer.on("/explorer", HTTP_PUT, explorerHandleCreateRequest);

		wServer.on("/explorer", HTTP_PATCH, explorerHandleRenameRequest);

		wServer.on("/exploreraudio", HTTP_POST, explorerHandleAudioRequest);

		wServer.on("/trackprogress", HTTP_GET, handleTrackProgressRequest);

		wServer.on("/savedSSIDs", HTTP_GET, handleGetSavedSSIDs);
		wServer.addHandler(new AsyncCallbackJsonWebHandler("/savedSSIDs", handlePostSavedSSIDs));

		wServer.addRewrite(new OneParamRewrite("/savedSSIDs/{ssid}", "/savedSSIDs?ssid={ssid}"));
		wServer.on("/savedSSIDs", HTTP_DELETE, handleDeleteSavedSSIDs);
		wServer.on("/activeSSID", HTTP_GET, handleGetActiveSSID);
		wServer.on("/wifistatus", HTTP_GET, handleGetWifiStatus);
		wServer.addHandler(new AsyncCallbackJsonWebHandler("/wifitest", handlePostWifiTest));

		wServer.on("/wificonfig", HTTP_GET, handleGetWiFiConfig);
		wServer.addHandler(new AsyncCallbackJsonWebHandler("/wificonfig", handlePostWiFiConfig));

		// current cover image
		wServer.on("/cover", HTTP_GET, handleCoverImageRequest);

		// Bluetooth-Scan and connect
		wServer.on("/bluetoothscan", HTTP_GET, handleBluetoothScanRequest);
		wServer.on("/bluetoothresults", HTTP_GET, handleBluetoothResultsRequest);
		wServer.on("/bluetoothstatus", HTTP_GET, handleBluetoothStatusRequest);
		wServer.addHandler(new AsyncCallbackJsonWebHandler("/bluetoothconnect", handleBluetoothConnectRequest));

		// ESPuino logo: user-provided SD override takes precedence, otherwise fall back to the default
		// logo embedded in the firmware (previously an external redirect to espuino.de, which failed
		// without internet access, e.g. in AP-mode).
		wServer.on("/logo", HTTP_GET, [](AsyncWebServerRequest *request) {
#ifndef NO_SDCARD
			Log_Println("logo request", LOGLEVEL_DEBUG);
			if (gFSystem.exists("/.html/logo.png")) {
				request->send(gFSystem, "/.html/logo.png", "image/png");
				return;
			};
			if (gFSystem.exists("/.html/logo.svg")) {
				request->send(gFSystem, "/.html/logo.svg", "image/svg+xml");
				return;
			};
#endif
			AsyncWebServerResponse *response;
			if (request->hasHeader("If-None-Match") && request->getHeader("If-None-Match")->value().equals(gitRevShort)) {
				response = request->beginResponse(304);
			} else {
				response = request->beginResponse(200, "image/webp", (const uint8_t *) vendor_branding_logo_webp_BIN, sizeof(vendor_branding_logo_webp_BIN));
				response->addHeader("Content-Encoding", "gzip");
				response->addHeader("Cache-Control", "no-cache");
				response->addHeader("ETag", gitRevShort);
			}
			request->send(response);
		});
		// ESPuino favicon: same SD-override-then-embedded-default pattern as /logo above.
		wServer.on("/favicon.ico", HTTP_GET, [](AsyncWebServerRequest *request) {
#ifndef NO_SDCARD
			if (gFSystem.exists("/.html/favicon.ico")) {
				request->send(gFSystem, "/.html/favicon.ico", "image/x-icon");
				return;
			};
#endif
			AsyncWebServerResponse *response;
			if (request->hasHeader("If-None-Match") && request->getHeader("If-None-Match")->value().equals(gitRevShort)) {
				response = request->beginResponse(304);
			} else {
				response = request->beginResponse(200, "image/x-icon", (const uint8_t *) vendor_branding_favicon_ico_BIN, sizeof(vendor_branding_favicon_ico_BIN));
				response->addHeader("Content-Encoding", "gzip");
				response->addHeader("Cache-Control", "no-cache");
				response->addHeader("ETag", gitRevShort);
			}
			request->send(response);
		});
		// ESPuino settings
		wServer.on("/settings", HTTP_GET, handleGetSettings);
		wServer.addHandler(new AsyncCallbackJsonWebHandler("/settings", handlePostSettings));
		// operation mode
		wServer.on("/mode", HTTP_GET, handleGetOperationMode);
		wServer.addHandler(new AsyncCallbackJsonWebHandler("/mode", handlePostOperationMode));
		// Init HallEffectSensor Value
#ifdef HALLEFFECT_SENSOR_ENABLE
		wServer.on("/inithalleffectsensor", HTTP_GET, [](AsyncWebServerRequest *request) {
			bool bres = gHallEffectSensor.saveActualFieldValue2NVS();
			char buffer[128];
			snprintf(buffer, sizeof(buffer), "WebRequest>HallEffectSensor FieldValue: %d => NVS, Status: %s", gHallEffectSensor.NullFieldValue(), bres ? "OK" : "ERROR");
			Log_Println(buffer, LOGLEVEL_INFO);
			request->send(200, "text/html", buffer);
		});
#endif

		wServer.onNotFound(notFound);

		// allow cors for local debug (https://github.com/me-no-dev/ESPAsyncWebServer/issues/1080)
		DefaultHeaders::Instance().addHeader("Access-Control-Allow-Headers", "Accept, Content-Type, Authorization");
		DefaultHeaders::Instance().addHeader("Access-Control-Allow-Credentials", "true");
		DefaultHeaders::Instance().addHeader("Access-Control-Allow-Origin", "*");
		wServer.begin();
		webserverStarted = true;
		Log_Println(httpReady, LOGLEVEL_NOTICE);
		// start a first WiFi scan (to get a WiFi list more quickly in webview)
		WiFi.scanNetworks(true, false, true, 120);
	}
}

unsigned long lastPongTimestamp;

// process JSON to settings
WebsocketCodeType JSONToSettings(JsonObject doc) {
	if (!doc) {
		Log_Println("JSONToSettings: doc unassigned", LOGLEVEL_DEBUG);
		return WebsocketCodeType::Error;
	}
	if (doc["general"].is<JsonObject>()) {
		// general settings
		JsonObject generalObj = doc["general"];
		// A minimum volume that is not strictly below both maximums would leave no usable volume range,
		// so reject it before writing anything. The HTML input already constrains this, but a direct
		// REST/websocket POST could bypass that.
		const uint8_t minVolume = generalObj["minVolume"].as<uint8_t>();
		const uint8_t maxVolumeSp = generalObj["maxVolumeSp"].as<uint8_t>();
		const uint8_t maxVolumeHp = generalObj["maxVolumeHp"].as<uint8_t>();
		if (minVolume >= maxVolumeSp || minVolume >= maxVolumeHp) {
			Log_Println(webSaveSettingsVolumeMinMaxError, LOGLEVEL_ERROR);
			return WebsocketCodeType::Error;
		}
		bool success = (gPrefsSettings.putUInt("initVolume", generalObj["initVolume"].as<uint8_t>()) != 0);
		success = success && (gPrefsSettings.putUInt("minVolume", minVolume) != 0);
		success = success && (gPrefsSettings.putUInt("maxVolumeSp", maxVolumeSp) != 0);
		success = success && (gPrefsSettings.putUInt("maxVolumeHp", maxVolumeHp) != 0);
		success = success && (gPrefsSettings.putUInt("mInactiviyT", generalObj["sleepInactivity"].as<uint8_t>()) != 0);
		if (generalObj["rotSeekStep"].is<uint8_t>()) {
			success = success && (gPrefsSettings.putUChar("rotSeekStep", generalObj["rotSeekStep"].as<uint8_t>()) != 0);
		}
		if (generalObj["jumpOffset"].is<uint8_t>()) {
			success = success && (gPrefsSettings.putUChar("jumpOffset", generalObj["jumpOffset"].as<uint8_t>()) != 0);
		}
		success = success && (gPrefsSettings.putBool("playMono", generalObj["playMono"].as<bool>()) != 0);
		success = success && (gPrefsSettings.putBool("savePosShutdown", generalObj["savePosShutdown"].as<bool>()) != 0);
		success = success && (gPrefsSettings.putBool("savePosRfidChge", generalObj["savePosRfidChge"].as<bool>()) != 0);
		if (generalObj["savePosInterval"].is<uint16_t>()) {
			// Guard: an older cached GUI page POSTs this block without the field; without this guard
			// putUShort would persist a 0 and silently disable a checkpoint interval the user had set.
			success = success && (gPrefsSettings.putUShort("savePosIntv", generalObj["savePosInterval"].as<uint16_t>()) != 0);
			gPlayProperties.savePosIntervalSecs = generalObj["savePosInterval"].as<uint16_t>(); // apply live, no reboot needed
		}
		success = success && (gPrefsSettings.putBool("playLastOnBoot", generalObj["playLastRfidOnReboot"].as<bool>()) != 0);
		success = success && (gPrefsSettings.putBool("pauseRfidRem", generalObj["pauseIfRfidRemoved"].as<bool>()) != 0);
		success = success && (gPrefsSettings.putBool("dAccRfidTwice", generalObj["dontAcceptRfidTwice"].as<bool>()) != 0);
		success = success && (gPrefsSettings.putBool("p2pSameRfid", generalObj["resumeOnSameRfid"].as<bool>()) != 0);
		success = success && (gPrefsSettings.putBool("pauseOnMinVol", generalObj["pauseOnMinVol"].as<bool>()) != 0);
		success = success && (gPrefsSettings.putBool("nightVolLimit", generalObj["nightVolLimit"].as<bool>()) != 0);
		success = success && (gPrefsSettings.putBool("recoverVolBoot", generalObj["recoverVolBoot"].as<bool>()) != 0);
		success = success && (gPrefsSettings.putUChar("volumeCurve", generalObj["volumeCurve"].as<uint8_t>()) != 0);
		success = success && (gPrefsRfid.putUChar("rfidReaderType", generalObj["rfidReaderType"].as<uint8_t>()) != 0);
		success = success && (gPrefsRfid.putBool("pn5180Lpcd", generalObj["pn5180Lpcd"].as<bool>()) != 0);
		success = success && (gPrefsRfid.putUChar("mfrc522Gain", generalObj["mfrc522Gain"].as<uint8_t>()) != 0);
		success = success && (gPrefsRfid.putUShort("rfidScanIntv", generalObj["mfrc522ScanInterval"].as<uint16_t>()) != 0);
		success = success && (gPrefsRfid.putUShort("pn5180Debounce", generalObj["pn5180Debounce"].as<uint16_t>()) != 0);

		// Keep compatibility with older cached management pages: if the field is missing,
		// preserve the password already stored in NVS instead of overwriting it.
		String slixPrivacyPassword = generalObj["slixPrivacyPassword"].as<String>();
		if (slixPrivacyPassword.length() > 0) {
			SlixPrivacyPassword slixPassword = {};
			bool validPassword = (slixPrivacyPassword.length() == slixPassword.size() * 2);
			for (size_t i = 0; validPassword && i < slixPassword.size(); i++) {
				auto hexNibble = [](char c) -> int8_t {
					if ((c >= '0') && (c <= '9')) {
						return c - '0';
					}
					if ((c >= 'A') && (c <= 'F')) {
						return c - 'A' + 10;
					}
					if ((c >= 'a') && (c <= 'f')) {
						return c - 'a' + 10;
					}
					return -1;
				};
				const int8_t high = hexNibble(slixPrivacyPassword[i * 2]);
				const int8_t low = hexNibble(slixPrivacyPassword[i * 2 + 1]);
				if ((high < 0) || (low < 0)) {
					validPassword = false;
				} else {
					slixPassword[i] = static_cast<uint8_t>((high << 4) | low);
				}
			}
			if (validPassword) {
				const bool passwordStored = success && (gPrefsRfid.putBytes(SLIX_PRIVACY_PASSWORD_NVS_KEY, slixPassword.data(), slixPassword.size()) == slixPassword.size());
				success = passwordStored;
				if (passwordStored) {
					RfidPn5180_SetSlixPrivacyPassword(slixPassword);
				}
			} else {
				success = false;
				Log_Println("Invalid ICODE-SLIX2 privacy password in web settings", LOGLEVEL_ERROR);
			}
		}
		if (!success) {
			Log_Printf(LOGLEVEL_ERROR, webSaveSettingsError, "general");
			return WebsocketCodeType::Error;
		}

		// Apply the new maximum-volume limits immediately; no reboot is required.
		AudioPlayer_ApplyMaxVolumes(maxVolumeSp, maxVolumeHp);
		// Takes effect the next time night mode is switched on; an already running night mode keeps the
		// ceiling it was armed with (or none), so the setting never changes the limit under way.
		AudioPlayer_SetNightVolumeLimitEnabled(generalObj["nightVolLimit"].as<bool>());

		gPlayProperties.newPlayMono = generalObj["playMono"].as<bool>();
		gPlayProperties.SavePlayPosRfidChange = generalObj["savePosRfidChge"].as<bool>();
		gPlayProperties.pauseOnMinVolume = generalObj["pauseOnMinVol"].as<bool>();
		gPlayProperties.pauseIfRfidRemoved = generalObj["pauseIfRfidRemoved"].as<bool>();
		gPlayProperties.resumeOnSameRfid = generalObj["resumeOnSameRfid"].as<bool>();
		if (gPlayProperties.pauseIfRfidRemoved) {
			// ignore feature silently if pauseIfRfidRemoved is active
			Log_Println("pauseIfRfidRemoved is enabled -> deactivate dontAcceptRfidTwice", LOGLEVEL_NOTICE);
			gPlayProperties.dontAcceptRfidTwice = false;
		} else {
			gPlayProperties.dontAcceptRfidTwice = generalObj["dontAcceptRfidTwice"].as<bool>();
		}
	}
	if (doc["equalizer"].is<JsonObject>()) {
		int8_t _gainLowPass = doc["equalizer"]["gainLowPass"].as<int8_t>();
		int8_t _gainBandPass = doc["equalizer"]["gainBandPass"].as<int8_t>();
		int8_t _gainHighPass = doc["equalizer"]["gainHighPass"].as<int8_t>();
		// equalizer settings
		if (
			gPrefsSettings.putChar("gainLowPass", _gainLowPass) == 0 || gPrefsSettings.putChar("gainBandPass", _gainBandPass) == 0 || gPrefsSettings.putChar("gainHighPass", _gainHighPass) == 0) {
			Log_Printf(LOGLEVEL_ERROR, webSaveSettingsError, "equalizer");
			return WebsocketCodeType::Error;
		} else {
			AudioPlayer_SetEqualizer(_gainLowPass, _gainBandPass, _gainHighPass);
		}
	}
	if (doc["wifi"].is<JsonObject>()) {
		// WiFi settings
		String hostName = doc["wifi"]["hostname"];
		if (!Wlan_ValidateHostname(hostName)) {
			Log_Println("Invalid hostname", LOGLEVEL_ERROR);
			return WebsocketCodeType::Error;
		}
		if (((!Wlan_SetHostname(hostName)) || gPrefsSettings.putBool("ScanWiFiOnStart", doc["wifi"]["scanOnStart"].as<bool>()) == 0)) {
			Log_Printf(LOGLEVEL_ERROR, webSaveSettingsError, "wifi");
			return WebsocketCodeType::Error;
		}
	}
	if (doc["led"].is<JsonObject>()) {
		// Neopixel settings
		JsonObject ledObj = doc["led"];
		if (ledObj["dimStates"].as<uint8_t>() == 0) {
			// used as a divisor throughout Led.cpp's animations - a stored 0 would only surface as a
			// crash on the next boot (Led_Init() self-heals it, but only then), so reject it here instead.
			Log_Println("Invalid dimStates (must not be 0)", LOGLEVEL_ERROR);
			return WebsocketCodeType::Error;
		}
		bool success = (gPrefsSettings.putUChar("iLedBrightness", ledObj["initBrightness"].as<uint8_t>()) != 0);
		success = success && (gPrefsSettings.putUChar("nLedBrightness", ledObj["nightBrightness"].as<uint8_t>()) != 0);
		success = success && (gPrefsSettings.putUChar("aLedBrightness", ledObj["atmoBrightness"].as<uint8_t>()) != 0);
		success = success && (gPrefsSettings.putUChar("numIndicator", ledObj["numIndicator"].as<uint8_t>()) != 0);
		success = success && (gPrefsSettings.putUChar("numControl", ledObj["numControl"].as<uint8_t>()) != 0);
		success = success && (gPrefsSettings.putUChar("numIdleDots", ledObj["numIdleDots"].as<uint8_t>()) != 0);
		success = success && (gPrefsSettings.putBool("offsetPause", ledObj["offsetPause"].as<bool>()) != 0);
		success = success && (gPrefsSettings.putBool("ledRfidFlash", ledObj["rfidFlash"].as<bool>()) != 0);
		success = success && (gPrefsSettings.putShort("hueStart", ledObj["hueStart"].as<int16_t>()) != 0);
		success = success && (gPrefsSettings.putShort("hueEnd", ledObj["hueEnd"].as<int16_t>()) != 0);
		success = success && (gPrefsSettings.putShort("hueAtmo", ledObj["hueAtmo"].as<int16_t>()) != 0);
		success = success && (gPrefsSettings.putShort("satAtmo", ledObj["satAtmo"].as<int16_t>()) != 0);
		success = success && (gPrefsSettings.putUChar("dimStates", ledObj["dimStates"].as<uint8_t>()) != 0);
		success = success && (gPrefsSettings.putBool("ledReverseRot", ledObj["reverseRot"].as<bool>()) != 0);
		success = success && (gPrefsSettings.putUChar("ledOffset", ledObj["offsetStart"].as<uint8_t>()) != 0);

		if (!success) {
			Log_Printf(LOGLEVEL_ERROR, webSaveSettingsError, "led");
			return WebsocketCodeType::Error;
		}
		// write led control color array to NVS.
		JsonArray colorArr = ledObj["controlColors"].as<JsonArray>();
		if (colorArr.size() == 0) {
			if (gPrefsSettings.isKey("controlColors")) {
				gPrefsSettings.remove("controlColors");
			}
			gPrefsSettings.putUChar("numControl", 0);
		} else {
			std::vector<uint32_t> controlLedColors;
			for (uint8_t controlLed = 0; controlLed < colorArr.size(); controlLed++) {
				controlLedColors.push_back(colorArr[controlLed].as<uint32_t>());
			}
			gPrefsSettings.putBytes("controlColors", controlLedColors.data(), controlLedColors.size() * sizeof(uint32_t));
		}
		Led_Init();
	}
	if (doc["buttons"].is<JsonObject>()) {
		// buttons
		JsonObject buttonsObj = doc["buttons"];
		bool success = (gPrefsSettings.putUChar("btnShort0", buttonsObj["short0"].as<uint8_t>()) != 0);
		success = success && (gPrefsSettings.putUChar("btnShort1", buttonsObj["short1"].as<uint8_t>()) != 0);
		success = success && (gPrefsSettings.putUChar("btnShort2", buttonsObj["short2"].as<uint8_t>()) != 0);
		success = success && (gPrefsSettings.putUChar("btnShort3", buttonsObj["short3"].as<uint8_t>()) != 0);
		success = success && (gPrefsSettings.putUChar("btnShort4", buttonsObj["short4"].as<uint8_t>()) != 0);
		success = success && (gPrefsSettings.putUChar("btnShort5", buttonsObj["short5"].as<uint8_t>()) != 0);
		success = success && (gPrefsSettings.putUChar("btnLong0", buttonsObj["long0"].as<uint8_t>()) != 0);
		success = success && (gPrefsSettings.putUChar("btnLong1", buttonsObj["long1"].as<uint8_t>()) != 0);
		success = success && (gPrefsSettings.putUChar("btnLong2", buttonsObj["long2"].as<uint8_t>()) != 0);
		success = success && (gPrefsSettings.putUChar("btnLong3", buttonsObj["long3"].as<uint8_t>()) != 0);
		success = success && (gPrefsSettings.putUChar("btnLong4", buttonsObj["long4"].as<uint8_t>()) != 0);
		success = success && (gPrefsSettings.putUChar("btnLong5", buttonsObj["long5"].as<uint8_t>()) != 0);
		for (uint8_t i = 0; i < 6; i++) { // "hold button + turn encoder" gestures
			char keyCw[12], keyCcw[13], jsonCw[10], jsonCcw[11];
			snprintf(keyCw, sizeof(keyCw), "btnRotCw%u", i);
			snprintf(keyCcw, sizeof(keyCcw), "btnRotCcw%u", i);
			snprintf(jsonCw, sizeof(jsonCw), "rotCw%u", i);
			snprintf(jsonCcw, sizeof(jsonCcw), "rotCcw%u", i);
			if (buttonsObj[jsonCw].is<uint8_t>()) {
				success = success && (gPrefsSettings.putUChar(keyCw, buttonsObj[jsonCw].as<uint8_t>()) != 0);
			}
			if (buttonsObj[jsonCcw].is<uint8_t>()) {
				success = success && (gPrefsSettings.putUChar(keyCcw, buttonsObj[jsonCcw].as<uint8_t>()) != 0);
			}
		}
		success = success && (gPrefsSettings.putUChar("btnMulti01", buttonsObj["multi01"].as<uint8_t>()) != 0);
		success = success && (gPrefsSettings.putUChar("btnMulti02", buttonsObj["multi02"].as<uint8_t>()) != 0);
		success = success && (gPrefsSettings.putUChar("btnMulti03", buttonsObj["multi03"].as<uint8_t>()) != 0);
		success = success && (gPrefsSettings.putUChar("btnMulti04", buttonsObj["multi04"].as<uint8_t>()) != 0);
		success = success && (gPrefsSettings.putUChar("btnMulti05", buttonsObj["multi05"].as<uint8_t>()) != 0);
		success = success && (gPrefsSettings.putUChar("btnMulti12", buttonsObj["multi12"].as<uint8_t>()) != 0);
		success = success && (gPrefsSettings.putUChar("btnMulti13", buttonsObj["multi13"].as<uint8_t>()) != 0);
		success = success && (gPrefsSettings.putUChar("btnMulti14", buttonsObj["multi14"].as<uint8_t>()) != 0);
		success = success && (gPrefsSettings.putUChar("btnMulti15", buttonsObj["multi15"].as<uint8_t>()) != 0);
		success = success && (gPrefsSettings.putUChar("btnMulti23", buttonsObj["multi23"].as<uint8_t>()) != 0);
		success = success && (gPrefsSettings.putUChar("btnMulti24", buttonsObj["multi24"].as<uint8_t>()) != 0);
		success = success && (gPrefsSettings.putUChar("btnMulti25", buttonsObj["multi25"].as<uint8_t>()) != 0);
		success = success && (gPrefsSettings.putUChar("btnMulti34", buttonsObj["multi34"].as<uint8_t>()) != 0);
		success = success && (gPrefsSettings.putUChar("btnMulti35", buttonsObj["multi35"].as<uint8_t>()) != 0);
		success = success && (gPrefsSettings.putUChar("btnMulti45", buttonsObj["multi45"].as<uint8_t>()) != 0);

		if (!success) {
			Log_Printf(LOGLEVEL_ERROR, webSaveSettingsError, "buttons");
			return WebsocketCodeType::Error;
		}
	}
	if (doc["rotary"].is<JsonObject>()) {
		// Rotary encoder
		if (gPrefsSettings.putBool("rotaryReverse", doc["rotary"]["reverse"].as<bool>()) == 0) {
			Log_Printf(LOGLEVEL_ERROR, webSaveSettingsError, "rotary");
			return WebsocketCodeType::Error;
		}
		// CMD_SEEK_PREVIEW tuning: guarded (not hard-erroring like "reverse" above) so an older cached
		// web-UI page that doesn't send these yet can't blank an already-saved value.
		if (doc["rotary"]["seekPrevDelay"].is<uint16_t>()) {
			gPrefsSettings.putUShort("seekPrevDelay", doc["rotary"]["seekPrevDelay"].as<uint16_t>());
		}
		if (doc["rotary"]["seekPrevSweep"].is<uint8_t>()) {
			uint8_t seekPrevSweep = doc["rotary"]["seekPrevSweep"].as<uint8_t>();
			if (seekPrevSweep < 1) {
				seekPrevSweep = 1; // must be >= 1 to avoid divide-by-zero in seek-preview
			}
			gPrefsSettings.putUChar("seekPrevSweep", seekPrevSweep);
		}
		RotaryEncoder_Init();
	}
	if (doc["battery"].is<JsonObject>()) {
		// Battery settings
		if (gPrefsSettings.putFloat("wLowVoltage", doc["battery"]["warnLowVoltage"].as<float>()) == 0 || gPrefsSettings.putFloat("vIndicatorLow", doc["battery"]["indicatorLow"].as<float>()) == 0 || gPrefsSettings.putFloat("vIndicatorHigh", doc["battery"]["indicatorHi"].as<float>()) == 0 || gPrefsSettings.putFloat("wCritVoltage", doc["battery"]["criticalVoltage"].as<float>()) == 0 || gPrefsSettings.putFloat("offsetVoltage", doc["battery"]["offsetVoltage"].as<float>()) == 0 || gPrefsSettings.putBool("shutdownBatCrit", doc["battery"]["shutdownOnCritical"].as<bool>()) == 0 || gPrefsSettings.putUInt("vCheckIntv", doc["battery"]["voltageCheckInterval"].as<uint8_t>()) == 0) {
			Log_Printf(LOGLEVEL_ERROR, webSaveSettingsError, "battery");
			return WebsocketCodeType::Error;
		}
		// Kept out of the "== 0 means failure" chain above: putString() returns strlen(), so clearing the
		// path to "" would be misread as an error even though the write succeeded.
		gPrefsSettings.putBool("batWarnSound", doc["battery"]["warnSound"].as<bool>());
		gPrefsSettings.putBool("batWarnOnce", doc["battery"]["warnSoundOnce"].as<bool>());
		const char *warnSoundFile = doc["battery"]["warnSoundFile"].as<const char *>();
		gPrefsSettings.putString("batWarnFile", warnSoundFile ? warnSoundFile : "");
		Battery_Init();
	}
	if (doc["playlist"].is<JsonObject>()) {
		// playlist settings
		if (!AudioPlayer_SetPlaylistSortMode(doc["playlist"]["sortMode"].as<uint8_t>())) {
			Log_Printf(LOGLEVEL_ERROR, webSaveSettingsError, "playlist");
			return WebsocketCodeType::Error;
		}
		if (!SdCard_SetMaxRecursionDepth(doc["playlist"]["recDepth"].as<uint8_t>())) {
			Log_Printf(LOGLEVEL_ERROR, webSaveSettingsError, "playlist");
			return WebsocketCodeType::Error;
		}
	}
	if (doc["ftp"].is<JsonObject>()) {
		const char *_ftpUser = doc["ftp"]["username"];
		const char *_ftpPwd = doc["ftp"]["password"];

		gPrefsSettings.putString("ftpuser", (String) _ftpUser);
		gPrefsSettings.putString("ftppassword", (String) _ftpPwd);
		// Check if settings were written successfully
		if (!(String(_ftpUser).equals(gPrefsSettings.getString("ftpuser", "-1")) || String(_ftpPwd).equals(gPrefsSettings.getString("ftppassword", "-1")))) {
			Log_Printf(LOGLEVEL_ERROR, webSaveSettingsError, "ftp");
			return WebsocketCodeType::Error;
		}
	} else if (doc["ftpStatus"].is<JsonObject>()) {
		uint8_t _ftpStart = doc["ftpStatus"]["start"].as<uint8_t>();
		if (_ftpStart == 1) { // ifdef FTP_ENABLE is checked in Ftp_EnableServer()
			Ftp_EnableServer();
		}
	}
	if (doc["mqtt"].is<JsonObject>()) {
		uint8_t _mqttEnable = doc["mqtt"]["enable"].as<uint8_t>();
		const char *_mqttClientId = doc["mqtt"]["clientID"];
		const char *_mqttDeviceId = doc["mqtt"]["deviceId"];
		const char *_mqttBaseTopic = doc["mqtt"]["baseTopic"];
		const char *_mqttServer = doc["mqtt"]["server"];
		const char *_mqttUser = doc["mqtt"]["username"];
		const char *_mqttPwd = doc["mqtt"]["password"];
		uint16_t _mqttPort = doc["mqtt"]["port"].as<uint16_t>();

		// Sanitize and validate inputs
		String mqttClientIdStr = String(_mqttClientId);
		String mqttDeviceIdStr = String(_mqttDeviceId);
		String mqttBaseTopicStr = String(_mqttBaseTopic);

		// sanitize base topic (trim slashes and whitespace)
		mqttBaseTopicStr.trim();
		while (mqttBaseTopicStr.startsWith("/")) {
			mqttBaseTopicStr = mqttBaseTopicStr.substring(1);
		}
		while (mqttBaseTopicStr.endsWith("/")) {
			mqttBaseTopicStr = mqttBaseTopicStr.substring(0, mqttBaseTopicStr.length() - 1);
		}
		if (mqttBaseTopicStr.length() >= mqttBaseTopicLength) {
			Log_Printf(LOGLEVEL_ERROR, webSaveSettingsError, "mqtt.baseTopic too long");
			return WebsocketCodeType::Error;
		}

		// validate device id (must not be empty and must not contain '/')
		mqttDeviceIdStr.trim();
		if (mqttDeviceIdStr.length() == 0) {
			Log_Printf(LOGLEVEL_ERROR, webSaveSettingsError, "mqtt.deviceId empty");
			return WebsocketCodeType::Error;
		}
		if (mqttDeviceIdStr.indexOf('/') >= 0) {
			Log_Printf(LOGLEVEL_ERROR, webSaveSettingsError, "mqtt.deviceId contains invalid char '/'");
			return WebsocketCodeType::Error;
		}
		if (mqttDeviceIdStr.length() >= mqttDeviceIdLength) {
			Log_Printf(LOGLEVEL_ERROR, webSaveSettingsError, "mqtt.deviceId too long");
			return WebsocketCodeType::Error;
		}

		// store sanitized values
		gPrefsSettings.putUChar("enableMQTT", _mqttEnable);
		gPrefsSettings.putString("mqttClientId", mqttClientIdStr);
		gPrefsSettings.putString("mqttDeviceId", mqttDeviceIdStr);
		gPrefsSettings.putString("mqttBaseTopic", mqttBaseTopicStr);
		gPrefsSettings.putString("mqttServer", (String) _mqttServer);
		gPrefsSettings.putString("mqttUser", (String) _mqttUser);
		gPrefsSettings.putString("mqttPassword", (String) _mqttPwd);
		gPrefsSettings.putUInt("mqttPort", _mqttPort);

		// verify writes (include deviceId and baseTopic)
		if ((gPrefsSettings.getUChar("enableMQTT", 99) != _mqttEnable) || (!String(_mqttServer).equals(gPrefsSettings.getString("mqttServer", "-1"))) || (!mqttBaseTopicStr.equals(gPrefsSettings.getString("mqttBaseTopic", "-1"))) || (!mqttDeviceIdStr.equals(gPrefsSettings.getString("mqttDeviceId", "-1")))) {
			Log_Printf(LOGLEVEL_ERROR, webSaveSettingsError, "mqtt");
			return WebsocketCodeType::Error;
		}
	}
	if (doc["bluetooth"].is<JsonObject>()) {
		// bluetooth settings
		const char *_btDeviceName = doc["bluetooth"]["deviceName"];
		gPrefsSettings.putString("btDeviceName", (String) _btDeviceName);
		const char *btPinCode = doc["bluetooth"]["pinCode"];
		gPrefsSettings.putString("btPinCode", (String) btPinCode);
		// Check if settings were written successfully
		if (gPrefsSettings.getString("btDeviceName", "") != _btDeviceName || gPrefsSettings.getString("btPinCode", "") != btPinCode) {
			Log_Printf(LOGLEVEL_ERROR, webSaveSettingsError, "bluetooth");
			return WebsocketCodeType::Error;
		}
	} else if (doc["rfidMod"].is<JsonObject>()) {
		const char *_rfidIdModId = doc["rfidMod"]["rfidIdMod"];
		uint8_t _modId = doc["rfidMod"]["modId"];
		if (_modId <= 0) {
			gPrefsRfid.remove(_rfidIdModId);
		} else {
			char rfidString[12];
			snprintf(rfidString, sizeof(rfidString) / sizeof(rfidString[0]), "%s0%s0%s%u%s0", stringDelimiter, stringDelimiter, stringDelimiter, _modId, stringDelimiter);
			gPrefsRfid.putString(_rfidIdModId, rfidString);

			String s = gPrefsRfid.getString(_rfidIdModId, "-1");
			if (s.compareTo(rfidString)) {
				return WebsocketCodeType::Error;
			}
		}
		Rfid_ResetLastTag(); // The tag means something else now: make sure re-applying it is not deduped away
		Web_DumpNvsToSd("rfidTags", backupFile); // Store backup-file every time when a new rfid-tag is programmed
	} else if (doc["rfidAssign"].is<JsonObject>()) {
		const char *_rfidIdAssinId = doc["rfidAssign"]["rfidIdMusic"];
		const char *_fileOrUrlAscii = doc["rfidAssign"]["fileOrUrl"];
		uint8_t _playMode = doc["rfidAssign"]["playMode"];
		if (_playMode <= 0) {
			Log_Println("rfidAssign: Invalid playmode", LOGLEVEL_ERROR);
			return WebsocketCodeType::Error;
		}
		char rfidString[275];
		snprintf(rfidString, sizeof(rfidString) / sizeof(rfidString[0]), "%s%s%s0%s%u%s0", stringDelimiter, _fileOrUrlAscii, stringDelimiter, stringDelimiter, _playMode, stringDelimiter);
		gPrefsRfid.putString(_rfidIdAssinId, rfidString);
		Rfid_ResetLastTag(); // The tag means something else now: make sure re-applying it is not deduped away

		String s = gPrefsRfid.getString(_rfidIdAssinId, "-1");
		if (s.compareTo(rfidString)) {
			return WebsocketCodeType::Error;
		}
		Web_DumpNvsToSd("rfidTags", backupFile); // Store backup-file every time when a new rfid-tag is programmed
		Web_SendWebsocketData(0, WebsocketCodeType::Ok);
	} else if (doc["ping"].is<JsonObject>()) {
		if ((millis() - lastPongTimestamp) > 1000u) {
			// send pong (keep-alive heartbeat), check for excessive calls
			lastPongTimestamp = millis();
			Web_SendWebsocketData(0, WebsocketCodeType::Pong);
		}
		return WebsocketCodeType::Silent;
	} else if (doc["controls"].is<JsonObject>()) {
		// Prevent website control over volume and player actions in Bluetooth-Speaker mode
		// we could still allow sone special commands, but it's cleaner this way
		if (!System_IsWebControlAllowed()) {
			Log_Println(notAllowedInCurrentMode, LOGLEVEL_NOTICE);
			return WebsocketCodeType::NotAllowedInCurrentMode;
		}
		const JsonObject controlsObj = doc["controls"].as<JsonObject>();
		if (controlsObj["set_volume"].is<uint8_t>()) {
			uint8_t new_vol = controlsObj["set_volume"].as<uint8_t>();
			AudioPlayer_SetVolume(new_vol); // already broadcasts its own Volume update
			if (!controlsObj["action"].is<uint8_t>()) {
				// pure volume-slider drag (no button action alongside it) - don't also send
				// back an Ok ack, or dragging the slider spams a "success" toast per tick
				return WebsocketCodeType::Silent;
			}
		}
		if (controlsObj["action"].is<uint8_t>()) {
			uint8_t cmd = controlsObj["action"].as<uint8_t>();
			Cmd_Action(cmd);
		}
	} else if (doc["trackinfo"].is<JsonObject>()) {
		Web_SendWebsocketData(0, WebsocketCodeType::TrackInfo);
		return WebsocketCodeType::Silent;
	} else if (doc["coverimg"].is<JsonObject>()) {
		Web_SendWebsocketData(0, WebsocketCodeType::CoverImg);
		return WebsocketCodeType::Silent;
	} else if (doc["volume"].is<JsonObject>()) {
		Web_SendWebsocketData(0, WebsocketCodeType::Volume);
		return WebsocketCodeType::Silent;
	} else if (doc["settings"].is<JsonObject>()) {
		Web_SendWebsocketData(0, WebsocketCodeType::Settings);
		return WebsocketCodeType::Silent;
	} else if (doc["ssids"].is<JsonObject>()) {
		Web_SendWebsocketData(0, WebsocketCodeType::Ssid);
		return WebsocketCodeType::Silent;
	} else if (doc["trackProgress"].is<JsonObject>()) {
		// Prevent seeking in Bluetooth mode
		if (!System_IsWebControlAllowed()) {
			Log_Println(notAllowedInCurrentMode, LOGLEVEL_NOTICE);
			return WebsocketCodeType::NotAllowedInCurrentMode;
		}
		const JsonObject trackObj = doc["trackProgress"].as<JsonObject>();
		if (trackObj["posPercent"].is<uint8_t>()) {
			gPlayProperties.seekmode = SEEK_POS_PERCENT;
			gPlayProperties.currentRelPos = trackObj["posPercent"].as<uint8_t>();
		}
		Web_SendWebsocketData(0, WebsocketCodeType::TrackProgress);
		return WebsocketCodeType::Silent;
	}

	return WebsocketCodeType::Ok;
}

// process settings to JSON object
static void settingsToJSON(JsonObject obj, const String section) {
	if ((section == "") || (section == "current")) {
		// current values
		JsonObject curObj = obj["current"].to<JsonObject>();
		curObj["volume"].set(AudioPlayer_GetCurrentVolume());
		curObj["rfidTagId"] = String(gCurrentRfidTagId);
	}
	if ((section == "") || (section == "general")) {
		// general settings
		JsonObject generalObj = obj["general"].to<JsonObject>();
		generalObj["initVolume"].set(gPrefsSettings.getUInt("initVolume", 3));
		generalObj["minVolume"].set(gPrefsSettings.getUInt("minVolume", AUDIOPLAYER_VOLUME_MIN));
		generalObj["maxVolumeSp"].set(gPrefsSettings.getUInt("maxVolumeSp", 21));
		generalObj["maxVolumeHp"].set(gPrefsSettings.getUInt("maxVolumeHp", 21));
		generalObj["sleepInactivity"].set(gPrefsSettings.getUInt("mInactiviyT", 10));
		generalObj["rotSeekStep"].set(gPrefsSettings.getUChar("rotSeekStep", SEEK_STEP_ROTARY_DEFAULT)); // seconds per detent when seeking via a rotary gesture
		generalObj["jumpOffset"].set(gPrefsSettings.getUChar("jumpOffset", SEEK_STEP_BUTTON_DEFAULT)); // seconds to jump per button press when seeking
		generalObj["playMono"].set(gPrefsSettings.getBool("playMono", false));
		generalObj["savePosShutdown"].set(gPrefsSettings.getBool("savePosShutdown", false)); // SAVE_PLAYPOS_BEFORE_SHUTDOWN
		generalObj["savePosRfidChge"].set(gPrefsSettings.getBool("savePosRfidChge", false)); // SAVE_PLAYPOS_WHEN_RFID_CHANGE
		generalObj["savePosInterval"].set(gPrefsSettings.getUShort("savePosIntv", 0)); // SAVE_PLAYPOS_INTERVAL (periodic checkpoint seconds, 0 = off)
		generalObj["playLastRfidOnReboot"].set(gPrefsSettings.getBool("playLastOnBoot", false)); // PLAY_LAST_RFID_AFTER_REBOOT
		generalObj["pauseIfRfidRemoved"].set(gPrefsSettings.getBool("pauseRfidRem", false)); // PAUSE_WHEN_RFID_REMOVED
		generalObj["dontAcceptRfidTwice"].set(gPrefsSettings.getBool("dAccRfidTwice", false)); // DONT_ACCEPT_SAME_RFID_TWICE
		generalObj["resumeOnSameRfid"].set(gPrefsSettings.getBool("p2pSameRfid", false)); // RESUME_ON_SAME_RFID
		generalObj["rfidReaderType"].set(gPrefsRfid.getUChar("rfidReaderType", 0)); // RFID_READER_TYPE_RUNTIME
		generalObj["pn5180Lpcd"].set(gPrefsRfid.getBool("pn5180Lpcd", false)); // PN5180 LPCD
		generalObj["mfrc522Gain"].set(gPrefsRfid.getUChar("mfrc522Gain", 7)); // MFRC522_GAIN
		generalObj["mfrc522ScanInterval"].set(gPrefsRfid.getUShort("rfidScanIntv", 100)); // RFID_SCAN_INTERVAL
		generalObj["pn5180Debounce"].set(gPrefsRfid.getUShort("pn5180Debounce", 500)); // PN5180 debounce (ms)

		const String slixPasswordHex = slixPrivacyPasswordToHex(slixPrivacyPasswordFromPrefs());
		generalObj["slixPrivacyPassword"].set(slixPasswordHex);
		generalObj["pauseOnMinVol"].set(gPrefsSettings.getBool("pauseOnMinVol", false)); // PAUSE_ON_MIN_VOLUME
		generalObj["nightVolLimit"].set(gPrefsSettings.getBool("nightVolLimit", false)); // NIGHT_MODE_VOLUME_LIMIT
		generalObj["recoverVolBoot"].set(gPrefsSettings.getBool("recoverVolBoot", false)); // USE_LAST_VOLUME_AFTER_REBOOT
		generalObj["volumeCurve"].set(gPrefsSettings.getUChar("volumeCurve", 0)); // VOLUMECURVE
	}
	if (section == "rfidstatus") {
		JsonObject rfidStatusObj = obj["rfidStatus"].to<JsonObject>();
		uint8_t firmwareMajor = 0;
		uint8_t firmwareMinor = 0;
		if (RfidPn5180_GetFirmwareVersion(firmwareMajor, firmwareMinor)) {
			char firmwareVersion[8];
			snprintf(firmwareVersion, sizeof(firmwareVersion), "%u.%u", firmwareMajor, firmwareMinor);
			rfidStatusObj["pn5180Firmware"].set(firmwareVersion);
		} else {
			rfidStatusObj["pn5180Firmware"].set("");
		}
	}
	if ((section == "") || (section == "equalizer")) {
		// equalizer settings
		JsonObject equalizerObj = obj["equalizer"].to<JsonObject>();
		equalizerObj["gainLowPass"].set(gPrefsSettings.getChar("gainLowPass", 0));
		equalizerObj["gainBandPass"].set(gPrefsSettings.getChar("gainBandPass", 0));
		equalizerObj["gainHighPass"].set(gPrefsSettings.getChar("gainHighPass", 0));
	}
	if ((section == "") || (section == "wifi")) {
		// WiFi settings
		JsonObject wifiObj = obj["wifi"].to<JsonObject>();
		wifiObj["hostname"] = Wlan_GetHostname();
		wifiObj["scanOnStart"].set(gPrefsSettings.getBool("ScanWiFiOnStart", false));
		wifiObj["apSSID"] = Wlan_GetApSSID();
		wifiObj["apPassword"] = Wlan_GetApPassword();
		wifiObj["apTimeout"] = Wlan_GetApTimeoutMinutes();
	}
	if (section == "ssids") {
		// saved SSID's
		JsonObject ssidsObj = obj["ssids"].to<JsonObject>();
		JsonArray ssidArr = ssidsObj["savedSSIDs"].to<JsonArray>();
		Wlan_GetSavedNetworks([ssidArr](const WiFiSettings &network) {
			ssidArr.add(network.ssid);
		});

		// active SSID
		if (Wlan_IsConnected()) {
			ssidsObj["active"] = Wlan_GetCurrentSSID();
		}
	}
#ifdef NEOPIXEL_ENABLE
	if ((section == "") || (section == "led")) {
		// LED settings
		JsonObject ledObj = obj["led"].to<JsonObject>();
		ledObj["initBrightness"].set(gPrefsSettings.getUChar("iLedBrightness", 0));
		ledObj["nightBrightness"].set(gPrefsSettings.getUChar("nLedBrightness", 0));
		ledObj["atmoBrightness"].set(gPrefsSettings.getUChar("aLedBrightness", 0));
		ledObj["numIndicator"].set(gPrefsSettings.getUChar("numIndicator", 24)); // NUM_INDICATOR_LEDS
		uint8_t numControlLeds = gPrefsSettings.getUChar("numControl", 0); // NUM_CONTROL_LEDS
		ledObj["numControl"].set(numControlLeds);
		if (numControlLeds > 0) {
			// get control led colors from NVS
			std::vector<CRGB::HTMLColorCode> controlLedColors = {}; // CONTROL_LEDS_COLORS
			size_t keySize = gPrefsSettings.getBytesLength("controlColors");
			if (keySize == (numControlLeds * sizeof(CRGB::HTMLColorCode))) {
				controlLedColors.resize(numControlLeds);
				gPrefsSettings.getBytes("controlColors", controlLedColors.data(), keySize);
			}
			if (controlLedColors.size() > 0) {
				JsonArray colorArr = ledObj["controlColors"].to<JsonArray>();
				for (uint8_t controlLed = 0; controlLed < controlLedColors.size(); controlLed++) {
					colorArr.add(controlLedColors[controlLed]);
				}
			}
		}
		ledObj["numIdleDots"].set(gPrefsSettings.getUChar("numIdleDots", 4)); // NUM_LEDS_IDLE_DOTS
		ledObj["offsetPause"].set(gPrefsSettings.getBool("offsetPause", false)); // OFFSET_PAUSE_LEDS
		ledObj["rfidFlash"].set(gPrefsSettings.getBool("ledRfidFlash", false)); // LED_FLASH_ON_RFID
		ledObj["hueStart"].set(gPrefsSettings.getShort("hueStart", 85)); // PROGRESS_HUE_START
		ledObj["hueEnd"].set(gPrefsSettings.getShort("hueEnd", -1)); // PROGRESS_HUE_END
		ledObj["hueAtmo"].set(gPrefsSettings.getShort("hueAtmo", 10)); // ATMO_HUE
		ledObj["satAtmo"].set(gPrefsSettings.getShort("satAtmo", 180)); // ATMO_SATURATION
		ledObj["dimStates"].set(gPrefsSettings.getUChar("dimStates", 50)); // DIMMABLE_STATES
		ledObj["reverseRot"].set(gPrefsSettings.getBool("ledReverseRot", false));
		ledObj["offsetStart"].set(gPrefsSettings.getUChar("ledOffset", 0));
	}
#endif
	if ((section == "") || (section == "buttons")) {
		// button settings
		JsonObject buttonsObj = obj["buttons"].to<JsonObject>();
		for (uint8_t i = 0; i < 6; i++) { // "hold button + turn encoder" gestures
			char keyCw[12], keyCcw[13], jsonCw[10], jsonCcw[11];
			snprintf(keyCw, sizeof(keyCw), "btnRotCw%u", i);
			snprintf(keyCcw, sizeof(keyCcw), "btnRotCcw%u", i);
			snprintf(jsonCw, sizeof(jsonCw), "rotCw%u", i);
			snprintf(jsonCcw, sizeof(jsonCcw), "rotCcw%u", i);
			buttonsObj[jsonCw].set(Button_GetRotaryAction(i, true));
			buttonsObj[jsonCcw].set(Button_GetRotaryAction(i, false));
		}
		buttonsObj["short0"].set(gPrefsSettings.getUChar("btnShort0", BUTTON_0_SHORT));
		buttonsObj["short1"].set(gPrefsSettings.getUChar("btnShort1", BUTTON_1_SHORT));
		buttonsObj["short2"].set(gPrefsSettings.getUChar("btnShort2", BUTTON_2_SHORT));
		buttonsObj["short3"].set(gPrefsSettings.getUChar("btnShort3", BUTTON_3_SHORT));
		buttonsObj["short4"].set(gPrefsSettings.getUChar("btnShort4", BUTTON_4_SHORT));
		buttonsObj["short5"].set(gPrefsSettings.getUChar("btnShort5", BUTTON_5_SHORT));
		buttonsObj["long0"].set(gPrefsSettings.getUChar("btnLong0", BUTTON_0_LONG));
		buttonsObj["long1"].set(gPrefsSettings.getUChar("btnLong1", BUTTON_1_LONG));
		buttonsObj["long2"].set(gPrefsSettings.getUChar("btnLong2", BUTTON_2_LONG));
		buttonsObj["long3"].set(gPrefsSettings.getUChar("btnLong3", BUTTON_3_LONG));
		buttonsObj["long4"].set(gPrefsSettings.getUChar("btnLong4", BUTTON_4_LONG));
		buttonsObj["long5"].set(gPrefsSettings.getUChar("btnLong5", BUTTON_5_LONG));
		buttonsObj["multi01"].set(gPrefsSettings.getUChar("btnMulti01", BUTTON_MULTI_01));
		buttonsObj["multi02"].set(gPrefsSettings.getUChar("btnMulti02", BUTTON_MULTI_02));
		buttonsObj["multi03"].set(gPrefsSettings.getUChar("btnMulti03", BUTTON_MULTI_03));
		buttonsObj["multi04"].set(gPrefsSettings.getUChar("btnMulti04", BUTTON_MULTI_04));
		buttonsObj["multi05"].set(gPrefsSettings.getUChar("btnMulti05", BUTTON_MULTI_05));
		buttonsObj["multi12"].set(gPrefsSettings.getUChar("btnMulti12", BUTTON_MULTI_12));
		buttonsObj["multi13"].set(gPrefsSettings.getUChar("btnMulti13", BUTTON_MULTI_13));
		buttonsObj["multi14"].set(gPrefsSettings.getUChar("btnMulti14", BUTTON_MULTI_14));
		buttonsObj["multi15"].set(gPrefsSettings.getUChar("btnMulti15", BUTTON_MULTI_15));
		buttonsObj["multi23"].set(gPrefsSettings.getUChar("btnMulti23", BUTTON_MULTI_23));
		buttonsObj["multi24"].set(gPrefsSettings.getUChar("btnMulti24", BUTTON_MULTI_24));
		buttonsObj["multi25"].set(gPrefsSettings.getUChar("btnMulti25", BUTTON_MULTI_25));
		buttonsObj["multi34"].set(gPrefsSettings.getUChar("btnMulti34", BUTTON_MULTI_34));
		buttonsObj["multi35"].set(gPrefsSettings.getUChar("btnMulti35", BUTTON_MULTI_35));
		buttonsObj["multi45"].set(gPrefsSettings.getUChar("btnMulti45", BUTTON_MULTI_45));
	}
	if ((section == "") || (section == "rotary")) {
		// Rotary encoder
		JsonObject rotaryObj = obj["rotary"].to<JsonObject>();
		rotaryObj["reverse"].set(gPrefsSettings.getBool("rotaryReverse", false));
		rotaryObj["seekPrevDelay"].set(gPrefsSettings.getUShort("seekPrevDelay", 2000)); // ms idle before a CMD_SEEK_PREVIEW gesture auto-commits
		rotaryObj["seekPrevSweep"].set(gPrefsSettings.getUChar("seekPrevSweep", 40)); // encoder detents for a full 0->100% sweep
	}
	// playlist
	if ((section == "") || (section == "playlist")) {
		JsonObject playlistObj = obj["playlist"].to<JsonObject>();
		playlistObj["sortMode"] = EnumUtils::underlying_value(AudioPlayer_GetPlaylistSortMode());
		playlistObj["recDepth"] = SdCard_GetMaxRecursionDepth();
	}
#ifdef BATTERY_MEASURE_ENABLE
	if ((section == "") || (section == "battery")) {
		// battery settings
		JsonObject batteryObj = obj["battery"].to<JsonObject>();
	#ifdef MEASURE_BATTERY_VOLTAGE
		batteryObj["warnLowVoltage"].set(gPrefsSettings.getFloat("wLowVoltage", s_warningLowVoltage));
		batteryObj["indicatorLow"].set(gPrefsSettings.getFloat("vIndicatorLow", s_voltageIndicatorLow));
		batteryObj["indicatorHi"].set(gPrefsSettings.getFloat("vIndicatorHigh", s_voltageIndicatorHigh));
		batteryObj["criticalVoltage"].set(gPrefsSettings.getFloat("wCritVoltage", s_warningCriticalVoltage));
		batteryObj["offsetVoltage"].set(gPrefsSettings.getFloat("offsetVoltage", s_offsetVoltage));
		batteryObj["shutdownOnCritical"].set(gPrefsSettings.getBool("shutdownBatCrit", false)); // SHUTDOWN_ON_BAT_CRITICAL
		batteryObj["warnSound"].set(gPrefsSettings.getBool("batWarnSound", false)); // spoken low-battery warning
		batteryObj["warnSoundOnce"].set(gPrefsSettings.getBool("batWarnOnce", false));
		batteryObj["warnSoundFile"].set(gPrefsSettings.getString("batWarnFile", ""));
	#endif

		batteryObj["voltageCheckInterval"].set(gPrefsSettings.getUInt("vCheckIntv", s_batteryCheckInterval));
	}
#endif
	if (section == "defaults") {
		// default factory settings NOTE: maintain the settings section structure as above to make it easier for clients to use
		JsonObject defaultsObj = obj["defaults"].to<JsonObject>();
		JsonObject genSettings = defaultsObj["general"].to<JsonObject>();
		genSettings["initVolume"].set(AUDIOPLAYER_VOLUME_INIT);
		genSettings["minVolume"].set(AUDIOPLAYER_VOLUME_MIN);
		genSettings["maxVolumeSp"].set(AUDIOPLAYER_VOLUME_MAX);
		genSettings["maxVolumeHp"].set(18u); // gPrefsSettings.getUInt("maxVolumeHp", 0));
		genSettings["sleepInactivity"].set(10u); // System_MaxInactivityTime
		genSettings["playMono"].set(false); // PLAY_MONO_SPEAKER
		genSettings["savePosShutdown"].set(false); // SAVE_PLAYPOS_BEFORE_SHUTDOWN
		genSettings["savePosRfidChge"].set(false); // SAVE_PLAYPOS_WHEN_RFID_CHANGE
		genSettings["savePosInterval"].set(0); // SAVE_PLAYPOS_INTERVAL (periodic checkpoint seconds, 0 = off)
		genSettings["playLastRfidOnReboot"].set(false); // PLAY_LAST_RFID_AFTER_REBOOT
		genSettings["pauseIfRfidRemoved"].set(false); // PAUSE_WHEN_RFID_REMOVED
		genSettings["dontAcceptRfidTwice"].set(false); // DONT_ACCEPT_SAME_RFID_TWICE
		genSettings["resumeOnSameRfid"].set(false); // RESUME_ON_SAME_RFID
		genSettings["pauseOnMinVol"].set(false); // PAUSE_ON_MIN_VOLUME
		genSettings["nightVolLimit"].set(false); // NIGHT_MODE_VOLUME_LIMIT
		genSettings["recoverVolBoot"].set(false); // USE_LAST_VOLUME_AFTER_REBOOT
		genSettings["volumeCurve"].set(0u); // VOLUME_CURVE
		genSettings["rfidReaderType"].set(0u); // RFID_READER_TYPE_RUNTIME (auto-detect)
		genSettings["pn5180Lpcd"].set(false); // PN5180 LPCD disabled
		genSettings["mfrc522Gain"].set(7u); // MFRC522_GAIN default (max gain)
		genSettings["mfrc522ScanInterval"].set(100u); // RFID_SCAN_INTERVAL default
		genSettings["pn5180Debounce"].set(500u); // PN5180 debounce (ms) default
		genSettings["slixPrivacyPassword"].set(slixPrivacyPasswordToHex(SLIX_PRIVACY_PASSWORD_DEFAULT));
		JsonObject eqSettings = defaultsObj["equalizer"].to<JsonObject>();
		eqSettings["gainHighPass"].set(0);
		eqSettings["gainBandPass"].set(0);
		eqSettings["gainLowPass"].set(0);
#ifdef NEOPIXEL_ENABLE
		JsonObject ledSettings = defaultsObj["led"].to<JsonObject>();
		ledSettings["initBrightness"].set(16u); // LED_INITIAL_BRIGHTNESS
		ledSettings["nightBrightness"].set(2u); // LED_INITIAL_NIGHT_BRIGHTNESS
		ledSettings["atmoBrightness"].set(30u); // LED_INITIAL_NIGHT_BRIGHTNESS
		ledSettings["numIndicator"].set(24u); // NUM_INDICATOR_LEDS
		ledSettings["numControl"].set(0u); // NUM_CONTROL_LEDS
		ledSettings["numIdleDots"].set(4u); // NUM_LEDS_IDLE_DOTS
		ledSettings["offsetPause"].set(false); // OFFSET_PAUSE_LEDS
		ledSettings["rfidFlash"].set(false); // LED_FLASH_ON_RFID
		ledSettings["hueStart"].set(85); // PROGRESS_HUE_START
		ledSettings["hueEnd"].set(-1); // PROGRESS_HUE_END
		ledSettings["hueAtmo"].set(10); // ATMO_HUE
		ledSettings["satAtmo"].set(180); // ATMO_SATURATION
		ledSettings["dimStates"].set(50u); // DIMMABLE_STATES
		ledSettings["reverseRot"].set(false); // NEOPIXEL_REVERSE_ROTATION
		ledSettings["offsetStart"].set(0); // LED_OFFSET
		JsonArray colorArr = ledSettings["controlColors"].to<JsonArray>();
		std::vector<CRGB::HTMLColorCode> controlLedColors = {}; // CONTROL_LEDS_COLORS
		for (uint8_t controlLed = 0; controlLed < controlLedColors.size(); controlLed++) {
			colorArr.add(controlLedColors[controlLed]);
		}
#endif
		JsonObject buttonsSettings = defaultsObj["buttons"].to<JsonObject>();
		buttonsSettings["short0"].set(BUTTON_0_SHORT);
		buttonsSettings["short1"].set(BUTTON_1_SHORT);
		buttonsSettings["short2"].set(BUTTON_2_SHORT);
		buttonsSettings["short3"].set(BUTTON_3_SHORT);
		buttonsSettings["short4"].set(BUTTON_4_SHORT);
		buttonsSettings["short5"].set(BUTTON_5_SHORT);
		buttonsSettings["long0"].set(BUTTON_0_LONG);
		buttonsSettings["long1"].set(BUTTON_1_LONG);
		buttonsSettings["long2"].set(BUTTON_2_LONG);
		buttonsSettings["long3"].set(BUTTON_3_LONG);
		buttonsSettings["long4"].set(BUTTON_4_LONG);
		buttonsSettings["long5"].set(BUTTON_5_LONG);
		buttonsSettings["multi01"].set(BUTTON_MULTI_01);
		buttonsSettings["multi02"].set(BUTTON_MULTI_02);
		buttonsSettings["multi03"].set(BUTTON_MULTI_03);
		buttonsSettings["multi04"].set(BUTTON_MULTI_04);
		buttonsSettings["multi05"].set(BUTTON_MULTI_05);
		buttonsSettings["multi12"].set(BUTTON_MULTI_12);
		buttonsSettings["multi13"].set(BUTTON_MULTI_13);
		buttonsSettings["multi14"].set(BUTTON_MULTI_14);
		buttonsSettings["multi15"].set(BUTTON_MULTI_15);
		buttonsSettings["multi23"].set(BUTTON_MULTI_23);
		buttonsSettings["multi24"].set(BUTTON_MULTI_24);
		buttonsSettings["multi25"].set(BUTTON_MULTI_25);
		buttonsSettings["multi34"].set(BUTTON_MULTI_34);
		buttonsSettings["multi35"].set(BUTTON_MULTI_35);
		buttonsSettings["multi45"].set(BUTTON_MULTI_45);
		for (uint8_t i = 0; i < 6; i++) { // "hold button + turn encoder" gestures
			char jsonCw[10], jsonCcw[11];
			snprintf(jsonCw, sizeof(jsonCw), "rotCw%u", i);
			snprintf(jsonCcw, sizeof(jsonCcw), "rotCcw%u", i);
			buttonsSettings[jsonCw].set(Button_GetRotaryActionDefault(i, true));
			buttonsSettings[jsonCcw].set(Button_GetRotaryActionDefault(i, false));
		}
#ifdef USEROTARY_ENABLE
		JsonObject rotarySettings = defaultsObj["rotary"].to<JsonObject>();
		rotarySettings["reverse"].set(false); // REVERSE_ROTARY
		rotarySettings["seekPrevDelay"].set(2000);
		rotarySettings["seekPrevSweep"].set(40);
#endif
		JsonObject playlistSettings = defaultsObj["playlist"].to<JsonObject>();
		playlistSettings["sortMode"].set(EnumUtils::underlying_value(AUDIOPLAYER_PLAYLIST_SORT_MODE_DEFAULT));
		playlistSettings["recDepth"].set(2u);
#ifdef BATTERY_MEASURE_ENABLE
		JsonObject batSettings = defaultsObj["battery"].to<JsonObject>();
	#ifdef MEASURE_BATTERY_VOLTAGE
		batSettings["warnLowVoltage"].set(s_warningLowVoltage);
		batSettings["indicatorLow"].set(s_voltageIndicatorLow);
		batSettings["indicatorHi"].set(s_voltageIndicatorHigh);
		batSettings["criticalVoltage"].set(s_warningCriticalVoltage);
		batSettings["shutdownOnCritical"].set(false); // SHUTDOWN_ON_BAT_CRITICAL
		batSettings["warnSound"].set(false);
		batSettings["warnSoundOnce"].set(false);
		batSettings["warnSoundFile"].set("");
	#endif
		batSettings["voltageCheckInterval"].set(s_batteryCheckInterval);
#endif
	}
// FTP
#ifdef FTP_ENABLE
	if ((section == "") || (section == "ftp")) {
		JsonObject ftpObj = obj["ftp"].to<JsonObject>();
		ftpObj["username"] = gPrefsSettings.getString("ftpuser", "-1");
		ftpObj["password"] = gPrefsSettings.getString("ftppassword", "-1");
		ftpObj["maxUserLength"].set(ftpUserLength - 1);
		ftpObj["maxPwdLength"].set(ftpUserLength - 1);
	}
#endif
// MQTT
#ifdef MQTT_ENABLE
	if ((section == "") || (section == "mqtt")) {
		JsonObject mqttObj = obj["mqtt"].to<JsonObject>();
		mqttObj["enable"].set(Mqtt_IsEnabled());
		String macPlain = Wlan_GetMacAddress(); // returns AA:BB:CC:DD:EE:FF or empty
		macPlain.replace(":", "");
		macPlain.toUpperCase();
		mqttObj["macAddressPlain"] = macPlain;
		mqttObj["clientID"] = gPrefsSettings.getString("mqttClientId", "-1");
		mqttObj["deviceId"] = gPrefsSettings.getString("mqttDeviceId", "-1");
		mqttObj["baseTopic"] = gPrefsSettings.getString("mqttBaseTopic", "-1");
		mqttObj["server"] = gPrefsSettings.getString("mqttServer", "-1");
		mqttObj["port"].set(gPrefsSettings.getUInt("mqttPort", 0));
		mqttObj["username"] = gPrefsSettings.getString("mqttUser", "-1");
		mqttObj["password"] = gPrefsSettings.getString("mqttPassword", "-1");
		mqttObj["maxUserLength"].set(mqttUserLength - 1);
		mqttObj["maxPwdLength"].set(mqttPasswordLength - 1);
		mqttObj["maxClientIdLength"].set(mqttClientIdLength - 1);
		mqttObj["maxServerLength"].set(mqttServerLength - 1);
		mqttObj["maxBaseTopicLength"].set(mqttBaseTopicLength - 1);
		mqttObj["maxDeviceIdLength"].set(mqttDeviceIdLength - 1);
	}
#endif
// Bluetooth
#ifdef BLUETOOTH_ENABLE
	if ((section == "") || (section == "bluetooth")) {
		JsonObject btObj = obj["bluetooth"].to<JsonObject>();
		if (gPrefsSettings.isKey("btDeviceName")) {
			btObj["deviceName"] = gPrefsSettings.getString("btDeviceName", "");
		} else {
			btObj["deviceName"] = "";
		}
		if (gPrefsSettings.isKey("btPinCode")) {
			btObj["pinCode"] = gPrefsSettings.getString("btPinCode", "");
		} else {
			btObj["pinCode"] = "";
		}
	}
#endif
}

// handle get info
void handleGetInfo(AsyncWebServerRequest *request) {

	// param to get a single info section
	String section = "";
	if (request->hasParam("section")) {
		section = request->getParam("section")->value();
	}
	AsyncJsonResponse *response = new AsyncJsonResponse(false);
	JsonObject infoObj = response->getRoot();
	// software
	if ((section == "") || (section == "software")) {
		JsonObject softwareObj = infoObj["software"].to<JsonObject>();
		softwareObj["version"] = (String) softwareRevision;
		softwareObj["git"] = (String) gitRevision;
		softwareObj["branch"] = (String) gitBranch;
		softwareObj["arduino"] = String(ESP_ARDUINO_VERSION_MAJOR) + "." + String(ESP_ARDUINO_VERSION_MINOR) + "." + String(ESP_ARDUINO_VERSION_PATCH);
		softwareObj["idf"] = String(ESP.getSdkVersion());
		softwareObj["platform"] = (String) espuinoPlatform;
		softwareObj["customBuild"] = espuinoCustomBuild;
#ifdef BOARD_HAS_16MB_FLASH_AND_OTA_SUPPORT
		softwareObj["otaSupported"] = true;
#else
		softwareObj["otaSupported"] = false;
#endif
	}
	// hardware
	if ((section == "") || (section == "hardware")) {
		JsonObject hardwareObj = infoObj["hardware"].to<JsonObject>();
		hardwareObj["model"] = String(ESP.getChipModel());
		hardwareObj["revision"] = ESP.getChipRevision();
		hardwareObj["freq"] = ESP.getCpuFreqMHz();
	}
	// memory
	if ((section == "") || (section == "memory")) {
		JsonObject memoryObj = infoObj["memory"].to<JsonObject>();
		memoryObj["freeHeap"] = ESP.getFreeHeap();
		memoryObj["largestFreeBlock"] = (uint32_t) heap_caps_get_largest_free_block(MALLOC_CAP_8BIT);
		memoryObj["freePSRam"] = ESP.getFreePsram();
		memoryObj["largestFreePSRamBlock"] = String(ESP.getMaxAllocPsram());
	}
	// SD card
	if ((section == "") || (section == "sdcard")) {
		JsonObject sdCardObj = infoObj["sdcard"].to<JsonObject>();
		const bool available = SdCard_IsMounted();
		const uint64_t totalBytes = available ? SdCard_GetTotalSize() : 0;
		const uint64_t usedBytesRaw = available ? SdCard_GetUsedSize() : 0;
		const bool statsAvailable = totalBytes > 0 && usedBytesRaw <= totalBytes;
		const uint64_t usedBytes = statsAvailable ? usedBytesRaw : 0;
		const uint64_t freeBytes = statsAvailable ? totalBytes - usedBytes : 0;

		// Send byte counts as decimal strings. This keeps all 64 bits intact,
		// independent of JSON-number configuration; the browser converts them
		// with Number(...) before formatting.
		char totalBytesText[24];
		char usedBytesText[24];
		char freeBytesText[24];
		snprintf(totalBytesText, sizeof(totalBytesText), "%llu", static_cast<unsigned long long>(totalBytes));
		snprintf(usedBytesText, sizeof(usedBytesText), "%llu", static_cast<unsigned long long>(usedBytes));
		snprintf(freeBytesText, sizeof(freeBytesText), "%llu", static_cast<unsigned long long>(freeBytes));

		sdCardObj["available"] = available;
		sdCardObj["statsAvailable"] = statsAvailable;
		sdCardObj["totalBytes"] = totalBytesText;
		sdCardObj["usedBytes"] = usedBytesText;
		sdCardObj["freeBytes"] = freeBytesText;
	}
	// wifi
	if ((section == "") || (section == "wifi")) {
		JsonObject wifiObj = infoObj["wifi"].to<JsonObject>();
		wifiObj["ip"] = Wlan_GetIpAddress();
		wifiObj["macAddress"] = Wlan_GetMacAddress();
		wifiObj["rssi"] = (int8_t) Wlan_GetRssi();
	}
	// audio
	if ((section == "") || (section == "audio")) {
		JsonObject audioObj = infoObj["audio"].to<JsonObject>();
		audioObj["playtimeTotal"] = AudioPlayer_GetPlayTimeAllTime();
		audioObj["playtimeSinceStart"] = AudioPlayer_GetPlayTimeSinceStart();
		audioObj["firstStart"] = gPrefsSettings.getULong("firstStart", 0);
	}
#ifdef BATTERY_MEASURE_ENABLE
	// battery
	if ((section == "") || (section == "battery")) {
		JsonObject batteryObj = infoObj["battery"].to<JsonObject>();
		batteryObj["currVoltage"] = Battery_GetVoltage();
		batteryObj["chargeLevel"] = Battery_EstimateLevel() * 100;
	}
#endif
#ifdef HALLEFFECT_SENSOR_ENABLE
	if ((section == "") || (section == "hallsensor")) {
		// hallsensor
		JsonObject hallObj = infoObj["hallsensor"].to<JsonObject>();
		uint16_t sva = gHallEffectSensor.readSensorValueAverage(true);
		int diff = sva - gHallEffectSensor.NullFieldValue();

		hallObj["nullFieldValue"] = gHallEffectSensor.NullFieldValue();
		hallObj["actual"] = sva;
		hallObj["diff"] = diff;
		hallObj["lastWaitState"] = gHallEffectSensor.LastWaitForState();
		hallObj["lastWaitMS"] = gHallEffectSensor.LastWaitForStateMS();
	}
#endif

	if (response->overflowed()) {
		// JSON buffer too small for data
		Log_Println(jsonbufferOverflow, LOGLEVEL_ERROR);
		request->send(500);
		return;
	}
	response->setLength();
	request->send(response);
	System_UpdateActivityTimer();
}

// handle get settings
void handleGetSettings(AsyncWebServerRequest *request) {

	// param to get a single settings section
	String section = "";
	if (request->hasParam("section")) {
		section = request->getParam("section")->value();
	}

	AsyncJsonResponse *response = new AsyncJsonResponse(false);
	JsonObject settingsObj = response->getRoot();
	settingsToJSON(settingsObj, section);
	if (response->overflowed()) {
		// JSON buffer too small for data
		Log_Println(jsonbufferOverflow, LOGLEVEL_ERROR);
		request->send(500);
		return;
	}
	response->setLength();
	request->send(response);
}

// handle post settings
void handlePostSettings(AsyncWebServerRequest *request, JsonVariant &json) {
	const JsonObject &jsonObj = json.as<JsonObject>();
	WebsocketCodeType res = JSONToSettings(jsonObj);
	if (res != WebsocketCodeType::Error) {
		if (res != WebsocketCodeType::Ok && res != WebsocketCodeType::Silent) {
			Web_SendWebsocketData(0, res);
		}
		request->send(200);
	} else {
		request->send(500, "text/plain; charset=utf-8", "error saving settings");
	}
}

// handle get operation mode
void handleGetOperationMode(AsyncWebServerRequest *request) {
	AsyncJsonResponse *response = new AsyncJsonResponse(false);
	JsonObject object = response->getRoot();
	object["mode"] = System_GetOperationMode();
	response->setLength();
	request->send(response);
}

// handle post operation mode
void handlePostOperationMode(AsyncWebServerRequest *request, JsonVariant &json) {
	const JsonObject &jsonObj = json.as<JsonObject>();
	if (jsonObj["mode"].is<uint8_t>()) {
		uint8_t mode = jsonObj["mode"].as<uint8_t>();
		System_SetOperationMode(mode);
		request->send(200);
	} else {
		request->send(400, "text/plain; charset=utf-8", "missing 'mode' parameter");
	}
}

// handle debug request
// returns memory and task runtime information as JSON
void handleDebugRequest(AsyncWebServerRequest *request) {

	AsyncJsonResponse *response = new AsyncJsonResponse(false);
#ifdef CONFIG_FREERTOS_USE_TRACE_FACILITY
	JsonObject infoObj = response->getRoot();
	// task runtime info
	uint32_t pulTotalRunTime;
	uint32_t taskCount = uxTaskGetNumberOfTasks();
	std::vector<TaskStatus_t> task_status_arr(taskCount + 5);

	Log_Printf(LOGLEVEL_DEBUG, "number of tasks: %u", taskCount);

	uint32_t taskNum = uxTaskGetSystemState(task_status_arr.data(), task_status_arr.size(), &pulTotalRunTime);

	JsonObject tasksObj = infoObj["tasks"].to<JsonObject>();
	tasksObj["taskCount"] = taskNum;
	tasksObj["totalRunTime"] = pulTotalRunTime;
	JsonArray tasksList = tasksObj["tasksList"].to<JsonArray>();

	for (int i = 0; i < taskNum; i++) {
		JsonObject taskObj = tasksList.add<JsonObject>();

		float ulStatsAsPercentage = 100.f * ((float) task_status_arr[i].ulRunTimeCounter / (float) pulTotalRunTime);

		taskObj["name"] = task_status_arr[i].pcTaskName;
		taskObj["runtimeCounter"] = task_status_arr[i].ulRunTimeCounter;
		taskObj["core"] = task_status_arr[i].xCoreID;
		taskObj["runtimePercentage"] = ulStatsAsPercentage;
		taskObj["stackHighWaterMark"] = task_status_arr[i].usStackHighWaterMark;
	}
#endif
	if (response->overflowed()) {
		// JSON buffer too small for data
		Log_Println(jsonbufferOverflow, LOGLEVEL_ERROR);
		request->send(500);
		return;
	}
	response->setLength();
	request->send(response);
}

// Takes inputs from webgui, parses JSON and saves values in NVS
// If operation was successful (NVS-write is verified) true is returned
WebsocketCodeType processJsonRequest(char *_serialJson) {
	if (!_serialJson) {
		return WebsocketCodeType::Error;
	}
	SpiRamAllocator allocator;
	JsonDocument doc(&allocator);

	DeserializationError error = deserializeJson(doc, _serialJson);

	if (error) {
		Log_Printf(LOGLEVEL_ERROR, jsonErrorMsg, error.c_str());
		return WebsocketCodeType::Error;
	}

	JsonObject obj = doc.as<JsonObject>();
	return JSONToSettings(obj);
}

// Sends JSON-answers via websocket
void Web_SendWebsocketData(uint32_t client, WebsocketCodeType code) {
	if (!webserverStarted) {
		// webserver not yet started
		return;
	}
	if (ws.count() == 0) {
		// we do not have any webclient connected
		return;
	}

	SpiRamAllocator allocator;
	JsonDocument doc(&allocator);

	JsonObject object = doc.to<JsonObject>();

	if (code == WebsocketCodeType::Ok) {
		object["status"] = "ok";
	} else if (code == WebsocketCodeType::Error) {
		object["status"] = "error";
	} else if (code == WebsocketCodeType::Dropout) {
		object["status"] = "dropout";
	} else if (code == WebsocketCodeType::NotAllowedInCurrentMode) {
		object["status"] = "not_allowed_in_current_mode";
	} else if (code == WebsocketCodeType::CurrentRfid) {
		object["rfidId"] = gCurrentRfidTagId;
	} else if (code == WebsocketCodeType::Pong) {
		object["pong"] = "pong";
		object["rssi"] = Wlan_GetRssi();
		// todo: battery percent + loading status +++
		// object["battery"] = Battery_GetVoltage();
	} else if (code == WebsocketCodeType::OperationMode) {
		object["opmode"] = System_GetOperationMode();
	} else if (code == WebsocketCodeType::TrackInfo) {
		JsonObject entry = object["trackinfo"].to<JsonObject>();
		entry["pausePlay"] = gPlayProperties.pausePlay;
		entry["currentTrackNumber"] = gPlayProperties.currentTrackNumber + 1;
		entry["numberOfTracks"] = (gPlayProperties.playlist) ? gPlayProperties.playlist->size() : 0;
		entry["volume"] = AudioPlayer_GetCurrentVolume();
		entry["name"] = gPlayProperties.title;
		entry["posPercent"] = gPlayProperties.currentRelPos;
		entry["playMode"] = gPlayProperties.playMode;
	} else if (code == WebsocketCodeType::CoverImg) {
		object["coverimg"] = "coverimg";
	} else if (code == WebsocketCodeType::Volume) {
		object["volume"] = AudioPlayer_GetCurrentVolume();
	} else if (code == WebsocketCodeType::Settings) {
		JsonObject entry = object["settings"].to<JsonObject>();
		settingsToJSON(entry, "");
	} else if (code == WebsocketCodeType::Ssid) {
		JsonObject entry = object["settings"].to<JsonObject>();
		settingsToJSON(entry, "ssids");
	} else if (code == WebsocketCodeType::TrackProgress) {
		JsonObject entry = object["trackProgress"].to<JsonObject>();
		entry["posPercent"] = gPlayProperties.currentRelPos;
		entry["time"] = AudioPlayer_GetCurrentTime();
		entry["duration"] = AudioPlayer_GetFileDuration();
	} else if (code == WebsocketCodeType::BluetoothScanInProgress) {
		object["bt_scan"] = "in_progress";
	} else if (code == WebsocketCodeType::BluetoothScanComplete) {
		object["bt_scan"] = "complete";
	};

	if (doc.overflowed()) {
		// JSON buffer too small for data
		Log_Println(jsonbufferOverflow, LOGLEVEL_ERROR);
	}

	// serialize JSON in a more optimized way using a shared buffer
	const size_t len = measureJson(doc);
	AsyncWebSocketMessageBuffer *jsonBuffer = ws.makeBuffer(len);
	if (!jsonBuffer) {
		// memory allocation of vector failed, we can not use the AsyncWebSocketMessageBuffer
		Log_Println(unableToAllocateMem, LOGLEVEL_ERROR);
		return;
	}
	serializeJson(doc, jsonBuffer->get(), len);
	if (client == 0) {
		ws.textAll(jsonBuffer);
	} else {
		ws.text(client, jsonBuffer);
	}
}

// Processes websocket-requests
void onWebsocketEvent(AsyncWebSocket *server, AsyncWebSocketClient *client, AwsEventType type, void *arg, uint8_t *data, size_t len) {

	// discard message on queue full, socket should not be closed
	client->setCloseClientOnQueueFull(false);

	if (type == WS_EVT_CONNECT) {
		// client connected
		Log_Printf(LOGLEVEL_DEBUG, "ws[%s][%u] connect", server->url(), client->id());
		// Send initial operation mode and RSSI to newly connected client
		Web_SendWebsocketData(client->id(), WebsocketCodeType::OperationMode);
		// client->printf("Hello Client %u :)", client->id());
		// client->ping();
	} else if (type == WS_EVT_DISCONNECT) {
		// client disconnected
		Log_Printf(LOGLEVEL_DEBUG, "ws[%s][%u] disconnect", server->url(), client->id());
	} else if (type == WS_EVT_ERROR) {
		// error was received from the other end
		Log_Printf(LOGLEVEL_DEBUG, "ws[%s][%u] error(%u): %s", server->url(), client->id(), *((uint16_t *) arg), (char *) data);
	} else if (type == WS_EVT_PONG) {
		// pong message was received (in response to a ping request maybe)
		Log_Printf(LOGLEVEL_DEBUG, "ws[%s][%u] pong[%u]: %s", server->url(), client->id(), len, (len) ? (char *) data : "");
	} else if (type == WS_EVT_DATA) {
		// data packet
		const AwsFrameInfo *info = (AwsFrameInfo *) arg;
		if (info && info->final && info->index == 0 && info->len == len && client && len > 0) {
			// the whole message is in a single frame and we got all of it's data
			// Serial.printf("ws[%s][%u] %s-message[%llu]: ", server->url(), client->id(), (info->opcode == WS_TEXT) ? "text" : "binary", info->len);

			WebsocketCodeType result = processJsonRequest((char *) data);
			if (result != WebsocketCodeType::Error && result != WebsocketCodeType::Silent) {
				Web_SendWebsocketData(client->id(), result);
			}

			if (info->opcode == WS_TEXT) {
				data[len] = 0;
				// Serial.printf("%s\n", (char *)data);
			} else {
				for (size_t i = 0; i < info->len; i++) {
					Serial.printf("%02x ", data[i]);
				}
				// Serial.printf("\n");
			}
		}
	}
}

// Handles a raw (non-multipart) file upload request from the explorer.
// requires a GET parameter path (folder + filename) for the target file.
// One request per file; the client loops over multiple files sequentially
// since only one upload can be in flight at a time (shared buffers below).
static void explorerHandleFileUpload(AsyncWebServerRequest *request, uint8_t *data, size_t len, size_t index, size_t total) {
	System_UpdateActivityTimer();

	if (index == 0) {
		uploadAborted = false;

		String filePath = "/";
		if (request->hasParam("path")) {
			filePath = request->getParam("path")->value();
		}

		Log_Printf(LOGLEVEL_INFO, writingFile, filePath.c_str());

		if (!allocateDoubleBuffer()) {
			// we failed to allocate enough memory
			Log_Println(unableToAllocateMem, LOGLEVEL_ERROR);
			handleUploadError(request, 500);
			return;
		}

		if (explorerFileUploadFinished == NULL) {
			explorerFileUploadFinished = xSemaphoreCreateBinary();
		} else {
			// make sure semaphore is empty
			xSemaphoreTake(explorerFileUploadFinished, 0);
		}

		// reset buffers
		index_buffer_write = 0;
		index_buffer_read = 0;
		for (uint32_t i = 0; i < nr_of_buffers; i++) {
			size_in_buffer[i] = 0;
			buffer_full[i] = false;
		}

		const char *filePathCopy = x_strdup(filePath.c_str());
		xTaskCreatePinnedToCore(
			explorerHandleFileStorageTask, /* Function to implement the task */
			"fileStorageTask", /* Name of the task */
			4000, /* Stack size in words */
			(void *) filePathCopy, /* Task input parameter */
			2 | portPRIVILEGE_BIT, /* Priority of the task */
			&fileStorageTaskHandle, /* Task handle. */
			1 /* Core where the task should run */
		);

		request->onDisconnect([]() {
			xTaskNotify(fileStorageTaskHandle, 2u, eSetValueWithOverwrite);
		});
	}

	if (uploadAborted) {
		if (!request->_tempObject) {
			handleUploadError(request, 500);
		}
		return;
	}

	if (len) {
		// wait till buffer is ready
		while (buffer_full[index_buffer_write]) {
			if (uploadAborted) {
				return;
			}
			vTaskDelay(2u);
		}

		size_t len_to_write = len;
		size_t space_left = chunk_size - size_in_buffer[index_buffer_write];
		if (space_left < len_to_write) {
			len_to_write = space_left;
		}
		// write content to buffer
		memcpy(buffer[index_buffer_write] + size_in_buffer[index_buffer_write], data, len_to_write);
		size_in_buffer[index_buffer_write] = size_in_buffer[index_buffer_write] + len_to_write;

		// check if buffer is filled. If full, signal that ready and change buffers
		if (size_in_buffer[index_buffer_write] == chunk_size) {
			// signal, that buffer is ready. Increment index
			buffer_full[index_buffer_write] = true;
			index_buffer_write = (index_buffer_write + 1) % nr_of_buffers;

			// if still content left, put it into next buffer
			if (len_to_write < len) {
				// wait till new buffer is ready
				while (buffer_full[index_buffer_write]) {
					if (uploadAborted) {
						return;
					}
					vTaskDelay(2u);
				}
				size_t len_left_to_write = len - len_to_write;
				memcpy(buffer[index_buffer_write], data + len_to_write, len_left_to_write);
				size_in_buffer[index_buffer_write] = len_left_to_write;
			}
		}
	}

	if (index + len >= total) {
		if (uploadAborted) {
			handleUploadError(request, 500);
			return;
		}
		// if file not completely done yet, signal that buffer is filled
		if (size_in_buffer[index_buffer_write] > 0) {
			buffer_full[index_buffer_write] = true;
		}
		// notify storage task that last data was stored on the ring buffer
		xTaskNotify(fileStorageTaskHandle, 1u, eSetValueWithOverwrite);
		// wait until the storage task is sending the signal to finish
		if (xSemaphoreTake(explorerFileUploadFinished, pdMS_TO_TICKS(30000)) != pdTRUE) {
			// timeout, something went wrong
			Log_Println(webTxCanceled, LOGLEVEL_ERROR);
			handleUploadError(request, 500);
			return;
		}
	}
}

// task for writing uploaded data from buffer to SD
// parameter contains the target file path and must be freed by the task.
static void explorerHandleFileStorageTask(void *parameter) {
	const char *filePath = (const char *) parameter;
	File uploadFile;
	size_t bytesOk = 0;
	uint32_t chunkCount = 0;
	uint32_t transferStartTimestamp = millis();
	uint32_t lastUpdateTimestamp = millis();
	uint32_t maxUploadDelay = 30; // After this delay (in seconds) task will be deleted as transfer is considered to be finally broken

	BaseType_t uploadFileNotification;
	uint32_t uploadFileNotificationValue;

	// pause some tasks to get more free CPU time for the upload
	System_PauseTasksDuringUpload(true);

	uploadFile = gFSystem.open(filePath, "w", true); // open file with create=true to make sure parent directories are created
	if (uploadFile) {
		uploadFile.setBufferSize(chunk_size);
	} else {
		Log_Printf(LOGLEVEL_ERROR, "Failed to open file %s for writing!", filePath);
		uploadAborted = true;
	}

	for (;;) {
		if (uploadAborted) {
			break;
		}
		// check buffer is full with enough data or all data already sent
		uploadFileNotification = xTaskNotifyWait(0, 0, &uploadFileNotificationValue, 0);
		if ((buffer_full[index_buffer_read]) || (uploadFileNotification == pdPASS && uploadFileNotificationValue == 1u)) {

			while (buffer_full[index_buffer_read]) {
				chunkCount++;
				size_t item_size = size_in_buffer[index_buffer_read];
				size_t written = 0;
				if (item_size > 0) {
					const uint8_t maxRetries = 3;
					for (uint8_t attempt = 0; attempt < maxRetries && written != item_size; attempt++) {
						if (attempt > 0) {
							Log_Printf(LOGLEVEL_DEBUG, "Write retry %u for chunk %zu on %s", attempt, chunkCount, filePath);
							vTaskDelay(pdMS_TO_TICKS(20 * attempt)); // backoff: 20ms, 40ms
						}
						written = uploadFile.write(buffer[index_buffer_read], item_size);
					}
				}

				if (item_size > 0 && written != item_size) {
					Log_Printf(LOGLEVEL_ERROR, "Write error during upload of %s! (expected %u, wrote %u after retries)",
						filePath, item_size, (uint32_t) written);
					uploadAborted = true;
					break;
				} else {
					bytesOk += written;
				}
				// update handling of buffers
				size_in_buffer[index_buffer_read] = 0;
				buffer_full[index_buffer_read] = 0;
				index_buffer_read = (index_buffer_read + 1) % nr_of_buffers;
				if (chunkCount % 64 == 0) {
					uploadFile.flush();
					System_UpdateActivityTimer();
				}
				// update timestamp
				lastUpdateTimestamp = millis();
			}

			if (uploadFileNotification == pdPASS) {
				if (uploadFile) {
					uploadFile.close();
				}
				Log_Printf(LOGLEVEL_INFO, fileWritten, filePath, bytesOk, (millis() - transferStartTimestamp), (bytesOk) / (millis() - transferStartTimestamp));
				Log_Printf(LOGLEVEL_DEBUG, "Bytes [ok] %zu, Chunks: %zu\n", bytesOk, chunkCount);
				// done exit loop to terminate
				break;
			}
		} else {
			if ((lastUpdateTimestamp + (maxUploadDelay * 1000)) < millis() || ((uploadFileNotification == pdPASS) && (uploadFileNotificationValue == 2u))) {
				Log_Println(webTxCanceled, LOGLEVEL_ERROR);
				if (uploadFile) {
					uploadFile.close();
				}
				uploadAborted = true;
				xSemaphoreGive(explorerFileUploadFinished);
				break;
			}
			vTaskDelay(portTICK_PERIOD_MS * 2);
			continue;
		}
	}
	free(parameter);
	// resume the paused tasks
	System_PauseTasksDuringUpload(false);
	System_UpdateActivityTimer();
	// send signal to upload function to terminate
	xSemaphoreGive(explorerFileUploadFinished);
	fileStorageTaskHandle = NULL;
	vTaskDelete(NULL);
}

// Sends a list of the content of a directory as JSON file
// requires a GET parameter path for the directory
void explorerHandleListRequest(AsyncWebServerRequest *request) {
#ifdef NO_SDCARD
	request->send(200, "application/json; charset=utf-8", "[]"); // maybe better to send 404 here?
	return;
#endif

	File root;
	bool isRoot = false;
	if (request->hasParam("path")) {
		const AsyncWebParameter *param;
		param = request->getParam("path");
		const char *filePath = param->value().c_str();
		if (strcmp(filePath, "/") == 0) {
			isRoot = true;
		}
		root = gFSystem.open(filePath);
	} else {
		root = gFSystem.open("/");
		isRoot = true;
	}

	if (!root) {
		Log_Println(failedToOpenDirectory, LOGLEVEL_DEBUG);
		return;
	}

	if (!root.isDirectory()) {
		Log_Println(notADirectory, LOGLEVEL_DEBUG);
		return;
	}

	AsyncJsonResponse *response = new AsyncJsonResponse(true);
	JsonArray obj = response->getRoot();

	// For root directory, add volume label as first element if available
	if (isRoot) {
		String volumeLabel = SdCard_GetVolumeLabel();
		if (volumeLabel.length() > 0) {
			JsonObject labelEntry = obj.add<JsonObject>();
			labelEntry["name"] = volumeLabel;
			labelEntry["root"] = "sd";
		}
	}

	bool isDir = false;
	String MyfileName = gFSystem.nextFileName(root, &isDir);
	while (MyfileName != "") {
		// ignore hidden folders, e.g. MacOS spotlight files
		if (!MyfileName.startsWith("/.")) {
			JsonObject entry = obj.add<JsonObject>();
			entry["name"] = MyfileName.substring(MyfileName.lastIndexOf('/') + 1);
			if (isDir) {
				entry["dir"].set(true);
			}
		}
		MyfileName = gFSystem.nextFileName(root, &isDir);
	}
	root.close();

	if (response->overflowed()) {
		// JSON buffer too small for data
		Log_Println(jsonbufferOverflow, LOGLEVEL_ERROR);
		request->send(500);
		return;
	}
	response->setLength();
	request->send(response);
}

bool explorerDeleteDirectory(File dir) {

	File file = dir.openNextFile();
	while (file) {

		if (file.isDirectory()) {
			explorerDeleteDirectory(file);
		} else {
			gFSystem.remove(file);
		}

		file = dir.openNextFile();

		esp_task_wdt_reset();
	}

	return gFSystem.rmdir(dir);
}

// Handles download request of a file
// requires a GET parameter path to the file
void explorerHandleDownloadRequest(AsyncWebServerRequest *request) {
	File file;
	const AsyncWebParameter *param;
	// check has path param
	if (!request->hasParam("path")) {
		Log_Println("DOWNLOAD: No path variable set", LOGLEVEL_ERROR);
		request->send(404);
		return;
	}
	// check file exists on SD card
	param = request->getParam("path");
	const char *filePath = param->value().c_str();
	if (!gFSystem.exists(filePath)) {
		Log_Printf(LOGLEVEL_ERROR, "DOWNLOAD:  File not found on SD card: %s", filePath);
		request->send(404);
		return;
	}
	// check is file and not a directory
	file = gFSystem.open(filePath);
	if (file.isDirectory()) {
		Log_Printf(LOGLEVEL_ERROR, "DOWNLOAD:  Cannot download a directory %s", filePath);
		request->send(404);
		file.close();
		return;
	}

	// ready to serve the file for download.
	String dataType = "application/octet-stream";
	struct fileBlk {
		File dataFile;
	};
	fileBlk *fileObj = new fileBlk;
	fileObj->dataFile = file;
	request->_tempObject = (void *) fileObj;

	AsyncWebServerResponse *response = request->beginResponse(dataType, fileObj->dataFile.size(), [request](uint8_t *buffer, size_t maxlen, size_t index) -> size_t {
		fileBlk *fileObj = (fileBlk *) request->_tempObject;
		size_t thisSize = fileObj->dataFile.read(buffer, maxlen);
		if ((index + thisSize) >= fileObj->dataFile.size()) {
			fileObj->dataFile.close();
			request->_tempObject = NULL;
			delete fileObj;
		}
		return thisSize;
	});
	String filename = String(param->value().c_str());
	response->addHeader("Content-Disposition", "attachment; filename=\"" + filename + "\"");
	request->send(response);
}

// Handles delete request of a file or directory
// requires a GET parameter path to the file or directory
void explorerHandleDeleteRequest(AsyncWebServerRequest *request) {
	File file;
	if (request->hasParam("path")) {
		const AsyncWebParameter *param;
		param = request->getParam("path");
		System_UpdateActivityTimer();
		const char *filePath = param->value().c_str();
		if (gFSystem.exists(filePath)) {
			// stop playback, file to delete might be in use
			Cmd_Action(CMD_STOP);
			file = gFSystem.open(filePath);
			if (file.isDirectory()) {
				if (explorerDeleteDirectory(file)) {
					Log_Printf(LOGLEVEL_INFO, "DELETE:  %s deleted", filePath);
				} else {
					Log_Printf(LOGLEVEL_ERROR, "DELETE:  Cannot delete %s", filePath);
				}
			} else {
				if (gFSystem.remove(filePath)) {
					Log_Printf(LOGLEVEL_INFO, "DELETE:  %s deleted", filePath);
				} else {
					Log_Printf(LOGLEVEL_ERROR, "DELETE:  Cannot delete %s", filePath);
				}
			}
		} else {
			Log_Printf(LOGLEVEL_ERROR, "DELETE:  Path %s does not exist", filePath);
		}
	} else {
		Log_Println("DELETE:  No path variable set", LOGLEVEL_ERROR);
	}
	request->send(200);
	esp_task_wdt_reset();
}

// Handles create request of a directory
// requires a GET parameter path to the new directory
void explorerHandleCreateRequest(AsyncWebServerRequest *request) {
	if (request->hasParam("path")) {
		const AsyncWebParameter *param;
		System_UpdateActivityTimer();
		param = request->getParam("path");
		const char *filePath = param->value().c_str();
		if (gFSystem.mkdir(filePath)) {
			Log_Printf(LOGLEVEL_INFO, "CREATE:  %s created", filePath);
		} else {
			Log_Printf(LOGLEVEL_ERROR, "CREATE:  Cannot create %s", filePath);
		}
	} else {
		Log_Println("CREATE:  No path variable set", LOGLEVEL_ERROR);
	}
	request->send(200);
}

// Handles rename request of a file or directory
// requires a GET parameter srcpath to the old file or directory name
// requires a GET parameter dstpath to the new file or directory name
void explorerHandleRenameRequest(AsyncWebServerRequest *request) {
	if (request->hasParam("srcpath") && request->hasParam("dstpath")) {
		const AsyncWebParameter *srcPath;
		const AsyncWebParameter *dstPath;
		System_UpdateActivityTimer();
		srcPath = request->getParam("srcpath");
		dstPath = request->getParam("dstpath");
		const char *srcFullFilePath = srcPath->value().c_str();
		const char *dstFullFilePath = dstPath->value().c_str();
		if (gFSystem.exists(srcFullFilePath)) {
			if (gFSystem.rename(srcFullFilePath, dstFullFilePath)) {
				Log_Printf(LOGLEVEL_INFO, "RENAME:  %s renamed to %s", srcFullFilePath, dstFullFilePath);
			} else {
				Log_Printf(LOGLEVEL_ERROR, "RENAME:  Cannot rename %s", srcFullFilePath);
			}
		} else {
			Log_Printf(LOGLEVEL_ERROR, "RENAME: Path %s does not exist", srcFullFilePath);
		}
	} else {
		Log_Println("RENAME: No path variable set", LOGLEVEL_ERROR);
	}

	request->send(200);
}

// Handles audio play requests
// requires a GET parameter path to the audio file or directory
// requires a GET parameter playmode
void explorerHandleAudioRequest(AsyncWebServerRequest *request) {
	const AsyncWebParameter *param;
	String playModeString;
	uint32_t playMode;
	if (request->hasParam("path") && request->hasParam("playmode")) {
		if (!System_IsWebControlAllowed()) {
			Log_Println(notAllowedInCurrentMode, LOGLEVEL_NOTICE);
			Web_SendWebsocketData(0, WebsocketCodeType::NotAllowedInCurrentMode);
			request->send(200);
			return;
		}
		param = request->getParam("path");
		const char *filePath = param->value().c_str();
		param = request->getParam("playmode");
		playModeString = param->value();

		playMode = atoi(playModeString.c_str());
		Rfid_ResetLastTag(); // Another playlist is loaded now: re-applying the last tag must reload it, not toggle pause
		AudioPlayer_SetPlaylist(filePath, 0, playMode, 0);
	} else {
		Log_Println("AUDIO: No path variable set", LOGLEVEL_ERROR);
	}

	request->send(200);
}

// Handles track progress requests
void handleTrackProgressRequest(AsyncWebServerRequest *request) {
	String json = "{\"trackProgress\":{";
	json += "\"posPercent\":" + String(gPlayProperties.currentRelPos);
	json += ",\"time\":" + String(AudioPlayer_GetCurrentTime());
	json += ",\"duration\":" + String(AudioPlayer_GetFileDuration());
	json += "}}";
	request->send(200, "application/json", json);
}

void handleGetSavedSSIDs(AsyncWebServerRequest *request) {
	AsyncJsonResponse *response = new AsyncJsonResponse(true);
	JsonArray json_ssids = response->getRoot();
	Wlan_GetSavedNetworks([json_ssids](const WiFiSettings &network) {
		json_ssids.add(network.ssid);
	});

	response->setLength();
	request->send(response);
}

// Map an 802.11 disconnect reason code onto a coarse, user-explainable class.
// The page translates the class into a localized message; the raw code is
// reported alongside for the curious/for support.
static const char *classifyDisconnectReason(uint8_t reason) {
	switch (reason) {
		case 0: // no disconnect event: association held, but no IP arrived
			return "timeout";
		case WIFI_REASON_AUTH_EXPIRE:
		case WIFI_REASON_4WAY_HANDSHAKE_TIMEOUT:
		case WIFI_REASON_GROUP_KEY_UPDATE_TIMEOUT:
		case WIFI_REASON_IE_IN_4WAY_DIFFERS:
		case WIFI_REASON_AUTH_FAIL:
		case WIFI_REASON_HANDSHAKE_TIMEOUT:
			return "wrong_password";
		case WIFI_REASON_NO_AP_FOUND:
		case 210: // NO_AP_FOUND_IN_RSSI_THRESHOLD (IDF >= 5.3)
		case 211: // NO_AP_FOUND_IN_AUTHMODE_THRESHOLD
		case 212: // NO_AP_FOUND_IN_BAND
		case 213: // NO_AP_FOUND_W_COMPATIBLE_SECURITY
			return "not_found";
		case WIFI_REASON_ASSOC_TOOMANY:
		case WIFI_REASON_802_1X_AUTH_FAILED:
		case WIFI_REASON_CIPHER_SUITE_REJECTED:
		case WIFI_REASON_ASSOC_FAIL:
		case WIFI_REASON_CONNECTION_FAIL:
			return "rejected";
		default:
			return "other";
	}
}

// Current WiFi state plus diagnostics of the last failed connection attempt.
// Used by the accesspoint page to tell the user why their credentials didn't
// work instead of silently falling back to the setup AP.
void handleGetWifiStatus(AsyncWebServerRequest *request) {
	AsyncJsonResponse *response = new AsyncJsonResponse();
	JsonObject obj = response->getRoot();

	obj["state"] = Wlan_GetConnectState();
	if (Wlan_IsConnected()) {
		obj["ssid"] = Wlan_GetCurrentSSID();
		obj["ip"] = Wlan_GetIpAddress();
	}

	String failSsid;
	uint8_t failReason;
	if (Wlan_GetLastFailure(failSsid, failReason)) {
		JsonObject fail = obj["last_failure"].to<JsonObject>();
		fail["ssid"] = failSsid;
		fail["reason"] = failReason;
		fail["class"] = classifyDisconnectReason(failReason);
	}

	// live connection test (started via POST /wifitest from the setup page)
	const char *testPhase = Wlan_GetTestPhase();
	if (strcmp(testPhase, "idle") != 0) {
		JsonObject test = obj["test"].to<JsonObject>();
		test["phase"] = testPhase;
		test["ssid"] = Wlan_GetTestSsid();
		if (strcmp(testPhase, "failed") == 0) {
			const uint8_t reason = Wlan_GetTestReason();
			test["reason"] = reason;
			test["class"] = classifyDisconnectReason(reason);
		} else if (strcmp(testPhase, "success") == 0) {
			test["ip"] = Wlan_GetIpAddress();
		}
	}

	response->setLength();
	request->send(response);
}

// Start a live connection test while in AP mode. Body: {"ssid": "..."} —
// the credentials must have been saved via POST /savedSSIDs beforehand.
void handlePostWifiTest(AsyncWebServerRequest *request, JsonVariant &json) {
	const char *ssid = json["ssid"].as<const char *>();
	if (!ssid || !Wlan_StartConnectionTest(ssid)) {
		request->send(400);
		return;
	}
	request->send(200);
}

void handlePostSavedSSIDs(AsyncWebServerRequest *request, JsonVariant &json) {
	WiFiSettings networkSettings;

	networkSettings.ssid = json["ssid"].as<const char *>();
	networkSettings.password = json["pwd"].as<const char *>();

	if (json["static"].as<bool>()) {
		networkSettings.staticIp.addr = json["static_addr"].as<IPAddress>();
		networkSettings.staticIp.subnet = json["static_subnet"].as<IPAddress>();
		networkSettings.staticIp.gateway = json["static_gateway"].as<IPAddress>();
		networkSettings.staticIp.dns1 = json["static_dns1"].as<IPAddress>();
		networkSettings.staticIp.dns2 = json["static_dns2"].as<IPAddress>();
	}

	if (!networkSettings.isValid()) {
		// The data was corrupted, so user error
		request->send(400, "text/plain; charset=utf-8", "error adding network");
		return;
	}

	bool succ = Wlan_AddNetworkSettings(networkSettings);
	if (succ) {
		request->send(200, "text/plain; charset=utf-8", networkSettings.ssid);
	} else {
		request->send(500, "text/plain; charset=utf-8", "error adding network");
	}
}

void handleDeleteSavedSSIDs(AsyncWebServerRequest *request) {
	const AsyncWebParameter *p = request->getParam("ssid");
	const String ssid = p->value();

	bool succ = Wlan_DeleteNetwork(ssid);

	if (succ) {
		request->send(200, "text/plain; charset=utf-8", ssid);
	} else {
		request->send(500, "text/plain; charset=utf-8", "error deleting network");
	}
}

void handleGetActiveSSID(AsyncWebServerRequest *request) {
	AsyncJsonResponse *response = new AsyncJsonResponse();
	JsonObject obj = response->getRoot();

	if (Wlan_IsConnected()) {
		String active = Wlan_GetCurrentSSID();
		obj["active"] = active;
	}

	response->setLength();
	request->send(response);
}

void handleGetWiFiConfig(AsyncWebServerRequest *request) {
	AsyncJsonResponse *response = new AsyncJsonResponse();
	JsonObject obj = response->getRoot();
	bool scanWifiOnStart = gPrefsSettings.getBool("ScanWiFiOnStart", false);

	obj["hostname"] = Wlan_GetHostname();
	obj["scanOnStart"].set(scanWifiOnStart);
	obj["apSSID"] = Wlan_GetApSSID();
	obj["apPassword"] = Wlan_GetApPassword();
	obj["apTimeout"] = Wlan_GetApTimeoutMinutes();

	response->setLength();
	request->send(response);
}

void handlePostWiFiConfig(AsyncWebServerRequest *request, JsonVariant &json) {
	const JsonObject &jsonObj = json.as<JsonObject>();

	// always perform perform a WiFi scan on startup?
	bool alwaysScan = jsonObj["scanOnStart"];
	gPrefsSettings.putBool("ScanWiFiOnStart", alwaysScan);

	// hostname
	String strHostname = jsonObj["hostname"];
	if (!Wlan_ValidateHostname(strHostname)) {
		Log_Println("hostname validation failed", LOGLEVEL_ERROR);
		request->send(400, "text/plain; charset=utf-8", "hostname validation failed");
		return;
	}

	// ESPuino's own access-point (used as fallback when no known WiFi is available)
	String strApSSID = jsonObj["apSSID"];
	if (!Wlan_ValidateApSSID(strApSSID)) {
		Log_Println("AP SSID validation failed", LOGLEVEL_ERROR);
		request->send(400, "text/plain; charset=utf-8", "AP SSID validation failed");
		return;
	}
	String strApPassword = jsonObj["apPassword"];
	if (!Wlan_ValidateApPassword(strApPassword)) {
		Log_Println("AP password validation failed", LOGLEVEL_ERROR);
		request->send(400, "text/plain; charset=utf-8", "AP password validation failed");
		return;
	}
	// minutes the AP stays open before auto-closing; 0 = never close automatically
	uint32_t apTimeoutMinutes = jsonObj["apTimeout"] | 5;

	bool succ = Wlan_SetHostname(strHostname);
	succ = succ && Wlan_SetApSSID(strApSSID);
	succ = succ && Wlan_SetApPassword(strApPassword);
	succ = succ && Wlan_SetApTimeoutMinutes(apTimeoutMinutes);
	if (succ) {
		Log_Println("WiFi configuration saved.", LOGLEVEL_NOTICE);
		request->send(200, "text/plain; charset=utf-8", strHostname);
	} else {
		Log_Println("error setting hostname", LOGLEVEL_ERROR);
		request->send(500, "text/plain; charset=utf-8", "error setting hostname");
	}
}

static bool tagIdToJSON(const String tagId, JsonObject entry) {
	String s = gPrefsRfid.getString(tagId.c_str(), ""); // Try to lookup rfidId in NVS
	if (s.length() == 0 || s == "-1") {
		return false;
	}
	char _file[256] = {0};
	uint32_t _lastPlayPos = 0;
	uint16_t _trackLastPlayed = 0;
	uint32_t _mode = 1;

	char s_buf[512];
	strncpy(s_buf, s.c_str(), sizeof(s_buf) - 1);
	s_buf[sizeof(s_buf) - 1] = '\0';

	char *token = strtok(s_buf, stringDelimiter);
	uint8_t i = 1;
	while (token != NULL) { // Try to extract data from string after lookup
		if (i == 1) {
			strncpy(_file, token, sizeof(_file) - 1);
		} else if (i == 2) {
			_lastPlayPos = strtoul(token, NULL, 10);
		} else if (i == 3) {
			_mode = strtoul(token, NULL, 10);
		} else if (i == 4) {
			_trackLastPlayed = strtoul(token, NULL, 10);
		}
		i++;
		token = strtok(NULL, stringDelimiter);
	}
	entry["id"] = tagId;
	if (_mode >= 100) {
		entry["modId"] = _mode;
	} else {
		entry["fileOrUrl"] = _file;
		entry["playMode"] = _mode;
		entry["lastPlayPos"] = _lastPlayPos;
		entry["trackLastPlayed"] = _trackLastPlayed;
	}
	return true;
}

// callback for writing a NVS entry to list
bool DumpNvsToArrayCallback(const char *key, void *data) {
	std::vector<String> *keys = (std::vector<String> *) data;
	keys->push_back(key);
	return true;
}

static String tagIdToJsonStr(const char *key, const bool nameOnly) {
	if (nameOnly) {
		return "\"" + String(key) + "\"";
	} else {
		JsonDocument doc;
		JsonObject entry = doc[key].to<JsonObject>();
		if (!tagIdToJSON(key, entry)) {
			return "";
		}
		String serializedJsonString;
		serializeJson(entry, serializedJsonString);
		return serializedJsonString;
	}
}

// Handles rfid-assignments requests (GET)
// /rfid returns an array of tag-ids and details. Optional GET param "id" to list only a single assignment.
// /rfid/ids-only returns an array of tag-id keys
static void handleGetRFIDRequest(AsyncWebServerRequest *request) {

	String tagId = "";

	if (request->hasParam("id")) {
		tagId = request->getParam("id")->value();
	}

	if ((tagId != "") && gPrefsRfid.isKey(tagId.c_str())) {
		// return single RFID entry with details
		String json = tagIdToJsonStr(tagId.c_str(), false);
		request->send(200, "application/json", json);
		return;
	}
	// get tag details or just an array of id's
	bool idsOnly = request->hasParam("ids-only");

	std::vector<String> nvsKeys {};
	nvsKeys.clear();
	// Dumps all RFID-keys from NVS into key array
	listNVSKeys("rfidTags", &nvsKeys, DumpNvsToArrayCallback);
	if (nvsKeys.size() == 0) {
		// no entries
		request->send(200, "application/json", "[]");
		return;
	}
	// construct chunked repsonse
	AsyncWebServerResponse *response = request->beginChunkedResponse("application/json",
		[nvsKeys = std::move(nvsKeys), idsOnly, nvsIndex = size_t(0)](uint8_t *buffer, size_t maxLen, size_t index) mutable -> size_t {
			maxLen = maxLen >> 1; // some sort of bug with actual size available, reduce the len
			size_t len = 0;
			String json;

			if (nvsIndex == 0) {
				// start, write first tag
				json = tagIdToJsonStr(nvsKeys[nvsIndex].c_str(), idsOnly);
				if (json.length() >= maxLen) {
					Log_Println("/rfid: Buffer too small", LOGLEVEL_ERROR);
					return len;
				}
				len += snprintf(((char *) buffer), maxLen - len, "[%s", json.c_str());
				nvsIndex++;
			}
			while (nvsIndex < nvsKeys.size()) {
				// write tags as long we have enough room
				json = tagIdToJsonStr(nvsKeys[nvsIndex].c_str(), idsOnly);
				if ((len + json.length()) >= maxLen) {
					break;
				}
				len += snprintf(((char *) buffer + len), maxLen - len, ",%s", json.c_str());
				nvsIndex++;
			}
			if (nvsIndex == nvsKeys.size()) {
				// finish
				len += snprintf(((char *) buffer + len), maxLen - len, "]");
				nvsIndex++;
			}
			return len;
		});
	request->send(response);
}

static void handlePostRFIDRequest(AsyncWebServerRequest *request, JsonVariant &json) {
	const JsonObject &jsonObj = json.as<JsonObject>();

	String tagId = jsonObj["id"];
	if (tagId.isEmpty()) {
		Log_Println("/rfid (POST): Missing tag id", LOGLEVEL_ERROR);
		request->send(500, "text/plain; charset=utf-8", "/rfid (POST): Missing tag id");
		return;
	}
	String fileOrUrl = jsonObj["fileOrUrl"];
	if (fileOrUrl.isEmpty()) {
		fileOrUrl = "0";
	}
	const char *_fileOrUrlAscii = fileOrUrl.c_str();
	uint8_t _playModeOrModId;
	if (jsonObj["modId"].is<u_int8_t>()) {
		_playModeOrModId = jsonObj["modId"];
	} else {
		_playModeOrModId = jsonObj["playMode"];
	}
	if (_playModeOrModId <= 0) {
		Log_Println("/rfid (POST): Invalid playMode or modId", LOGLEVEL_ERROR);
		request->send(500, "text/plain; charset=utf-8", "/rfid (POST): Invalid playMode or modId");
		return;
	}
	char rfidString[275];
	snprintf(rfidString, sizeof(rfidString) / sizeof(rfidString[0]), "%s%s%s0%s%u%s0", stringDelimiter, _fileOrUrlAscii, stringDelimiter, stringDelimiter, _playModeOrModId, stringDelimiter);
	gPrefsRfid.putString(tagId.c_str(), rfidString);
	Rfid_ResetLastTag(); // The tag means something else now: make sure re-applying it is not deduped away

	String s = gPrefsRfid.getString(tagId.c_str(), "-1");
	if (s.compareTo(rfidString)) {
		request->send(500, "text/plain; charset=utf-8", "/rfid (POST): cannot save assignment to NVS");
		return;
	}
	Web_DumpNvsToSd("rfidTags", backupFile); // Store backup-file every time when a new rfid-tag is programmed
	// return the new/modified RFID assignment
	AsyncJsonResponse *response = new AsyncJsonResponse(false);
	JsonObject obj = response->getRoot();
	tagIdToJSON(tagId, obj);
	response->setLength();
	request->send(response);
}

static void handleDeleteRFIDRequest(AsyncWebServerRequest *request) {
	String tagId = "";
	if (request->hasParam("id")) {
		tagId = request->getParam("id")->value();
	}
	if (tagId.isEmpty()) {
		Log_Println("/rfid (DELETE): Missing tag id", LOGLEVEL_ERROR);
		request->send(500, "text/plain; charset=utf-8", "/rfid (DELETE): Missing tag id");
		return;
	}
	if (gPrefsRfid.isKey(tagId.c_str())) {
		if (tagId.equals(gCurrentRfidTagId)) {
			// stop playback, tag to delete is in use
			Cmd_Action(CMD_STOP);
		}
		// MediaHub cascade (concept §13.1): the NVS entry's path field starts
		// with "mediahub://" for MediaHub-managed cards. Checked - and cleaned
		// up - before the NVS entry itself is removed below: if the cleanup
		// fails, the NVS entry is deliberately left in place so a retry can
		// still recognize the card as MediaHub-managed and try again. Removing
		// the NVS entry unconditionally would lose that marker on a partial
		// failure, orphaning the local media/manifest files forever.
		const String nvsValue = gPrefsRfid.getString(tagId.c_str(), "");
		const bool isMediaHubCard = nvsValue.startsWith(String(stringDelimiter) + MediaHub_PathPrefix);
		const bool mediaHubCleanupOk = !isMediaHubCard || MediaHub_DeleteCard(tagId.c_str());

		if (mediaHubCleanupOk && gPrefsRfid.remove(tagId.c_str())) {
			Rfid_ResetLastTag(); // The tag means nothing now: make sure re-applying it is not deduped away
			Log_Printf(LOGLEVEL_INFO, "/rfid (DELETE): tag %s removed successfuly", tagId);
			request->send(200, "text/plain; charset=utf-8", tagId + " removed successfuly");
		} else {
			Log_Println("/rfid (DELETE):error removing tag from NVS", LOGLEVEL_ERROR);
			request->send(500, "text/plain; charset=utf-8", "error removing tag from NVS");
		}
	} else {
		Log_Printf(LOGLEVEL_DEBUG, "/rfid (DELETE): tag %s not exists", tagId);
		request->send(404, "text/plain; charset=utf-8", "error removing tag from NVS: Tag not exists");
	}
}

// Registered MediaHub servers (concept §5.1): pure Web-UI enrollment
// convenience, never read by the runtime playback flow.
static void handleGetMediaHubServers(AsyncWebServerRequest *request) {
	AsyncJsonResponse *response = new AsyncJsonResponse(true);
	JsonArray arr = response->getRoot();
	for (const MediaHubServer &server : MediaHub_GetServers()) {
		JsonObject obj = arr.add<JsonObject>();
		obj["name"] = server.name;
		obj["hostPort"] = server.hostPort;
		obj["https"] = server.https;
	}
	response->setLength();
	request->send(response);
}

static void handlePostMediaHubServers(AsyncWebServerRequest *request, JsonVariant &json) {
	const char *name = json["name"].as<const char *>();
	const char *hostPort = json["hostPort"].as<const char *>();
	const bool https = json["https"] | false;
	if (!name || !hostPort || strlen(name) == 0 || strlen(hostPort) == 0) {
		request->send(400, "text/plain; charset=utf-8", "error adding media server");
		return;
	}
	if (MediaHub_SaveServer(name, hostPort, https)) {
		request->send(200, "text/plain; charset=utf-8", name);
	} else {
		request->send(500, "text/plain; charset=utf-8", "error adding media server");
	}
}

static void handleDeleteMediaHubServers(AsyncWebServerRequest *request) {
	const AsyncWebParameter *p = request->getParam("name");
	const String name = p->value();
	if (MediaHub_DeleteServer(name)) {
		request->send(200, "text/plain; charset=utf-8", name);
	} else {
		request->send(500, "text/plain; charset=utf-8", "error deleting media server");
	}
}
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
