biologist79/ESPuino/src/values.h

#pragma once

// Operation Mode
#define OPMODE_NORMAL			0 // Normal mode
#define OPMODE_BLUETOOTH_SINK	1 // Bluetooth sink mode. Player acts as as bluetooth speaker. WiFi is deactivated. Music from SD and webstreams can't be played.
#define OPMODE_BLUETOOTH_SOURCE 2 // Bluetooth sourcemode. Player sennds audio to bluetooth speaker/headset. WiFi is deactivated. Music from SD and webstreams can't be played.

// Track-Control
#define NO_ACTION	   0 // Dummy to unset track-control-command
#define STOP		   1 // Stop play
#define PLAY		   2 // Start play (currently not used)
#define PAUSEPLAY	   3 // Pause/play
#define NEXTTRACK	   4 // Next track of playlist
#define PREVIOUSTRACK  5 // Previous track of playlist
#define FIRSTTRACK	   6 // First track of playlist
#define LASTTRACK	   7 // Last track of playlist
#define NEXTFOLDER	   8 // Next folder (recursive mode only)
#define PREVIOUSFOLDER 9 // Previous folder (recursive mode only)

// Playmodes
#define NO_PLAYLIST												  0 // If no playlist is active
#define SINGLE_TRACK											  1 // Play a single track
#define SINGLE_TRACK_LOOP										  2 // Play a single track in infinite-loop
#define SINGLE_TRACK_OF_DIR_RANDOM								  12 // Play a single track of a directory and fall asleep subsequently
#define AUDIOBOOK												  3 // Single track or tracks of single folder, can save last play-position
#define AUDIOBOOK_LOOP											  4 // Single track or tracks of single folder as infinite-loop, can save last play-position
#define AUDIOBOOK_RECURSIVE										  16 // Single track or track of single folder or folder recursive, can save last play-position
#define ALL_TRACKS_OF_DIR_SORTED								  5 // Play all files of a directory (sorted)
#define ALL_TRACKS_OF_DIR_RANDOM								  6 // Play all files of a directory (randomized)
#define ALL_TRACKS_OF_DIR_RANDOM_RECURSIVE						  17 // Play all files of a directory and subdirectories (randomized)
#define ALL_TRACKS_OF_DIR_SORTED_LOOP							  7 // Play all files of a directory (sorted) in infinite-loop
#define ALL_TRACKS_OF_DIR_RANDOM_LOOP							  9 // Play all files of a directory (randomized) in infinite-loop
#define ALL_TRACKS_OF_DIR_SORTED_RECURSIVE						  15 // Like AUDIOBOOK_RECURSIVE, but without saving last play-position
#define RANDOM_SUBDIRECTORY_OF_DIRECTORY						  13 // Picks a random subdirectory from a given directory and do ALL_TRACKS_OF_DIR_SORTED
#define RANDOM_SUBDIRECTORY_OF_DIRECTORY_ALL_TRACKS_OF_DIR_RANDOM 14 // Picks a random subdirectory from a given directory and do ALL_TRACKS_OF_DIR_RANDOM
#define WEBSTREAM												  8 // Play webradio-stream
#define LOCAL_M3U												  11 // Plays items (webstream or files) with addresses/paths from a local m3u-file
#define BUSY													  10 // Used if playlist is created
#define MEDIAHUB												  18 // Card is managed by an external MediaHub (see mediahub-konzept.md); real playMode comes from its manifest, not from here

// RFID-modifcation-types
#define CMD_NOTHING						 0 // Do Nothing
#define CMD_LOCK_BUTTONS_MOD			 100 // Locks all buttons and rotary encoder
#define CMD_SLEEP_TIMER_MOD_15			 101 // Puts uC into deepsleep after 15 minutes + LED-DIMM
#define CMD_SLEEP_TIMER_MOD_30			 102 // Puts uC into deepsleep after 30 minutes + LED-DIMM
#define CMD_SLEEP_TIMER_MOD_60			 103 // Puts uC into deepsleep after 60 minutes + LED-DIMM
#define CMD_SLEEP_TIMER_MOD_120			 104 // Puts uC into deepsleep after 120 minutes + LED-DIMM
#define CMD_SLEEP_AFTER_END_OF_TRACK	 105 // Puts uC into deepsleep after track is finished + LED-DIMM
#define CMD_SLEEP_AFTER_END_OF_PLAYLIST	 106 // Puts uC into deepsleep after playlist is finished + LED-DIMM
#define CMD_SLEEP_AFTER_5_TRACKS		 107 // Puts uC into deepsleep after five tracks + LED-DIMM
#define CMD_REPEAT_PLAYLIST				 110 // Changes active playmode to endless-loop (for a playlist)
#define CMD_REPEAT_TRACK				 111 // Changes active playmode to endless-loop (for a single track)
#define CMD_DIMM_LEDS_NIGHTMODE			 120 // Changes LED-brightness
#define CMD_TOGGLE_WIFI_STATUS			 130 // Toggles WiFi-status
#define CMD_TOGGLE_BLUETOOTH_SINK_MODE	 140 // Toggles Normal/Bluetooth sink Mode
#define CMD_TOGGLE_BLUETOOTH_SOURCE_MODE 141 // Toggles Normal/Bluetooth source Mode
#define CMD_TOGGLE_MODE					 142 // Toggles Normal => Bluetooth sink => Bluetooth source => Normal Mode
#define CMD_ENABLE_FTP_SERVER			 150 // Enables FTP-server
#define CMD_TELL_IP_ADDRESS				 151 // Command: ESPuino announces its IP-address via speech
#define CMD_TELL_CURRENT_TIME			 152 // Command: ESPuino announces current time via speech
#define CMD_TOGGLE_AMBIENT_LIGHT		 153 // Command: toggles the ambient light
#define CMD_BRIGHTNESS_UP				 154 // Command: raise LED-brightness by one step
#define CMD_BRIGHTNESS_DOWN				 155 // Command: lower LED-brightness by one step

#define CMD_PLAYPAUSE	   170 // Command: play/pause
#define CMD_PREVTRACK	   171 // Command: previous track
#define CMD_NEXTTRACK	   172 // Command: next track
#define CMD_FIRSTTRACK	   173 // Command: first track
#define CMD_LASTTRACK	   174 // Command: last track
#define CMD_VOLUMEINIT	   175 // Command: set volume to initial value
#define CMD_VOLUMEUP	   176 // Command: increase volume by 1
#define CMD_VOLUMEDOWN	   177 // Command: lower volume by 1
#define CMD_MEASUREBATTERY 178 // Command: Measure battery-voltage
#define CMD_SLEEPMODE	   179 // Command: Go to deepsleep
#define CMD_SEEK_FORWARDS  180 // Command: jump forwards (seconds per press: web interface, NVS "jumpOffset")
#define CMD_SEEK_BACKWARDS 181 // Command: jump backwards (seconds per press: web interface, NVS "jumpOffset")
#define CMD_STOP		   182 // Command: stops playback
#define CMD_RESTARTSYSTEM  183 // Command: restart System
#define CMD_NEXTFOLDER	   184 // Command: jump forwards to next folder (only applicable for recursive playmodes)
#define CMD_PREVFOLDER	   185 // Command: jump forwards to previous folder (only applicable for recursive playmodes)
#define CMD_SEEK_PREVIEW   186 // Command: rotary-gesture-only. Turning previews a target position (LED cursor); commits on release/idle instead of jumping immediately

#define CMD_VIRTUAL_RFID_CARD_01 241 // Command: Virtual RFID-Card 900000000001
#define CMD_VIRTUAL_RFID_CARD_02 242 // Command: Virtual RFID-Card 900000000002
#define CMD_VIRTUAL_RFID_CARD_03 243 // Command: Virtual RFID-Card 900000000003
#define CMD_VIRTUAL_RFID_CARD_04 244 // Command: Virtual RFID-Card 900000000004
#define CMD_VIRTUAL_RFID_CARD_05 245 // Command: Virtual RFID-Card 900000000005
#define CMD_VIRTUAL_RFID_CARD_06 246 // Command: Virtual RFID-Card 900000000006
#define CMD_VIRTUAL_RFID_CARD_07 247 // Command: Virtual RFID-Card 900000000007
#define CMD_VIRTUAL_RFID_CARD_08 248 // Command: Virtual RFID-Card 900000000008
#define CMD_VIRTUAL_RFID_CARD_09 249 // Command: Virtual RFID-Card 900000000009
#define CMD_VIRTUAL_RFID_CARD_10 250 // Command: Virtual RFID-Card 900000000010

// Seek step sizes (seconds). These are internal defaults only: they seed the matching
// web-interface settings before their first save and are read from NVS afterwards.
// Change the values in the web interface, not here.
#define SEEK_STEP_BUTTON_DEFAULT 30 // NVS "jumpOffset":  per press of CMD_SEEK_FORWARDS / CMD_SEEK_BACKWARDS
#define SEEK_STEP_ROTARY_DEFAULT 10 // NVS "rotSeekStep": per encoder detent when a turn action is mapped to seek.
									// Deliberately smaller than the button step: a flick of the encoder is many
									// detents at once, so reusing the button step there would scrub minutes.

// Repeat-Modes
#define NO_REPEAT		 0 // No repeat
#define TRACK			 1 // Repeat current track (infinite loop)
#define PLAYLIST		 2 // Repeat whole playlist (infinite loop)
#define TRACK_N_PLAYLIST 3 // Repeat both (infinite loop)

// Seek-modes
#define SEEK_NORMAL		 0 // Normal play
#define SEEK_FORWARDS	 1 // Seek forwards
#define SEEK_BACKWARDS	 2 // Seek backwards
#define SEEK_POS_PERCENT 3 // Seek to position (0-100)

// TTS
#define TTS_NONE		 0 // Do nothng (IDLE)
#define TTS_IP_ADDRESS	 1 // Tell IP-address
#define TTS_CURRENT_TIME 2 // Tell current time

// supported languages
#define DE 1
#define EN 2
#define FR 3

// Virtual RFID Cards
#define VIRTUAL_RFID_CARD_01 "900000000001"
#define VIRTUAL_RFID_CARD_02 "900000000002"
#define VIRTUAL_RFID_CARD_03 "900000000003"
#define VIRTUAL_RFID_CARD_04 "900000000004"
#define VIRTUAL_RFID_CARD_05 "900000000005"
#define VIRTUAL_RFID_CARD_06 "900000000006"
#define VIRTUAL_RFID_CARD_07 "900000000007"
#define VIRTUAL_RFID_CARD_08 "900000000008"
#define VIRTUAL_RFID_CARD_09 "900000000009"
#define VIRTUAL_RFID_CARD_10 "900000000010"

// Debug
#define PRINT_TASK_STATS 199 // Prints task stats for debugging, needs CONFIG_FREERTOS_USE_TRACE_FACILITY=y and CONFIG_FREERTOS_GENERATE_RUN_TIME_STATS=y in sdkconfig.defaults
