biologist79/ESPuino/src/Bluetooth.cpp

#include <Arduino.h>
#include "settings.h"

#include "Bluetooth.h"

#include "Common.h"
#include "Log.h"
#include "RotaryEncoder.h"
#include "System.h"
#include "Web.h"
#include "esp_bt_main.h"

#include <AudioPlayer.h>
#include <algorithm>
#include <atomic>

#ifdef BLUETOOTH_ENABLE
	#include "BluetoothA2DPCommon.h"
	#include "BluetoothA2DPSink.h"
	#include "BluetoothA2DPSource.h"
	#include "esp_bt.h"
	#include "esp_bt_defs.h"
	#include "esp_gap_bt_api.h"
	#include "esp_heap_caps.h"
	#if (defined(ESP_ARDUINO_VERSION_MAJOR) && (ESP_ARDUINO_VERSION_MAJOR >= 3))
		#include "ESP_I2S.h"
I2SClass i2s;
	#endif
#endif

#ifdef BLUETOOTH_ENABLE
	#define BLUETOOTH_A2DP_VOLUME_MAX 127u
	#define BLUETOOTH_A2DP_VOLUME_MIN 0u

// Timeout matches ESP-IDF inquiry duration: 10 slots * 1.28s = 12.8s
static constexpr uint32_t SCAN_TIMEOUT_MS = 13000u;
static constexpr uint32_t SCAN_TIMEOUT_GUARD_MS = 2000u;
static constexpr size_t AUDIO_SOURCE_RINGBUFFER_SIZE = 262144; // 256KB

BluetoothA2DPSink *a2dp_sink;
BluetoothA2DPSource *a2dp_source;
std::vector<ScannedBluetoothDevice> scannedDevices;
static std::atomic<bool> scanInProgress = false;
static uint32_t scanStartTimestamp = 0;
static esp_bd_addr_t pendingConnectAddress = {0};
static char pendingConnectName[ESP_BT_GAP_MAX_BDNAME_LEN + 1] = {0};
static std::atomic<bool> pendingConnect = false;
static portMUX_TYPE pendingConnectMux = portMUX_INITIALIZER_UNLOCKED;
RingbufHandle_t audioSourceRingBuffer;
static std::atomic<bool> bluetoothSourceConnected = false;
String btDeviceName;
static portMUX_TYPE scannedDevicesMux = portMUX_INITIALIZER_UNLOCKED;
// Suppresses auto-connect via scan_bluetooth_device_callback while a manual
// connect is pending (i.e. user picked a device from a scan result).
static std::atomic<bool> manualConnectPending = false;
// True only while disconnecting the currently connected peer so a queued manual
// connection can start. That expected disconnect must not consume a retry.
static std::atomic<bool> manualDisconnectPending = false;

// Track whether we registered our interceptor so we always restore correctly.
static std::atomic<bool> interceptorRegistered = false;

// One targeted GAP remote-name lookup may be active for the currently connected
// peer. The address and pending flag are updated together under the mux so a
// completion event can never be associated with a different connection.
static std::atomic<bool> peerNameLookupPending = false;
static esp_bd_addr_t peerNameLookupAddress = {0};
static portMUX_TYPE peerNameLookupMux = portMUX_INITIALIZER_UNLOCKED;

// Peer address/name cached for the currently connected A2DP source device.
static esp_bd_addr_t cachedPeerAddress = {0};
static char cachedPeerName[ESP_BT_GAP_MAX_BDNAME_LEN + 1] = {0};
static portMUX_TYPE cachedPeerAddressMux = portMUX_INITIALIZER_UNLOCKED;

// Address/name of the peer that ESPuino explicitly selected for the next
// connection.  ESP32-A2DP's get_last_peer_address() is not updated by every
// connect_to(address) path, so the selected target is the authoritative source
// for manual connections and for auto-connect decisions made by our callback.
static esp_bd_addr_t connectionTargetAddress = {0};
static char connectionTargetName[ESP_BT_GAP_MAX_BDNAME_LEN + 1] = {0};
static bool connectionTargetValid = false;
static portMUX_TYPE connectionTargetMux = portMUX_INITIALIZER_UNLOCKED;

// Returns true if addr is non-zero (i.e. a valid BT address).
static inline bool isValidBdAddr(const esp_bd_addr_t addr) {
	for (int i = 0; i < ESP_BD_ADDR_LEN; i++) {
		if (addr[i] != 0) {
			return true;
		}
	}
	return false;
}

// Returns true when a string is a canonical Bluetooth MAC address.
// Such a value is a connection target, not a friendly device name.
static bool isMacAddressString(const char *value) {
	if (value == nullptr || strlen(value) != 17) {
		return false;
	}

	esp_bd_addr_t parsed = {0};
	const int parsedParts = sscanf(value, "%hhX:%hhX:%hhX:%hhX:%hhX:%hhX",
		&parsed[0], &parsed[1], &parsed[2], &parsed[3], &parsed[4], &parsed[5]);
	return parsedParts == 6;
}

static bool isFriendlyPeerName(const char *value) {
	return value != nullptr && value[0] != '\0'
		&& strcmp(value, "Unknown") != 0
		&& strcmp(value, "Connected Device") != 0
		&& !isMacAddressString(value);
}

static void Bluetooth_SetConnectionTarget(const esp_bd_addr_t address, const char *name) {
	const bool validAddress = isValidBdAddr(address);
	char friendlyName[ESP_BT_GAP_MAX_BDNAME_LEN + 1] = {0};
	if (isFriendlyPeerName(name)) {
		strncpy(friendlyName, name, ESP_BT_GAP_MAX_BDNAME_LEN);
		friendlyName[ESP_BT_GAP_MAX_BDNAME_LEN] = '\0';
	}

	portENTER_CRITICAL(&connectionTargetMux);
	memcpy(connectionTargetAddress, address, ESP_BD_ADDR_LEN);
	strncpy(connectionTargetName, friendlyName, ESP_BT_GAP_MAX_BDNAME_LEN);
	connectionTargetName[ESP_BT_GAP_MAX_BDNAME_LEN] = '\0';
	connectionTargetValid = validAddress;
	portEXIT_CRITICAL(&connectionTargetMux);
}

static bool Bluetooth_GetConnectionTarget(esp_bd_addr_t address, char *name, size_t nameSize) {
	bool valid = false;
	portENTER_CRITICAL(&connectionTargetMux);
	valid = connectionTargetValid;
	if (valid) {
		memcpy(address, connectionTargetAddress, ESP_BD_ADDR_LEN);
		if (name != nullptr && nameSize > 0) {
			strncpy(name, connectionTargetName, nameSize - 1);
			name[nameSize - 1] = '\0';
		}
	}
	portEXIT_CRITICAL(&connectionTargetMux);
	return valid;
}

static void Bluetooth_ClearConnectionTarget() {
	portENTER_CRITICAL(&connectionTargetMux);
	memset(connectionTargetAddress, 0, ESP_BD_ADDR_LEN);
	connectionTargetName[0] = '\0';
	connectionTargetValid = false;
	portEXIT_CRITICAL(&connectionTargetMux);
}

// ── connect-retry state ───────────────────────────────────────────────────
static constexpr uint8_t CONNECT_MAX_RETRIES = 3u;
static constexpr uint32_t CONNECT_RETRY_DELAY_MS = 1500u;
static uint8_t connectRetryCount = 0;
static uint32_t connectRetryTimestamp = 0;
static bool connectRetryPending = false;
static esp_bd_addr_t connectRetryAddress = {0};
#endif

#ifdef BLUETOOTH_ENABLE
const char *getType() {
	if (System_GetOperationMode() == OPMODE_BLUETOOTH_SINK) {
		return "sink";
	} else {
		return "source";
	}
}
#endif

#ifdef BLUETOOTH_ENABLE
static void Bluetooth_Source_FlushRingbuffer(void) {
	if (!audioSourceRingBuffer) {
		return;
	}
	size_t bytesRead = 0;
	uint8_t *item = nullptr;
	while ((item = static_cast<uint8_t *>(xRingbufferReceiveUpTo(audioSourceRingBuffer, &bytesRead, 0, SIZE_MAX))) != nullptr) {
		vRingbufferReturnItem(audioSourceRingBuffer, item);
	}
}
#endif

#ifdef BLUETOOTH_ENABLE
// Forward declarations
static void Bluetooth_StopScan();
static void Bluetooth_RestoreLibraryCallback();
static void Bluetooth_RequestPeerName(const esp_bd_addr_t address);
static void Bluetooth_CancelPeerNameLookup();
#endif

#ifdef BLUETOOTH_ENABLE
extern "C" void ccall_app_gap_callback(esp_bt_gap_cb_event_t event, esp_bt_gap_cb_param_t *param);

static void gap_callback_interceptor(esp_bt_gap_cb_event_t event, esp_bt_gap_cb_param_t *param) {
	if (event == ESP_BT_GAP_DISC_RES_EVT) {
		// Accept discovery results regardless of scanInProgress so that results
		// arriving in the brief window between natural stop and flag-clear are
		// not silently dropped.
		char ssid[ESP_BT_GAP_MAX_BDNAME_LEN + 1] = {0};
		esp_bd_addr_t bda;
		memcpy(bda, param->disc_res.bda, ESP_BD_ADDR_LEN);
		int rssi = -129;

		for (int i = 0; i < param->disc_res.num_prop; i++) {
			esp_bt_gap_dev_prop_t *p = param->disc_res.prop + i;
			if (p->type == ESP_BT_GAP_DEV_PROP_BDNAME && p->len > 0) {
				size_t len = (p->len > ESP_BT_GAP_MAX_BDNAME_LEN) ? ESP_BT_GAP_MAX_BDNAME_LEN : p->len;
				memcpy(ssid, p->val, len);
				ssid[len] = '\0';
			} else if (p->type == ESP_BT_GAP_DEV_PROP_EIR) {
				uint8_t name_len = 0;
				uint8_t *name_ptr = esp_bt_gap_resolve_eir_data((uint8_t *) p->val, ESP_BT_EIR_TYPE_CMPL_LOCAL_NAME, &name_len);
				if (!name_ptr) {
					name_ptr = esp_bt_gap_resolve_eir_data((uint8_t *) p->val, ESP_BT_EIR_TYPE_SHORT_LOCAL_NAME, &name_len);
				}
				if (name_ptr && name_len > 0) {
					size_t len = (name_len > ESP_BT_GAP_MAX_BDNAME_LEN) ? ESP_BT_GAP_MAX_BDNAME_LEN : name_len;
					memcpy(ssid, name_ptr, len);
					ssid[len] = '\0';
				}
			} else if (p->type == ESP_BT_GAP_DEV_PROP_RSSI) {
				rssi = *(int8_t *) (p->val);
			}
		}

		bool requestRemoteName = false;
		portENTER_CRITICAL_ISR(&scannedDevicesMux);
		ScannedBluetoothDevice *existing = nullptr;
		for (auto &d : scannedDevices) {
			if (memcmp(d.address, bda, ESP_BD_ADDR_LEN) == 0) {
				existing = &d;
				break;
			}
		}

		if (existing) {
			if (strlen(ssid) > 0
				&& (strcmp(existing->name, "Unknown") == 0
					|| strcmp(existing->name, "Connected Device") == 0
					|| isMacAddressString(existing->name))) {
				strncpy(existing->name, ssid, ESP_BT_GAP_MAX_BDNAME_LEN);
				existing->name[ESP_BT_GAP_MAX_BDNAME_LEN] = '\0';
			} else if (strlen(ssid) == 0 && !isFriendlyPeerName(existing->name)) {
				requestRemoteName = true;
			}
			existing->rssi = rssi;
		} else {
			ScannedBluetoothDevice device;
			const char *name = (strlen(ssid) > 0) ? ssid : "Unknown";
			strncpy(device.name, name, ESP_BT_GAP_MAX_BDNAME_LEN);
			device.name[ESP_BT_GAP_MAX_BDNAME_LEN] = '\0';
			memcpy(device.address, bda, ESP_BD_ADDR_LEN);
			device.rssi = rssi;
			scannedDevices.push_back(device);
			requestRemoteName = (strlen(ssid) == 0);
		}
		portEXIT_CRITICAL_ISR(&scannedDevicesMux);

		// Keep stack calls outside the spinlock. This lookup is scoped to an
		// active discovery scan and therefore uses the already installed interceptor.
		if (requestRemoteName) {
			esp_bt_gap_read_remote_name(bda);
		}

	} else if (event == ESP_BT_GAP_READ_REMOTE_NAME_EVT) {
		const bool success = (param->read_rmt_name.stat == ESP_BT_STATUS_SUCCESS);
		char resolvedName[ESP_BT_GAP_MAX_BDNAME_LEN + 1] = {0};
		if (success) {
			strncpy(resolvedName, (char *) param->read_rmt_name.rmt_name, ESP_BT_GAP_MAX_BDNAME_LEN);
			resolvedName[ESP_BT_GAP_MAX_BDNAME_LEN] = '\0';

			// Keep scan results up to date as before.
			portENTER_CRITICAL_ISR(&scannedDevicesMux);
			for (auto &d : scannedDevices) {
				if (memcmp(d.address, param->read_rmt_name.bda, ESP_BD_ADDR_LEN) == 0) {
					if (!isFriendlyPeerName(d.name) && isFriendlyPeerName(resolvedName)) {
						strncpy(d.name, resolvedName, ESP_BT_GAP_MAX_BDNAME_LEN);
						d.name[ESP_BT_GAP_MAX_BDNAME_LEN] = '\0';
					}
					break;
				}
			}
			portEXIT_CRITICAL_ISR(&scannedDevicesMux);
		}

		// Complete a targeted lookup only when the result belongs to exactly the
		// peer we requested. This is independent from configured btDeviceName.
		bool completesPeerLookup = false;
		portENTER_CRITICAL_ISR(&peerNameLookupMux);
		if (peerNameLookupPending
			&& memcmp(peerNameLookupAddress, param->read_rmt_name.bda, ESP_BD_ADDR_LEN) == 0) {
			memset(peerNameLookupAddress, 0, ESP_BD_ADDR_LEN);
			peerNameLookupPending = false;
			completesPeerLookup = true;
		}
		portEXIT_CRITICAL_ISR(&peerNameLookupMux);

		if (completesPeerLookup && success && isFriendlyPeerName(resolvedName)) {
			// Cache only if that exact address is still the connected peer.
			portENTER_CRITICAL_ISR(&cachedPeerAddressMux);
			if (bluetoothSourceConnected
				&& memcmp(cachedPeerAddress, param->read_rmt_name.bda, ESP_BD_ADDR_LEN) == 0) {
				strncpy(cachedPeerName, resolvedName, ESP_BT_GAP_MAX_BDNAME_LEN);
				cachedPeerName[ESP_BT_GAP_MAX_BDNAME_LEN] = '\0';
			}
			portEXIT_CRITICAL_ISR(&cachedPeerAddressMux);
		}

		if (completesPeerLookup) {
			Bluetooth_RestoreLibraryCallback();
		}

	} else if (event == ESP_BT_GAP_DISC_STATE_CHANGED_EVT) {
		if (param->disc_st_chg.state == ESP_BT_GAP_DISCOVERY_STOPPED) {
			// Inquiry stopped naturally. Release the scan's need for the interceptor;
			// a targeted peer-name lookup may intentionally keep it installed.
			scanInProgress = false;
			Bluetooth_RestoreLibraryCallback();
			Log_Println("Bluetooth => Device discovery stopped (natural).", LOGLEVEL_NOTICE);
			Web_SendWebsocketData(0, WebsocketCodeType::BluetoothScanComplete);
		} else if (param->disc_st_chg.state == ESP_BT_GAP_DISCOVERY_STARTED) {
			Log_Println("Bluetooth => Device discovery started.", LOGLEVEL_NOTICE);
		}
	}

	// Always forward to the library's own handler to keep its internal state
	// consistent, regardless of whether our interceptor remains installed.
	ccall_app_gap_callback(event, param);
}

// Restores the library callback when neither a manual discovery scan nor a
// targeted peer-name lookup still needs our interceptor. Safe to call multiple
// times (idempotent).
static void Bluetooth_RestoreLibraryCallback() {
	if (scanInProgress || peerNameLookupPending) {
		return;
	}

	if (interceptorRegistered.exchange(false)) {
		esp_bt_gap_register_callback(ccall_app_gap_callback);
	}
}

// Resolve the friendly name for one exact connected MAC. Unlike the HTTP status
// getter this runs only as part of the Bluetooth connection lifecycle.
static void Bluetooth_RequestPeerName(const esp_bd_addr_t address) {
	if (!isValidBdAddr(address)) {
		return;
	}

	bool startLookup = false;
	portENTER_CRITICAL(&peerNameLookupMux);
	if (!peerNameLookupPending) {
		memcpy(peerNameLookupAddress, address, ESP_BD_ADDR_LEN);
		peerNameLookupPending = true;
		startLookup = true;
	}
	portEXIT_CRITICAL(&peerNameLookupMux);

	if (!startLookup) {
		return;
	}

	if (!interceptorRegistered.exchange(true)) {
		const esp_err_t callbackErr = esp_bt_gap_register_callback(gap_callback_interceptor);
		if (callbackErr != ESP_OK) {
			Log_Printf(LOGLEVEL_NOTICE, "Bluetooth => failed to install GAP interceptor for remote name: %s", esp_err_to_name(callbackErr));
			Bluetooth_CancelPeerNameLookup();
			return;
		}
	}

	// ESP-IDF declares esp_bt_gap_read_remote_name() with a mutable
	// esp_bd_addr_t parameter. Keep this helper const-correct and pass a
	// local copy to the IDF API instead of casting away constness.
	esp_bd_addr_t remoteAddress = {0};
	memcpy(remoteAddress, address, ESP_BD_ADDR_LEN);
	const esp_err_t err = esp_bt_gap_read_remote_name(remoteAddress);
	if (err != ESP_OK) {
		Log_Printf(LOGLEVEL_NOTICE, "Bluetooth => remote-name request failed: %s", esp_err_to_name(err));
		Bluetooth_CancelPeerNameLookup();
	}
}

static void Bluetooth_CancelPeerNameLookup() {
	portENTER_CRITICAL(&peerNameLookupMux);
	memset(peerNameLookupAddress, 0, ESP_BD_ADDR_LEN);
	peerNameLookupPending = false;
	portEXIT_CRITICAL(&peerNameLookupMux);
	Bluetooth_RestoreLibraryCallback();
}
#endif

#ifdef BLUETOOTH_ENABLE
void connection_state_changed(esp_a2d_connection_state_t state, void *ptr) {
	Log_Printf(LOGLEVEL_INFO, "Bluetooth %s => connection state: %s (Free heap: %u Bytes)", getType(), ((BluetoothA2DPCommon *) ptr)->to_str(state), ESP.getFreeHeap());
	if (System_GetOperationMode() == OPMODE_BLUETOOTH_SINK) {
		gPlayProperties.isWebstream = false;
		gPlayProperties.pausePlay = false;
		gPlayProperties.playlistFinished = true;
	} else if (System_GetOperationMode() == OPMODE_BLUETOOTH_SOURCE) {
		// CONNECTING/DISCONNECTING are transient states. Treating them as a real
		// disconnect would clear peer identity and schedule retries while the stack
		// is still completing the current operation.
		if (state != ESP_A2D_CONNECTION_STATE_CONNECTED && state != ESP_A2D_CONNECTION_STATE_DISCONNECTED) {
			return;
		}

		const bool connected = (state == ESP_A2D_CONNECTION_STATE_CONNECTED);
		const bool wasConnected = bluetoothSourceConnected;

		if (!connected && wasConnected) {
			Bluetooth_Source_FlushRingbuffer();
		}

		if (connected) {
			AudioPlayer_SetupVolumeAndAmps();

			// connect_to(address) does not reliably update ESP32-A2DP's
			// get_last_peer_address(). Prefer the exact target selected by ESPuino;
			// fall back to the library address for reconnect paths where no target
			// was selected by us.
			esp_bd_addr_t peerAddress = {0};
			esp_bd_addr_t targetAddress = {0};
			char targetName[ESP_BT_GAP_MAX_BDNAME_LEN + 1] = {0};
			const bool hasTarget = Bluetooth_GetConnectionTarget(targetAddress, targetName, sizeof(targetName));
			if (hasTarget) {
				memcpy(peerAddress, targetAddress, ESP_BD_ADDR_LEN);
			} else {
				memcpy(peerAddress, a2dp_source->get_last_peer_address(), ESP_BD_ADDR_LEN);
			}

			portENTER_CRITICAL(&cachedPeerAddressMux);
			memcpy(cachedPeerAddress, peerAddress, ESP_BD_ADDR_LEN);
			cachedPeerName[0] = '\0';
			if (hasTarget && memcmp(targetAddress, peerAddress, ESP_BD_ADDR_LEN) == 0 && isFriendlyPeerName(targetName)) {
				strncpy(cachedPeerName, targetName, ESP_BT_GAP_MAX_BDNAME_LEN);
				cachedPeerName[ESP_BT_GAP_MAX_BDNAME_LEN] = '\0';
			}
			bluetoothSourceConnected = true;
			portEXIT_CRITICAL(&cachedPeerAddressMux);

			if (isValidBdAddr(peerAddress)) {
				Log_Printf(LOGLEVEL_INFO, "Bluetooth => connected, cached peer: %02X:%02X:%02X:%02X:%02X:%02X",
					peerAddress[0], peerAddress[1], peerAddress[2],
					peerAddress[3], peerAddress[4], peerAddress[5]);
			} else {
				Log_Println("Bluetooth => connected, but peer address is unavailable", LOGLEVEL_NOTICE);
			}

			// Connection succeeded — clear retry/manual target state.
			manualConnectPending = false;
			manualDisconnectPending = false;
			connectRetryPending = false;
			connectRetryCount = 0;
			Bluetooth_ClearConnectionTarget();

			// The A2DP library can keep its own GAP inquiry running during auto-reconnect.
			// Stop discovery as soon as the source is connected so inquiry traffic does
			// not compete with the newly started audio stream. Manual web scans still
			// use Bluetooth_StopScan() so their UI/callback state is cleaned up as before.
			if (scanInProgress) {
				Bluetooth_StopScan();
			} else {
				const esp_err_t cancelResult = esp_bt_gap_cancel_discovery();
				if (cancelResult == ESP_OK) {
					Log_Println("Bluetooth => Device discovery stopped after connect.", LOGLEVEL_NOTICE);
				} else if (cancelResult != ESP_ERR_INVALID_STATE) {
					Log_Printf(LOGLEVEL_NOTICE, "Bluetooth => failed to stop discovery after connect: %s", esp_err_to_name(cancelResult));
				}
			}

			// If discovery/selection did not already give us a trustworthy friendly
			// name, resolve it once from this exact connected MAC. The result is
			// cached asynchronously and will appear on the next status poll.
			if (!(hasTarget && isFriendlyPeerName(targetName)) && isValidBdAddr(peerAddress)) {
				Bluetooth_RequestPeerName(peerAddress);
			}
		} else {
			// A lookup for a peer that is no longer connected must not survive into
			// the next connection and accidentally populate its name.
			Bluetooth_CancelPeerNameLookup();

			// Publish disconnect + cleared peer data atomically to status readers.
			portENTER_CRITICAL(&cachedPeerAddressMux);
			bluetoothSourceConnected = false;
			memset(cachedPeerAddress, 0, ESP_BD_ADDR_LEN);
			cachedPeerName[0] = '\0';
			portEXIT_CRITICAL(&cachedPeerAddressMux);

			// Disconnecting the old peer before a user-selected device is expected
			// and must not be counted as a failed connection attempt. The queued
			// request will start its initial connect from Bluetooth_Cyclic().
			if (manualDisconnectPending.exchange(false)) {
				connectRetryPending = false;
				connectRetryCount = 0;
				Bluetooth_ClearConnectionTarget();
				Log_Println("Bluetooth => current device disconnected, manual connection remains queued", LOGLEVEL_INFO);
			} else if (manualConnectPending && connectRetryCount < CONNECT_MAX_RETRIES) {
				// Count retries when connect_to() is actually issued, not when the
				// preceding attempt fails. This keeps CONNECT_MAX_RETRIES equal to the
				// number of real retry attempts. Ignore duplicate disconnect callbacks
				// while the same retry is already pending.
				if (!connectRetryPending) {
					connectRetryPending = true;
					connectRetryTimestamp = millis();
					Log_Printf(LOGLEVEL_INFO, "Bluetooth => connection failed, retry %u/%u in %u ms",
						connectRetryCount + 1, CONNECT_MAX_RETRIES, CONNECT_RETRY_DELAY_MS);
				}
			} else if (manualConnectPending && connectRetryCount >= CONNECT_MAX_RETRIES) {
				Log_Println("Bluetooth => all connection retries exhausted, giving up", LOGLEVEL_NOTICE);
				manualConnectPending = false;
				connectRetryPending = false;
				connectRetryCount = 0;
				Bluetooth_ClearConnectionTarget();
				AudioPlayer_SetupVolumeAndAmps();
			} else {
				// A non-manual attempt either failed or a real connection dropped.
				// Do not leave a stale auto-connect target behind for a future peer.
				Bluetooth_ClearConnectionTarget();
				if (wasConnected) {
					AudioPlayer_SetupVolumeAndAmps();
				}
			}
		}
	}
}
#endif

#ifdef BLUETOOTH_ENABLE
void audio_state_changed(esp_a2d_audio_state_t state, void *ptr) {
	Log_Printf(LOGLEVEL_INFO, "Bluetooth %s => audio state: %s (Free heap: %u Bytes)", getType(), ((BluetoothA2DPCommon *) ptr)->to_str(state), ESP.getFreeHeap());
	if (System_GetOperationMode() == OPMODE_BLUETOOTH_SINK) {
		gPlayProperties.pausePlay = (state != ESP_A2D_AUDIO_STATE_STARTED);
		gPlayProperties.playlistFinished = false;
		gPlayProperties.isWebstream = true;
	}
}
#endif

#ifdef BLUETOOTH_ENABLE
void button_handler(uint8_t id, bool isReleased) {
	if (isReleased) {
		switch (id) {
			case 70:
			case 68:
				Log_Printf(LOGLEVEL_DEBUG, "Bluetooth button id %u (pause/resume) is released.", id);
				AudioPlayer_SetTrackControl(PAUSEPLAY);
				break;
			case 75:
				Log_Printf(LOGLEVEL_DEBUG, "Bluetooth button id %u (next track) is released.", id);
				AudioPlayer_SetTrackControl(NEXTTRACK);
				break;
			case 76:
				Log_Printf(LOGLEVEL_DEBUG, "Bluetooth button id %u (previous track) is released.", id);
				AudioPlayer_SetTrackControl(PREVIOUSTRACK);
				break;
			default:
				Log_Printf(LOGLEVEL_DEBUG, "Unknown bluetooth button id %u is released.", id);
				break;
		}
	}
}
#endif

#ifdef BLUETOOTH_ENABLE
void avrc_metadata_callback(uint8_t id, const uint8_t *text) {
	if (strlen((char *) text) == 0) {
		return;
	}
	switch (id) {
		case ESP_AVRC_MD_ATTR_TITLE:
			Log_Printf(LOGLEVEL_DEBUG, "Bluetooth => AVRC Title: %s", text);
			break;
		case ESP_AVRC_MD_ATTR_ARTIST:
			Log_Printf(LOGLEVEL_DEBUG, "Bluetooth => AVRC Artist: %s", text);
			break;
		case ESP_AVRC_MD_ATTR_ALBUM:
			Log_Printf(LOGLEVEL_DEBUG, "Bluetooth => AVRC Album: %s", text);
			break;
		case ESP_AVRC_MD_ATTR_TRACK_NUM:
			Log_Printf(LOGLEVEL_DEBUG, "Bluetooth => AVRC Track-No: %s", text);
			break;
		case ESP_AVRC_MD_ATTR_NUM_TRACKS:
			Log_Printf(LOGLEVEL_DEBUG, "Bluetooth => AVRC Number of tracks: %s", text);
			break;
		case ESP_AVRC_MD_ATTR_GENRE:
			Log_Printf(LOGLEVEL_DEBUG, "Bluetooth => AVRC Genre: %s", text);
			break;
		default:
			Log_Printf(LOGLEVEL_DEBUG, "Bluetooth => AVRC metadata rsp: attribute id 0x%x, %s", id, text);
			break;
	}
}
#endif

#ifdef BLUETOOTH_ENABLE
int32_t get_data_channels(Frame *frame, int32_t channel_len) {
	if (channel_len <= 0 || frame == NULL || audioSourceRingBuffer == NULL) {
		return 0;
	}

	const size_t bytes_per_frame = 2 * sizeof(int16_t); // ch1 + ch2, 16-bit each
	const size_t bytes_needed = (size_t) channel_len * bytes_per_frame;

	// --- Gate on actual data available, before touching the buffer ---
	// uxItemsWaiting is the number of bytes currently queued for a
	// no-split ring buffer. If there isn't a full frame's worth sitting
	// there, bail out to silence instead of blocking / partially filling.
	size_t bytes_waiting = 0;
	vRingbufferGetInfo(audioSourceRingBuffer, NULL, NULL, NULL, NULL, &bytes_waiting);

	if (bytes_waiting < bytes_needed) {
		memset(frame, 0, channel_len * sizeof(Frame));
		return channel_len;
	}

	// --- Pull the data, handling one possible wrap-around ---
	// A no-split buffer returns at most the contiguous run up to the
	// physical end of the buffer. Since we've already confirmed enough
	// total bytes are waiting, a short read here means we hit the wrap
	// boundary, not that data is missing — read again to get the rest.
	int32_t samples_received = 0;
	for (int reads = 0; reads < 2 && samples_received < channel_len; ++reads) {
		size_t sampleSize = 0;
		size_t bytes_left = bytes_needed - (size_t) samples_received * bytes_per_frame;

		uint8_t *sampleBuff = (uint8_t *) xRingbufferReceiveUpTo(
			audioSourceRingBuffer,
			&sampleSize,
			0,
			bytes_left);

		if (sampleBuff == NULL) {
			break; // shouldn't happen given the pre-check, but stay safe
		}

		int32_t chunk_samples = sampleSize / bytes_per_frame;
		int16_t *raw_samples = (int16_t *) sampleBuff;

		for (int32_t i = 0; i < chunk_samples; ++i) {
			frame[samples_received + i].channel1 = raw_samples[i * 2];
			frame[samples_received + i].channel2 = raw_samples[i * 2 + 1];
		}

		samples_received += chunk_samples;
		vRingbufferReturnItem(audioSourceRingBuffer, (void *) sampleBuff);

		if (sampleSize == bytes_left) {
			break; // got the full amount in one contiguous chunk, no wrap
		}
		// else: short read == we hit the wrap boundary, loop once more
	}

	if (samples_received < channel_len) {
		memset(&frame[samples_received], 0, (channel_len - samples_received) * sizeof(Frame));
	}

	return channel_len;
}
#endif

#ifdef BLUETOOTH_ENABLE
void rssi(esp_bt_gap_cb_param_t::read_rssi_delta_param &rssiParam) {
	Log_Printf(LOGLEVEL_DEBUG, "Bluetooth => RSSI value: %d", rssiParam.rssi_delta);
}
#endif

#ifdef BLUETOOTH_ENABLE
// Returns true to auto-connect, false to keep scanning.
// Suppressed while a manual scan or manual connect is in progress.
bool scan_bluetooth_device_callback(const char *ssid, esp_bd_addr_t address, int rssi) {
	if (scanInProgress || pendingConnect || manualConnectPending) {
		return false;
	}

	Log_Printf(LOGLEVEL_INFO, "Bluetooth source => Device found: %s (%02X:%02X:%02X:%02X:%02X:%02X)",
		ssid, address[0], address[1], address[2], address[3], address[4], address[5]);

	bool shouldConnect = false;
	if (btDeviceName == "") {
		shouldConnect = true;
	} else {
		esp_bd_addr_t addr;
		if (sscanf(btDeviceName.c_str(), "%hhX:%hhX:%hhX:%hhX:%hhX:%hhX", &addr[0], &addr[1], &addr[2], &addr[3], &addr[4], &addr[5]) == 6) {
			shouldConnect = (memcmp(address, addr, ESP_BD_ADDR_LEN) == 0);
		} else {
			shouldConnect = (ssid != nullptr && startsWith(ssid, btDeviceName.c_str()));
		}
	}

	if (shouldConnect) {
		// Bind the exact address (and name, if available) to the upcoming
		// connection. This is more reliable than consulting last_peer_address later.
		Bluetooth_SetConnectionTarget(address, ssid);
	}
	return shouldConnect;
}
#endif

#ifdef BLUETOOTH_ENABLE
static uint8_t mapRounded(uint32_t x, uint32_t in_min, uint32_t in_max, uint32_t out_min, uint32_t out_max) {
	uint32_t divisor = in_max - in_min;
	if (divisor == 0) {
		return out_min;
	}
	return ((x - in_min) * (out_max - out_min) + (divisor / 2)) / divisor + out_min;
}
#endif

void Bluetooth_VolumeChanged(int _newVolume) {
#ifdef BLUETOOTH_ENABLE
	if ((_newVolume < int32_t(BLUETOOTH_A2DP_VOLUME_MIN)) || (_newVolume > BLUETOOTH_A2DP_VOLUME_MAX)) {
		return;
	}
	uint8_t _volume = mapRounded(_newVolume, BLUETOOTH_A2DP_VOLUME_MIN, BLUETOOTH_A2DP_VOLUME_MAX, AUDIOPLAYER_VOLUME_MIN, AUDIOPLAYER_VOLUME_MAX);
	if (AudioPlayer_GetCurrentVolume() != _volume) {
		Log_Printf(LOGLEVEL_INFO, "Bluetooth => volume changed:  %d !", _volume);
		AudioPlayer_SetVolume(_volume);
	}
#endif
}

#ifdef BLUETOOTH_ENABLE
void Bluetooth_StartScan() {
	if (System_GetOperationMode() != OPMODE_BLUETOOTH_SOURCE || !a2dp_source) {
		Log_Println("Bluetooth_StartScan: not in source mode or source not initialized", LOGLEVEL_ERROR);
		return;
	}
	if (scanInProgress) {
		Log_Println("Bluetooth_StartScan: scan already in progress, ignoring", LOGLEVEL_INFO);
		return;
	}

	// Capture connected device so it stays at the top of the list during scan.
	// Use cachedPeerAddress (set in connection_state_changed) rather than
	// get_last_peer_address() which can return all-zeros at this point.
	ScannedBluetoothDevice connectedDev;
	char connectedPeerName[ESP_BT_GAP_MAX_BDNAME_LEN + 1] = {0};
	bool wasConnected = false;
	portENTER_CRITICAL(&cachedPeerAddressMux);
	wasConnected = bluetoothSourceConnected;
	if (wasConnected) {
		memcpy(connectedDev.address, cachedPeerAddress, ESP_BD_ADDR_LEN);
		strncpy(connectedPeerName, cachedPeerName, ESP_BT_GAP_MAX_BDNAME_LEN);
		connectedPeerName[ESP_BT_GAP_MAX_BDNAME_LEN] = '\0';
	}
	portEXIT_CRITICAL(&cachedPeerAddressMux);
	if (wasConnected) {
		if (!isValidBdAddr(connectedDev.address)) {
			Log_Println("Bluetooth_StartScan => WARNING: connected but cachedPeerAddress is all-zeros, skipping pre-population", LOGLEVEL_NOTICE);
			wasConnected = false; // treat as not connected to avoid inserting a zero-address entry
		} else {
			// Never use btDeviceName blindly here: it may contain the configured
			// target MAC address, which must not be presented as a friendly name.
			const char *displayName = connectedPeerName[0] != '\0' ? connectedPeerName : "Connected Device";
			strncpy(connectedDev.name, displayName, ESP_BT_GAP_MAX_BDNAME_LEN);
			connectedDev.name[ESP_BT_GAP_MAX_BDNAME_LEN] = '\0';
			connectedDev.rssi = 0;
			Log_Printf(LOGLEVEL_INFO, "Bluetooth_StartScan => pre-populating connected device: %s (%02X:%02X:%02X:%02X:%02X:%02X)",
				connectedDev.name,
				connectedDev.address[0], connectedDev.address[1], connectedDev.address[2],
				connectedDev.address[3], connectedDev.address[4], connectedDev.address[5]);
		}
	}

	portENTER_CRITICAL(&scannedDevicesMux);
	scannedDevices.clear();
	if (wasConnected) {
		scannedDevices.push_back(connectedDev);
	}
	portEXIT_CRITICAL(&scannedDevicesMux);

	// Publish the scan state before touching callback ownership. If a targeted
	// remote-name result completes concurrently, it must see that the scan still
	// needs the interceptor and therefore must not restore the library callback.
	scanInProgress = true;
	if (!interceptorRegistered.exchange(true)) {
		const esp_err_t callbackErr = esp_bt_gap_register_callback(gap_callback_interceptor);
		if (callbackErr != ESP_OK) {
			interceptorRegistered = false;
			scanInProgress = false;
			Log_Printf(LOGLEVEL_ERROR, "Bluetooth => failed to install GAP interceptor: %s", esp_err_to_name(callbackErr));
			Web_SendWebsocketData(0, WebsocketCodeType::BluetoothScanComplete);
			return;
		}
	}

	scanStartTimestamp = millis();

	Log_Println("Bluetooth => Starting device discovery...", LOGLEVEL_NOTICE);
	// Duration: 10 * 1.28 s = 12.8 s
	esp_err_t err = esp_bt_gap_start_discovery(ESP_BT_INQ_MODE_GENERAL_INQUIRY, 10, 0);
	if (err != ESP_OK) {
		Log_Printf(LOGLEVEL_ERROR, "Bluetooth => esp_bt_gap_start_discovery failed: %s (connected=%d, heapFree=%u)",
			esp_err_to_name(err), (int) bluetoothSourceConnected, ESP.getFreeHeap());
		scanInProgress = false;
		Bluetooth_RestoreLibraryCallback();
		// Still notify the UI so it doesn't hang waiting for a completion that will never arrive.
		// The connected device was already pre-populated above (if applicable), so the
		// list is as complete as it can be.
		Web_SendWebsocketData(0, WebsocketCodeType::BluetoothScanComplete);
	}
}

static void Bluetooth_StopScan() {
	if (!scanInProgress) {
		return;
	}
	// Clear flag BEFORE cancel so a re-entrant DISC_STATE_CHANGED_EVT triggered
	// by cancel does not recurse into this function via Cyclic().
	scanInProgress = false;

	// Cancel the ongoing inquiry; the resulting DISC_STATE_CHANGED_EVT will be
	// forwarded to the library by gap_callback_interceptor (which is still
	// registered at this point) and the library callback will be restored there.
	esp_bt_gap_cancel_discovery();

	// Restore callback here as a safety net in case cancel fires no callback
	// (e.g. inquiry already ended between our flag-check and cancel call).
	Bluetooth_RestoreLibraryCallback();

	Log_Println("Bluetooth => Device discovery stopped (forced).", LOGLEVEL_NOTICE);
	Web_SendWebsocketData(0, WebsocketCodeType::BluetoothScanComplete);
}

void Bluetooth_ConnectToAddress(esp_bd_addr_t address) {
	if (System_GetOperationMode() != OPMODE_BLUETOOTH_SOURCE || !a2dp_source) {
		Log_Println("Bluetooth_ConnectToAddress: not in source mode or source not initialized", LOGLEVEL_ERROR);
		return;
	}

	// Capture the friendly name for this exact address while it is still present
	// in the scan snapshot. Do not use the persisted btDeviceName as peer identity.
	char selectedName[ESP_BT_GAP_MAX_BDNAME_LEN + 1] = {0};
	portENTER_CRITICAL(&scannedDevicesMux);
	for (const auto &d : scannedDevices) {
		if (memcmp(d.address, address, ESP_BD_ADDR_LEN) == 0) {
			if (isFriendlyPeerName(d.name)) {
				strncpy(selectedName, d.name, ESP_BT_GAP_MAX_BDNAME_LEN);
				selectedName[ESP_BT_GAP_MAX_BDNAME_LEN] = '\0';
			}
			break;
		}
	}
	portEXIT_CRITICAL(&scannedDevicesMux);

	if (selectedName[0] != '\0') {
		btDeviceName = selectedName;
		gPrefsSettings.putString("btDeviceName", btDeviceName);
		Log_Printf(LOGLEVEL_INFO, "Bluetooth => set preferred device name: %s", btDeviceName.c_str());
	}

	// Queue address + name together. Retry/connection state is changed only by
	// Bluetooth_Cyclic() and the Bluetooth callback, not from the web-server task.
	// The connection target becomes active only when the attempt actually starts.
	portENTER_CRITICAL(&pendingConnectMux);
	memcpy(pendingConnectAddress, address, ESP_BD_ADDR_LEN);
	strncpy(pendingConnectName, selectedName, ESP_BT_GAP_MAX_BDNAME_LEN);
	pendingConnectName[ESP_BT_GAP_MAX_BDNAME_LEN] = '\0';
	pendingConnect = true;
	portEXIT_CRITICAL(&pendingConnectMux);
}

std::vector<ScannedBluetoothDevice> Bluetooth_GetScannedDevices() {
	// Returns a BY-VALUE snapshot so the caller never races with concurrent
	// modifications from the BT task.  The copy is made inside the spinlock so
	// it is always consistent.  Callers must NOT hold scannedDevicesMux when
	// calling this function.

	if (System_GetOperationMode() == OPMODE_BLUETOOTH_SOURCE) {
		bool connected = false;
		esp_bd_addr_t currentAddr = {0};
		char currentPeerName[ESP_BT_GAP_MAX_BDNAME_LEN + 1] = {0};
		portENTER_CRITICAL(&cachedPeerAddressMux);
		connected = bluetoothSourceConnected;
		if (connected) {
			memcpy(currentAddr, cachedPeerAddress, ESP_BD_ADDR_LEN);
			strncpy(currentPeerName, cachedPeerName, ESP_BT_GAP_MAX_BDNAME_LEN);
			currentPeerName[ESP_BT_GAP_MAX_BDNAME_LEN] = '\0';
		}
		portEXIT_CRITICAL(&cachedPeerAddressMux);

		if (connected && !isValidBdAddr(currentAddr)) {
			Log_Println("Bluetooth_GetScannedDevices => WARNING: bluetoothSourceConnected=true but cachedPeerAddress is all-zeros", LOGLEVEL_NOTICE);
		} else if (connected) {
			// Inject / promote the connected device under the spinlock so the
			// snapshot below always includes it at position 0.
			portENTER_CRITICAL(&scannedDevicesMux);
			auto it = std::find_if(scannedDevices.begin(), scannedDevices.end(), [&](const ScannedBluetoothDevice &d) {
				return memcmp(d.address, currentAddr, ESP_BD_ADDR_LEN) == 0;
			});

			if (it == scannedDevices.end()) {
				ScannedBluetoothDevice dev;
				memcpy(dev.address, currentAddr, ESP_BD_ADDR_LEN);
				const char *displayName = currentPeerName[0] != '\0' ? currentPeerName : "Connected Device";
				strncpy(dev.name, displayName, ESP_BT_GAP_MAX_BDNAME_LEN);
				dev.name[ESP_BT_GAP_MAX_BDNAME_LEN] = '\0';
				dev.rssi = 0;
				scannedDevices.insert(scannedDevices.begin(), dev);
				Log_Printf(LOGLEVEL_INFO, "Bluetooth_GetScannedDevices => injected connected device at top: %s (%02X:%02X:%02X:%02X:%02X:%02X)",
					dev.name, currentAddr[0], currentAddr[1], currentAddr[2],
					currentAddr[3], currentAddr[4], currentAddr[5]);
			} else {
				// Repair stale placeholder/MAC-as-name entries from a previous
				// connection before returning them to the UI.
				if (currentPeerName[0] != '\0'
					&& (strcmp(it->name, "Unknown") == 0
						|| strcmp(it->name, "Connected Device") == 0
						|| isMacAddressString(it->name))) {
					strncpy(it->name, currentPeerName, ESP_BT_GAP_MAX_BDNAME_LEN);
					it->name[ESP_BT_GAP_MAX_BDNAME_LEN] = '\0';
				} else if (isMacAddressString(it->name)) {
					strncpy(it->name, "Connected Device", ESP_BT_GAP_MAX_BDNAME_LEN);
					it->name[ESP_BT_GAP_MAX_BDNAME_LEN] = '\0';
				}

				if (it != scannedDevices.begin()) {
					ScannedBluetoothDevice dev = *it;
					scannedDevices.erase(it);
					scannedDevices.insert(scannedDevices.begin(), dev);
					Log_Printf(LOGLEVEL_INFO, "Bluetooth_GetScannedDevices => moved connected device to top: %s", dev.name);
				}
			}
			portEXIT_CRITICAL(&scannedDevicesMux);
		}
	}

	// Take a protected snapshot — the spinlock is held only for the duration of
	// the copy (3 POD structs ≈ microseconds), then released before returning.
	portENTER_CRITICAL(&scannedDevicesMux);
	std::vector<ScannedBluetoothDevice> snapshot(scannedDevices);
	portEXIT_CRITICAL(&scannedDevicesMux);

	Log_Printf(LOGLEVEL_INFO, "Bluetooth_GetScannedDevices => returning %u device(s)", snapshot.size());
	return snapshot;
}

bool Bluetooth_GetConnectedSourceInfo(String &name, String &address) {
	name = "";
	address = "";

	if (System_GetOperationMode() != OPMODE_BLUETOOTH_SOURCE) {
		return false;
	}

	// Take connection state, address and cached name in one critical section.
	// Everything below is read-only; this getter never changes GAP callbacks,
	// starts lookups or reads/writes Bluetooth preferences.
	bool connected = false;
	esp_bd_addr_t peerAddress = {0};
	char peerName[ESP_BT_GAP_MAX_BDNAME_LEN + 1] = {0};
	portENTER_CRITICAL(&cachedPeerAddressMux);
	connected = bluetoothSourceConnected;
	if (connected) {
		memcpy(peerAddress, cachedPeerAddress, ESP_BD_ADDR_LEN);
		strncpy(peerName, cachedPeerName, ESP_BT_GAP_MAX_BDNAME_LEN);
		peerName[ESP_BT_GAP_MAX_BDNAME_LEN] = '\0';
	}
	portEXIT_CRITICAL(&cachedPeerAddressMux);

	if (!connected) {
		return false;
	}

	if (isValidBdAddr(peerAddress)) {
		char addrStr[18];
		snprintf(addrStr, sizeof(addrStr), "%02X:%02X:%02X:%02X:%02X:%02X",
			peerAddress[0], peerAddress[1], peerAddress[2],
			peerAddress[3], peerAddress[4], peerAddress[5]);
		address = addrStr;
	}

	if (isFriendlyPeerName(peerName)) {
		name = peerName;
	} else if (isValidBdAddr(peerAddress)) {
		// A scan may have learned the name after the connection snapshot was
		// created. Only accept a name associated with this exact MAC address.
		char scannedName[ESP_BT_GAP_MAX_BDNAME_LEN + 1] = {0};
		portENTER_CRITICAL(&scannedDevicesMux);
		for (const auto &d : scannedDevices) {
			if (memcmp(d.address, peerAddress, ESP_BD_ADDR_LEN) == 0 && isFriendlyPeerName(d.name)) {
				strncpy(scannedName, d.name, ESP_BT_GAP_MAX_BDNAME_LEN);
				scannedName[ESP_BT_GAP_MAX_BDNAME_LEN] = '\0';
				break;
			}
		}
		portEXIT_CRITICAL(&scannedDevicesMux);
		if (scannedName[0] != '\0') {
			name = scannedName;
		}
	}

	return true;
}
#endif

void Bluetooth_Init(void) {
#ifdef BLUETOOTH_ENABLE
	portENTER_CRITICAL(&cachedPeerAddressMux);
	bluetoothSourceConnected = false;
	memset(cachedPeerAddress, 0, ESP_BD_ADDR_LEN);
	cachedPeerName[0] = '\0';
	portEXIT_CRITICAL(&cachedPeerAddressMux);
	Bluetooth_ClearConnectionTarget();
	Bluetooth_CancelPeerNameLookup();
	if (System_GetOperationMode() == OPMODE_BLUETOOTH_SINK) {
		a2dp_sink = new BluetoothA2DPSink();
	#if (defined(ESP_ARDUINO_VERSION_MAJOR) && (ESP_ARDUINO_VERSION_MAJOR >= 3))
		i2s.setPins(I2S_BCLK, I2S_LRC, I2S_DOUT);
		if (!i2s.begin(I2S_MODE_STD, 44100, I2S_DATA_BIT_WIDTH_16BIT, I2S_SLOT_MODE_STEREO, I2S_STD_SLOT_BOTH)) {
			Log_Println("Failed to initialize I2S!", LOGLEVEL_ERROR);
			while (1)
				;
		}
		a2dp_sink->set_output(i2s);
	#else
		i2s_pin_config_t pin_config = {
		#if ESP_IDF_VERSION >= ESP_IDF_VERSION_VAL(4, 0, 0)
			.mck_io_num = 0,
		#endif
			.bck_io_num = I2S_BCLK,
			.ws_io_num = I2S_LRC,
			.data_out_num = I2S_DOUT,
			.data_in_num = I2S_PIN_NO_CHANGE,
		};
		a2dp_sink->set_pin_config(pin_config);
	#endif
		a2dp_sink->set_rssi_callback(rssi);
		a2dp_sink->activate_pin_code(false);
		if (gPrefsSettings.getBool("playMono", false)) {
			a2dp_sink->set_mono_downmix(true);
		}
		a2dp_sink->set_auto_reconnect(true);
		a2dp_sink->set_rssi_active(true);
		a2dp_sink->start(nameBluetoothSinkDevice);
		Log_Printf(LOGLEVEL_INFO, "Bluetooth sink started, Device: %s", nameBluetoothSinkDevice);
		a2dp_sink->set_on_connection_state_changed(connection_state_changed, a2dp_sink);
		a2dp_sink->set_on_audio_state_changed(audio_state_changed, a2dp_sink);
		a2dp_sink->set_avrc_metadata_callback(avrc_metadata_callback);
		a2dp_sink->set_on_volumechange(Bluetooth_VolumeChanged);
	} else if (System_GetOperationMode() == OPMODE_BLUETOOTH_SOURCE) {
		audioSourceRingBuffer = nullptr;

		a2dp_source = new BluetoothA2DPSource();
		if (!a2dp_source) {
			Log_Println("Failed to create BluetoothA2DPSource object!", LOGLEVEL_ERROR);
			return;
		}

		a2dp_source->set_auto_reconnect(true);
		a2dp_source->set_ssp_enabled(true);

		String btPinCode = gPrefsSettings.getString("btPinCode", "");
		if (btPinCode != "") {
			a2dp_source->set_pin_code(btPinCode.c_str(), ESP_BT_PIN_TYPE_VARIABLE);
		}
		a2dp_source->set_ssid_callback(scan_bluetooth_device_callback);
		a2dp_source->set_avrc_passthru_command_callback(button_handler);
		a2dp_source->set_data_callback_in_frames(get_data_channels);
		a2dp_source->start("ESPUINO");
		btDeviceName = "";
		if (gPrefsSettings.isKey("btDeviceName")) {
			btDeviceName = gPrefsSettings.getString("btDeviceName", "");
		}
		Log_Printf(LOGLEVEL_INFO, "Bluetooth source started, connect to device: '%s'", (btDeviceName == "") ? "connect to first device found" : btDeviceName.c_str());
		a2dp_source->set_on_connection_state_changed(connection_state_changed, a2dp_source);
		a2dp_source->set_on_audio_state_changed(audio_state_changed, a2dp_source);
		Bluetooth_SetVolume(AudioPlayer_GetCurrentVolume());
	} else {
		esp_bt_mem_release(ESP_BT_MODE_BTDM);
	}
#endif
}

void Bluetooth_Exit(void) {
#ifdef BLUETOOTH_ENABLE
	if (a2dp_sink || a2dp_source) {
		if (a2dp_sink) {
			Log_Println("shutdown Bluetooth sink..", LOGLEVEL_NOTICE);
			a2dp_sink = nullptr; // abandon, do NOT delete or call end()
		}
		if (a2dp_source) {
			Log_Println("shutdown Bluetooth source..", LOGLEVEL_NOTICE);
			a2dp_source = nullptr; // abandon, do NOT delete or call end()
		}
		portENTER_CRITICAL(&cachedPeerAddressMux);
		bluetoothSourceConnected = false;
		memset(cachedPeerAddress, 0, ESP_BD_ADDR_LEN);
		cachedPeerName[0] = '\0';
		portEXIT_CRITICAL(&cachedPeerAddressMux);
		manualConnectPending = false;
		manualDisconnectPending = false;
		connectRetryPending = false;
		connectRetryCount = 0;
		Bluetooth_ClearConnectionTarget();
		Bluetooth_CancelPeerNameLookup();
	}
#endif
}

void Bluetooth_Cyclic(void) {
#ifdef BLUETOOTH_ENABLE
	// ── Handle pending manual connect (deferred from Bluetooth_ConnectToAddress) ──
	bool doConnect = false;
	esp_bd_addr_t connectAddress = {0};
	char connectName[ESP_BT_GAP_MAX_BDNAME_LEN + 1] = {0};

	portENTER_CRITICAL(&pendingConnectMux);
	if (pendingConnect && !manualDisconnectPending) {
		doConnect = true;
		memcpy(connectAddress, pendingConnectAddress, ESP_BD_ADDR_LEN);
		strncpy(connectName, pendingConnectName, ESP_BT_GAP_MAX_BDNAME_LEN);
		connectName[ESP_BT_GAP_MAX_BDNAME_LEN] = '\0';
		memset(pendingConnectAddress, 0, ESP_BD_ADDR_LEN);
		pendingConnectName[0] = '\0';
		pendingConnect = false;
	}
	portEXIT_CRITICAL(&pendingConnectMux);

	if (doConnect) {
		// A newly queued request supersedes any previous manual attempt. Keep these
		// state transitions in the main Bluetooth cycle instead of the web task.
		connectRetryPending = false;
		connectRetryCount = 0;
		manualConnectPending = false;
		Bluetooth_ClearConnectionTarget();

		// Stop any ongoing scan first so inquiry doesn't compete with paging.
		if (scanInProgress) {
			Bluetooth_StopScan();
		}

		if (a2dp_source->is_connected()) {
			esp_bd_addr_t currentAddr = {0};
			portENTER_CRITICAL(&cachedPeerAddressMux);
			memcpy(currentAddr, cachedPeerAddress, ESP_BD_ADDR_LEN);
			portEXIT_CRITICAL(&cachedPeerAddressMux);

			if (isValidBdAddr(currentAddr) && memcmp(connectAddress, currentAddr, ESP_BD_ADDR_LEN) == 0) {
				Log_Println("Bluetooth => requested device is already connected", LOGLEVEL_INFO);
				// Refresh the cached friendly name if the scan learned one later.
				if (isFriendlyPeerName(connectName)) {
					portENTER_CRITICAL(&cachedPeerAddressMux);
					strncpy(cachedPeerName, connectName, ESP_BT_GAP_MAX_BDNAME_LEN);
					cachedPeerName[ESP_BT_GAP_MAX_BDNAME_LEN] = '\0';
					portEXIT_CRITICAL(&cachedPeerAddressMux);
				}
				manualConnectPending = false;
				connectRetryPending = false;
				connectRetryCount = 0;
				Bluetooth_ClearConnectionTarget();
				doConnect = false;
			} else {
				Log_Println("Bluetooth => disconnecting current device before new connection", LOGLEVEL_INFO);

				// Keep the user request queued while the old peer disconnects. Do not
				// mark the new connection as started yet: the resulting DISCONNECTED
				// event belongs to the old peer and must not consume a retry.
				portENTER_CRITICAL(&pendingConnectMux);
				memcpy(pendingConnectAddress, connectAddress, ESP_BD_ADDR_LEN);
				strncpy(pendingConnectName, connectName, ESP_BT_GAP_MAX_BDNAME_LEN);
				pendingConnectName[ESP_BT_GAP_MAX_BDNAME_LEN] = '\0';
				pendingConnect = true;
				portEXIT_CRITICAL(&pendingConnectMux);

				manualDisconnectPending = true;
				a2dp_source->disconnect();
				doConnect = false;
			}
		}

		if (doConnect) {
			manualDisconnectPending = false;
			manualConnectPending = true;
			memcpy(connectRetryAddress, connectAddress, ESP_BD_ADDR_LEN);
			connectRetryCount = 0;
			Bluetooth_SetConnectionTarget(connectAddress, connectName);
			Log_Printf(LOGLEVEL_INFO, "Bluetooth => connecting to %02X:%02X:%02X:%02X:%02X:%02X",
				connectAddress[0], connectAddress[1], connectAddress[2],
				connectAddress[3], connectAddress[4], connectAddress[5]);
			a2dp_source->connect_to(connectAddress);
		}
	}

	// ── Handle connection retries ────────────────────────────────────────────
	if (connectRetryPending && !bluetoothSourceConnected) {
		if (millis() - connectRetryTimestamp >= CONNECT_RETRY_DELAY_MS) {
			connectRetryPending = false;
			if (connectRetryCount < CONNECT_MAX_RETRIES) {
				connectRetryCount++;
				connectRetryTimestamp = millis();
				Log_Printf(LOGLEVEL_INFO, "Bluetooth => retry connect %u/%u to %02X:%02X:%02X:%02X:%02X:%02X",
					connectRetryCount, CONNECT_MAX_RETRIES,
					connectRetryAddress[0], connectRetryAddress[1], connectRetryAddress[2],
					connectRetryAddress[3], connectRetryAddress[4], connectRetryAddress[5]);
				a2dp_source->connect_to(connectRetryAddress);
			} else {
				Log_Println("Bluetooth => all retries exhausted", LOGLEVEL_NOTICE);
				manualConnectPending = false;
				connectRetryCount = 0;
				Bluetooth_ClearConnectionTarget();
			}
		}
	}

	// ── Sink: activity timer ──────────────────────────────────────────────────
	if ((System_GetOperationMode() == OPMODE_BLUETOOTH_SINK) && (a2dp_sink)) {
		if (a2dp_sink->get_audio_state() == ESP_A2D_AUDIO_STATE_STARTED) {
			System_UpdateActivityTimer();
		}
	}

	// ── Source: activity timer + scan timeout guard ───────────────────────────
	if ((System_GetOperationMode() == OPMODE_BLUETOOTH_SOURCE) && (a2dp_source)) {
		if (a2dp_source->get_audio_state() == ESP_A2D_AUDIO_STATE_STARTED) {
			System_UpdateActivityTimer();
		}
		if (scanInProgress) {
			uint32_t elapsed = millis() - scanStartTimestamp;
			if (elapsed > SCAN_TIMEOUT_MS + SCAN_TIMEOUT_GUARD_MS) {
				Log_Println("Bluetooth => scan timeout guard fired, forcing stop", LOGLEVEL_NOTICE);
				Bluetooth_StopScan();
			}
		}
	}
#endif
}

void Bluetooth_PlayPauseTrack(void) {
#ifdef BLUETOOTH_ENABLE
	if ((System_GetOperationMode() == OPMODE_BLUETOOTH_SINK) && (a2dp_sink)) {
		if (a2dp_sink->get_audio_state() == ESP_A2D_AUDIO_STATE_STARTED) {
			a2dp_sink->pause();
		} else {
			a2dp_sink->play();
		}
	}
#endif
}

void Bluetooth_NextTrack(void) {
#ifdef BLUETOOTH_ENABLE
	if ((System_GetOperationMode() == OPMODE_BLUETOOTH_SINK) && (a2dp_sink)) {
		a2dp_sink->next();
	}
#endif
}

void Bluetooth_PreviousTrack(void) {
#ifdef BLUETOOTH_ENABLE
	if ((System_GetOperationMode() == OPMODE_BLUETOOTH_SINK) && (a2dp_sink)) {
		a2dp_sink->previous();
	}
#endif
}

void Bluetooth_SetVolume(const int32_t _newVolume) {
#ifdef BLUETOOTH_ENABLE
	if (_newVolume < int32_t(AUDIOPLAYER_VOLUME_MIN)) {
		return;
	} else if (_newVolume > AUDIOPLAYER_VOLUME_MAX) {
		return;
	} else {
		const uint8_t volume = mapRounded(_newVolume, AUDIOPLAYER_VOLUME_MIN, AUDIOPLAYER_VOLUME_MAX, BLUETOOTH_A2DP_VOLUME_MIN, BLUETOOTH_A2DP_VOLUME_MAX);
		if (a2dp_sink) {
			a2dp_sink->set_volume(volume);
			Bluetooth_VolumeChanged(volume);
		} else if (a2dp_source) {
			// Source mode bypasses AudioPlayer::Gain(), so the A2DP library
			// must scale the outgoing raw PCM itself.
			a2dp_source->set_volume(volume);
		}
	}
#endif
}

uint8_t Bluetooth_GetCurrentVolume() {
#ifdef BLUETOOTH_ENABLE
	if (a2dp_sink) {
		auto current_volume = a2dp_sink->get_volume();
		return mapRounded(current_volume, BLUETOOTH_A2DP_VOLUME_MIN, BLUETOOTH_A2DP_VOLUME_MAX, AUDIOPLAYER_VOLUME_MIN, AUDIOPLAYER_VOLUME_MAX);
	}
	if (a2dp_source) {
		auto current_volume = a2dp_source->get_volume();
		return mapRounded(current_volume, BLUETOOTH_A2DP_VOLUME_MIN, BLUETOOTH_A2DP_VOLUME_MAX, AUDIOPLAYER_VOLUME_MIN, AUDIOPLAYER_VOLUME_MAX);
	}
#endif
	return 0;
}
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
